Infineon/voltage-regulator-learning-platform/Version1.0/RedesignV1.0.xlsx

Redesign Vreg V1.0
Fault description | Date | Priority | Correction on the current board | Correction V1.1 | Corrected in V1.1 | Comment
Drain and Source of Q201 are reversed | 2021-06-03 | High | Cut some traces and rewire correctly. See "RetrofitsV1.0" | Flip Q201 in Schematic and correct it in the layout | 2021-06-08
Switch1-3 don't turn Q740, Q742, Q744 completely off. This is because R740 and R750 (and the others respectively) form an undesired voltage divider | 2021-06-03 | Nice to have | Reduce R750-R752 to 4k7 | Same | 2021-06-19 | Uth,min=0.3V -> Rmax=10k -> 4k7 leaves enough margin
Reverse leakage current through D506 has significant influence on In_Curr_Filtr and Out_curr_Filtr | 2021-06-06 | High | Change R506 and R507 to 100k and C506 and C507 to 2.2uF | Same | 2021-06-19 | Board2: Used 1uF 200k because I didn't have 2.2uF
If only the Arduino is powered, it still outputs 5V at its Vin Pin which in turn causes the logic supply of the board to turn on | 2021-06-06 | High | Insert diode in the supply line of the Arduino. See "RetrofitsV1.0" | Same | 2021-06-19
If JP124 is open, boost_cntrl is floating | 2021-06-06 | Nice to have | Move R123 from Boost_Cntrl_indep to Boost_Cntrl. See "RetrofitsV1.0" | Same | 2021-06-08
If only the Arduino is powered and Buck_Cntrl or Boost_Cntrl are switched to 1, the freewheeling diode at the gate drivers IN will conduct and supply 5V to the 12V rail (applies only after diode has been inserted into Arduino supply line). | 2021-06-06 | High | Insert 4k7 resistor directly at the respective IN Pins of the Gate drivers. Also add external clamping diodes to IN Pins (GND and 12V). See "RetrofitsV1.0" | Same | 2021-07-05 | Board 2: MBR120ESFT1G I used for clamping has high leakage current, thus waveforms look ugly.
If Boost_Cntrl is permanently 1, the Boost Stage goes into shutdown due to undervoltage at VB. This is because if Vout is not very high, the Charge pump does not have a sufficient supply voltage to charge C432 | 2021-06-06 | High | Supply Chargepump with VS_Boost or 12V, whichever is higher (2 Diodes). Clamp voltage across C432 with 15 Zener. See "RetrofitsV1.0" | Same | 2021-06-08 | See LTSpice Simulation. I was a bit concerned about the power dissipation in the zener diode at high Vout, but it seems to be fine.
If Buck_Cntrl or Boost_Cntrl are 1 during startup, the respective gate driver is disabled until the line is pulled low once. | 2021-06-08 | High | Add a Diode connected to a 2.2uF cap that is slowly charged through a 4k7 resistor connected to 3V3. For the boost use 2k2 (such that boost gets high before buck). See "RetrofitsV1.0" | Same | 2021-07-05 | Board 2: Had to change to 1uF because the inline resistor was changed to 4k7 Consider changing the resistor on the boost stage to 1.3k, so 5V at the buck and 3.3V at the boost is no problem
Old Inductor Values in the schematic | 2021-06-01 | High | Change L420 to 27uH (7447709270) and L421 to 15uH (SRP6060FA-150M) | Same | 2021-06-08
U500 is delivering wrong output values because the input goes higher than 1.3V (p.11 of the Datasheet: "When choosing the input voltage range, the input common-mode voltage range (VICR) must be taken in to account. VICR can range from 0 V to VCC– 2 V. This limits the input voltage range to as high as VCC– 2 V and as low as 0 V. Operation outside of this range can yield incorrect comparisons.") | 2021-06-08 | High | Change supply voltage of U500 to 12V. See "RetrofitsV1.0" | Change supply voltage of U500 AND U520 to 12V | 2021-06-19
If an over-voltage event occurs without output load, the output and VS only discharge down to 5V. This causes the Buck Gate Driver to be unable to turn on (UVLO). This is caused by the new chargepump circuit on the boost stage. Is has an input voltage of 12V, thus it could boost up to 24V. However, the 15 Zener limits that. The current through the zener causes Vs_Boost to rise until an equilibrium is found at approx. 5V. Use resistor at the output to bring the voltage down: 1k 0.7V; 3k3 1.6V; 4k7 2V | 2021-06-08 | High | Connect a 3k3 resistor between VS_Buck and GND | Connect two 2k2 resistors in series (->4k4) between VS_Buck and GND | 2021-06-19 | Probably a bit more than 3k3 would be fine too
Just an information: Disconnected external NTC does NOT cause an over temperature event. A grounded ext. NTC however would cause one | 2021-06-08 | Optional | None | Correct note in the schematic | 2021-06-09
At the Control Header there should be Vout instead of Vout_M. Vin_M does not need to be there | 2021-06-09 | High | Cut trace of Vout_M, rewire | Use Vout instead of Vout_M and correct silkscreen. Remove Vin_M | 2021-07-05 | Somehow I didn't sent the latest version of the schematic to the manufacturer
Vin and Vout are too strongly filtered | 2021-06-09 | High | Reduce C211 and C722 to 1nF | Reduce C211 and C722 to 1nF | 2021-06-19 | The filter frequency is 1/(2pi(R1||R2)C)
D506 is not needed (The upper end of the commonmode voltage range is VCC+ – 1.5 V; however, one input can exceed VCC, and the comparator will provide a proper output state as long as the other input remains in the common-mode range. Either or both inputs can go to 30 V without damage.) | 2021-06-20 | Nice to have | - | Remove D506 | 2021-07-05
On the XMC Boards, Aref is an output, not an input (AHHHHH). Therefore, the 3.3 V sensors on the board will be damaged if an 5 V XMC Board is connected and the Aref jumper is closed | 2021-07-05 | High | None. Just pay attention, that the AREF jumper is pulled! | Build an ideal diode at the AREF input | 2021-07-05 | The original Arduino has a 32k resistor between AREF and ground.
The XMC4700 Board does not have a Vin Pin. Therefore, it is not powered in the current configuration | 2021-07-05 | Nice to have | None | None | - | If you want to use this board, power it via USB or connect 12V to its 5V Pin.
Add a User-Potentiometer | 2021-07-05 | Nice to have | - |  | 2021-07-05
