Infineon/voltage-regulator-learning-platform/Version1.1/RedesignV1.1.xlsx

Redesign Vreg V1.1
Fault description | Date | Priority | Correction on the current board | Correction V1.2 | Corrected in V1.2 | Comment
X723 should be named JP723 | 2021-07-30 | Optional | None | Change Designator | 2021-08-04
Add a Testpoint for the Output Voltage | 2021-07-30 | Nice to have | None | Add Testpoint | 2021-08-04
Charge pump makes an awful high-frequency noise | 2021-07-30 | Nice to have | None | None | No | What you are hearing is a beat (Schwebung) of the two individual switching frequencies. Even increasing the switching frequency cannot eliminate this problem.
Ideal Diode not working | 2021-07-30 | High | None | Remove it, as all parts can tolerate 5V anyways | 2021-08-04
Add Testpoints for Buck_Cntrl and Boost_Cntrl | 2021-08-02 | Nice to have | None |  | 2021-08-04
