Infineon/voltage-regulator-learning-platform/Version1.2/RedesignV1.2.xlsx

Redesign Vreg V1.2
Fault description | Date | Priority | Correction on the current board | Correction V1.3 | Corrected in V1.3 | Comment
Silkscreen on the back side with pin descriptions is not readable when the Arduino is pluggend in | 2021-10-10 | Nice to have | None | Move Silkscreen
Add testpoints for UserLEDs (or at least UserLED4) | 2021-10-10 | Nice to have | None
On Board 3 the buck test fails because boost stage goes into shutdown. However, this is pretty much no problem in real-world applications. Apparently this only happens on boards where the ICM555 is from Renesas. The ones with a Maxim ICM555 don't show this behaviour. | 2021-10-10
Change R723 to 10nF for better filtering | 2021-10-13 | Nice to have | Change the capacitor value | Change the capacitor value | 2021-10-13
5 V output is unprotected | 2021-10-15 | Optional | None
