Infineon/voltage-regulator-learning-platform/PCBV3/PCBV3.png

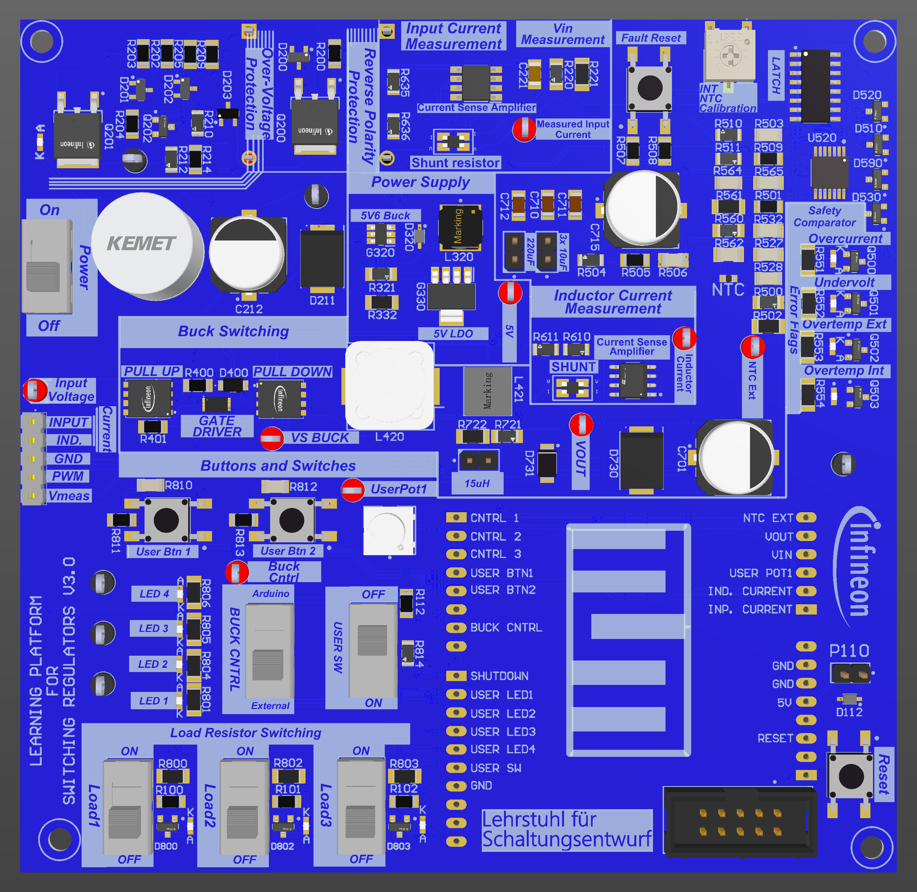
PCBV3/PCBV3.png
