Infineon/voltage-regulator-learning-platform/Resources/LearningPlatforPeripherals.png

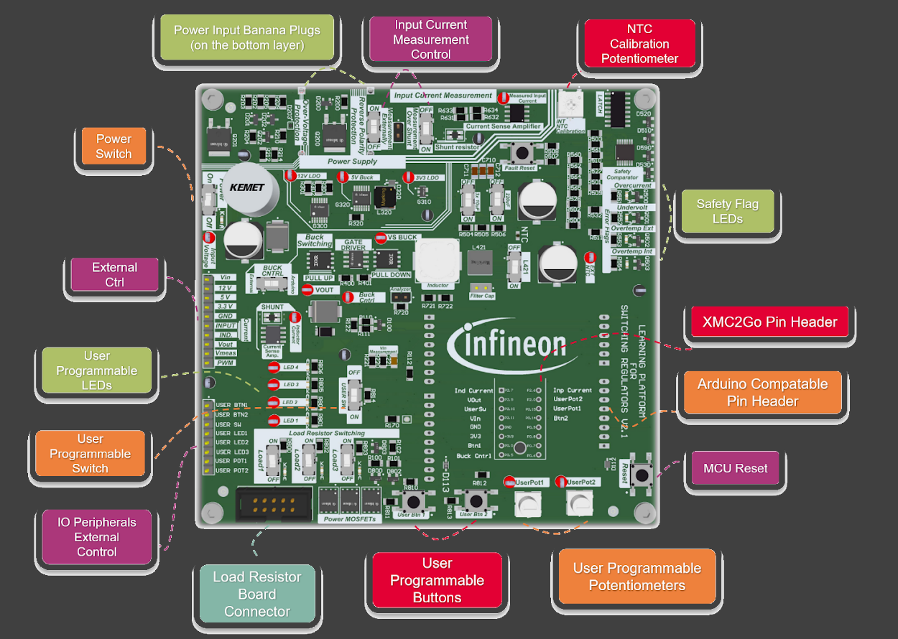
Resources/LearningPlatforPeripherals.png
