Infineon/voltage-regulator-learning-platform/Resources/TLI4970-Current-Sense-Shield2Go_Top_plain_neu.jpg_2104777148.png

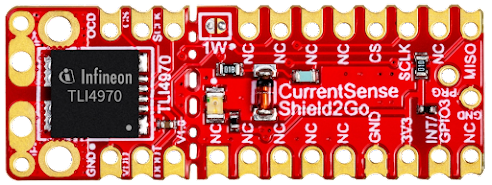
Resources/TLI4970-Current-Sense-Shield2Go_Top_plain_neu.jpg_2104777148.png
