Infineon/voltage-regulator-learning-platform/Version2.2/Project Outputs for Learning Platform/PDF/5V.jpg

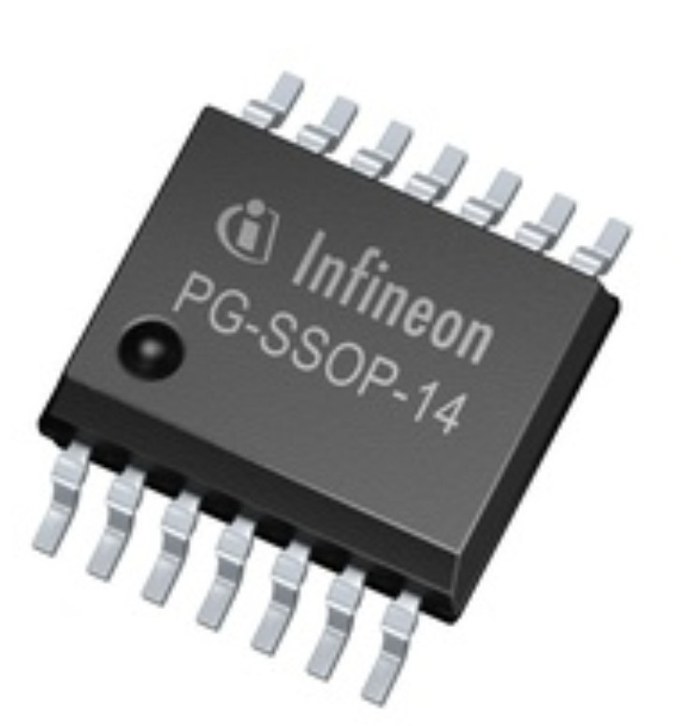
Version2.2/Project Outputs for Learning Platform/PDF/5V.jpg
