Infineon/voltage-regulator-learning-platform/Version1.0/Project Outputs/PDF/Schematic Prints.PDF

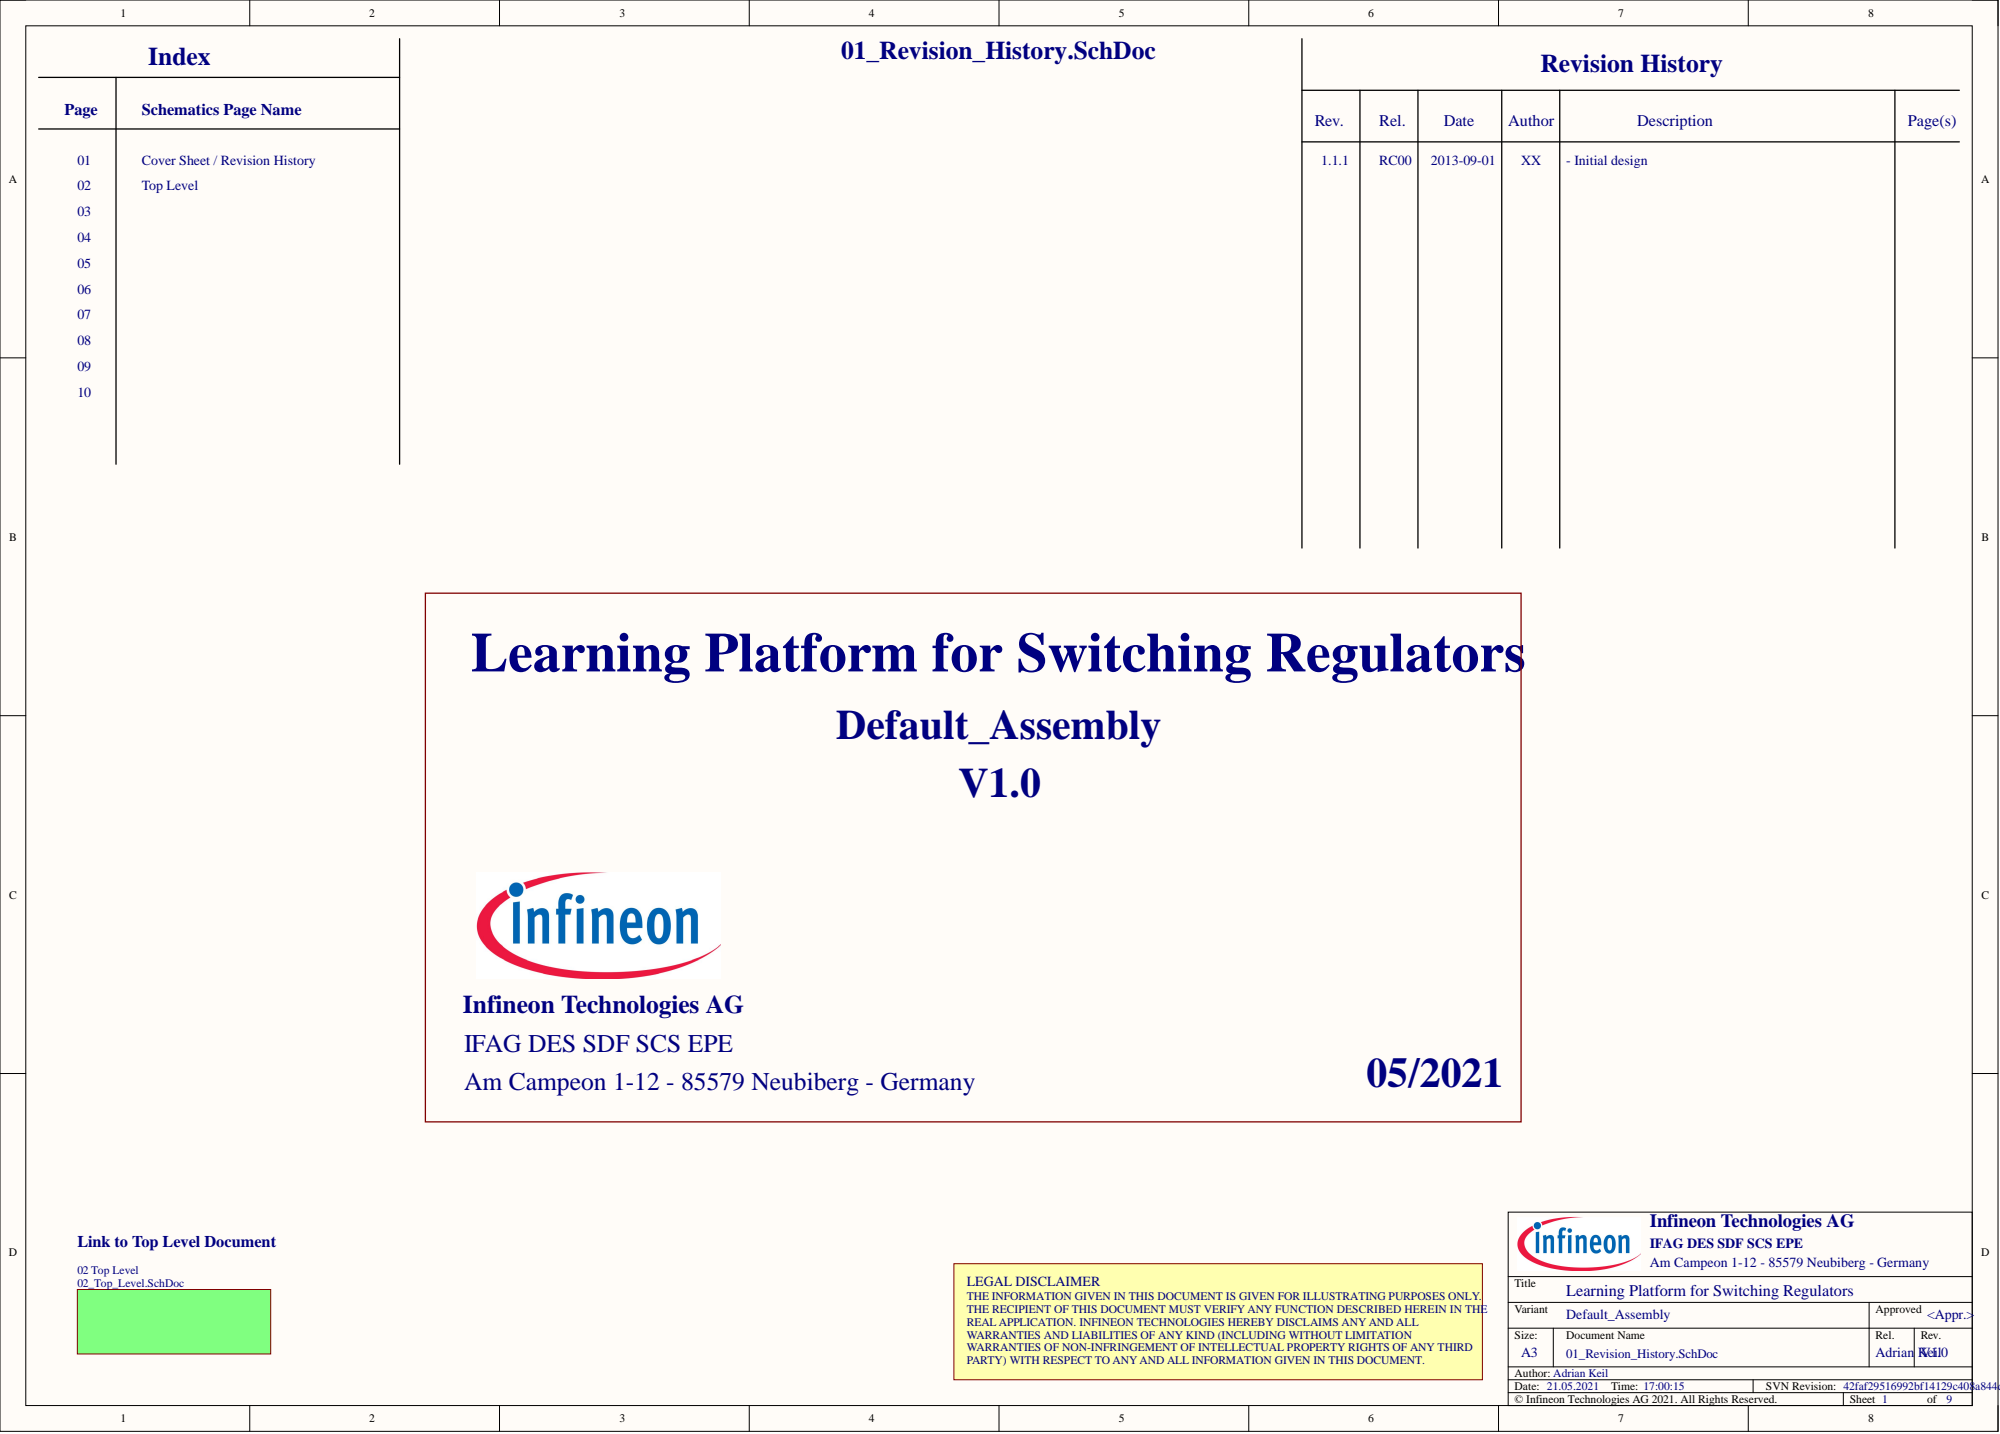
[picture p42: page 1]

Cover Sheet / Revision History

Learning Platform for Switching Regulators

Infineon Technologies AG
IFAG DES SDF SCS EPE
Am Campeon 1-12 - 85579 Neubiberg - Germany

Link to Top Level Document

LEGAL DISCLAIMER
THE INFORMATION GIVEN IN THIS DOCUMENT IS GIVEN FOR ILLUSTRATING PURPOSES ONLY.
THE RECIPIENT OF THIS DOCUMENT MUST VERIFY ANY FUNCTION DESCRIBED HEREIN IN THE
REAL APPLICATION. INFINEON TECHNOLOGIES HEREBY DISCLAIMS ANY AND ALL
WARRANTIES AND LIABILITIES OF ANY KIND (INCLUDING WITHOUT LIMITATION
WARRANTIES OF NON-INFRINGEMENT OF INTELLECTUAL PROPERTY RIGHTS OF ANY THIRD
PARTY) WITH RESPECT TO ANY AND ALL INFORMATION GIVEN IN THIS DOCUMENT.

Variant Default_Assembly | Approved <Appr.>

Size: A3 | Document Name 01_Revision_History.SchDoc | Rel. Adrian Keil | Rev. V1.0

Date: 21.05.2021 Time: 17:00:15
© Infineon Technologies AG 2021. All Rights Reserved. | Sheet of

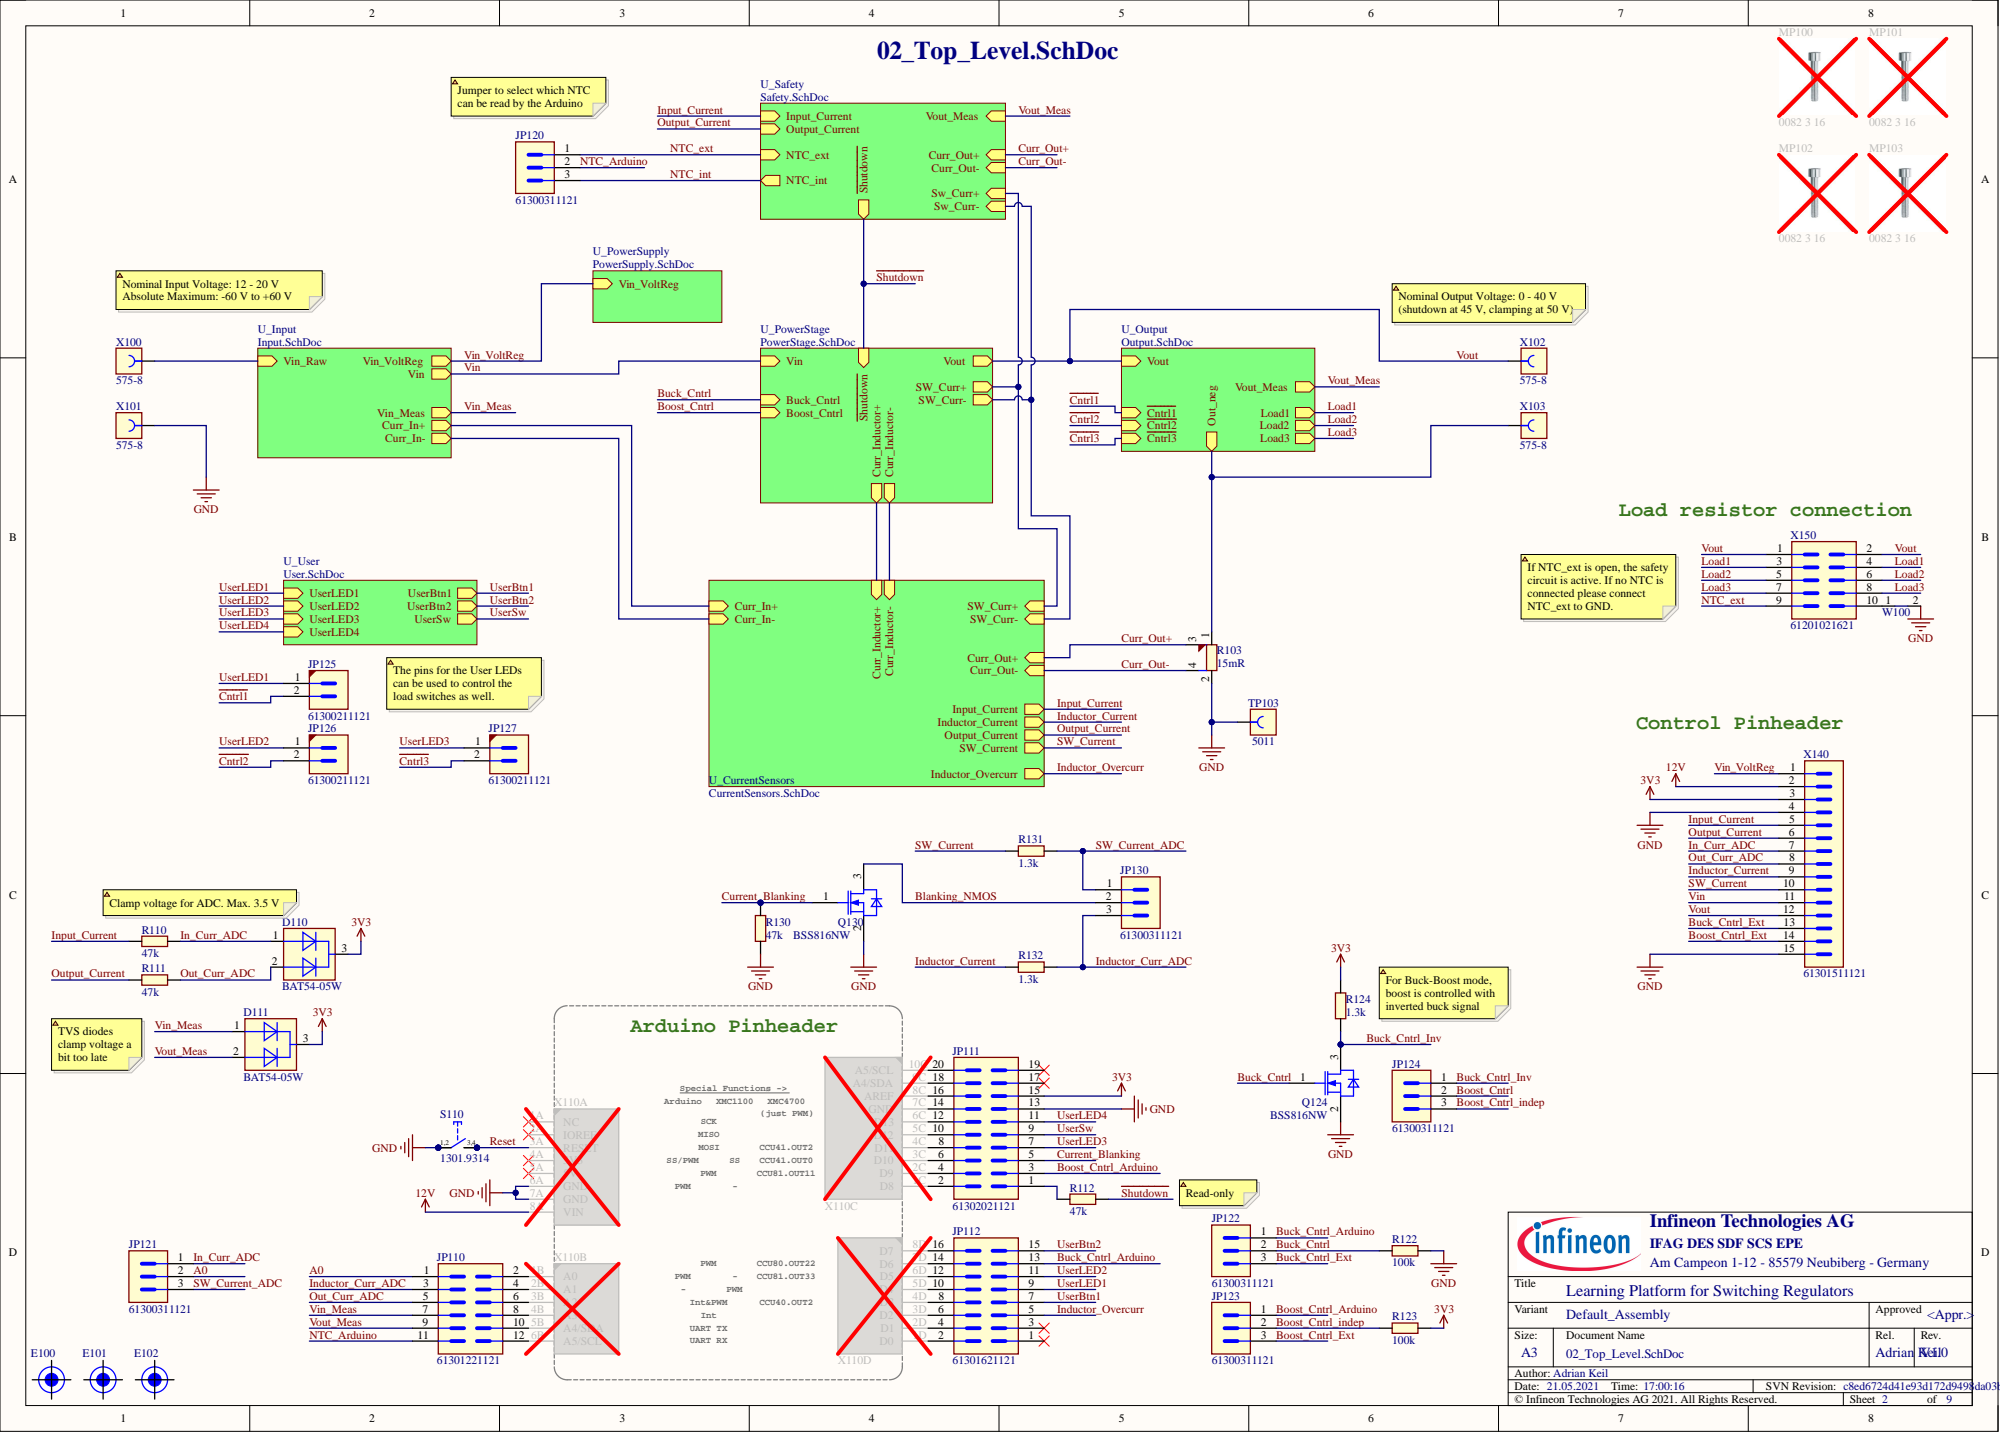
[picture p43: page 2]

Jumper to select which NTC
can be read by the Arduino

(shutdown at 45 V, clamping at 50 V)

If NTC_ext is open, the safety
circuit is active. If no NTC is
connected please connect
NTC_ext to GND.

The pins for the User LEDs
can be used to control the
load switches as well.

Clamp voltage for ADC. Max. 3.5 V

For Buck-Boost mode,
boost is controlled with
inverted buck signal

Infineon Technologies AG
IFAG DES SDF SCS EPE
Am Campeon 1-12 - 85579 Neubiberg - Germany

Learning Platform for Switching Regulators

SVN Revision: c8ed6724d41e93d172d9498da03b9148988799ea [Locally Modified]

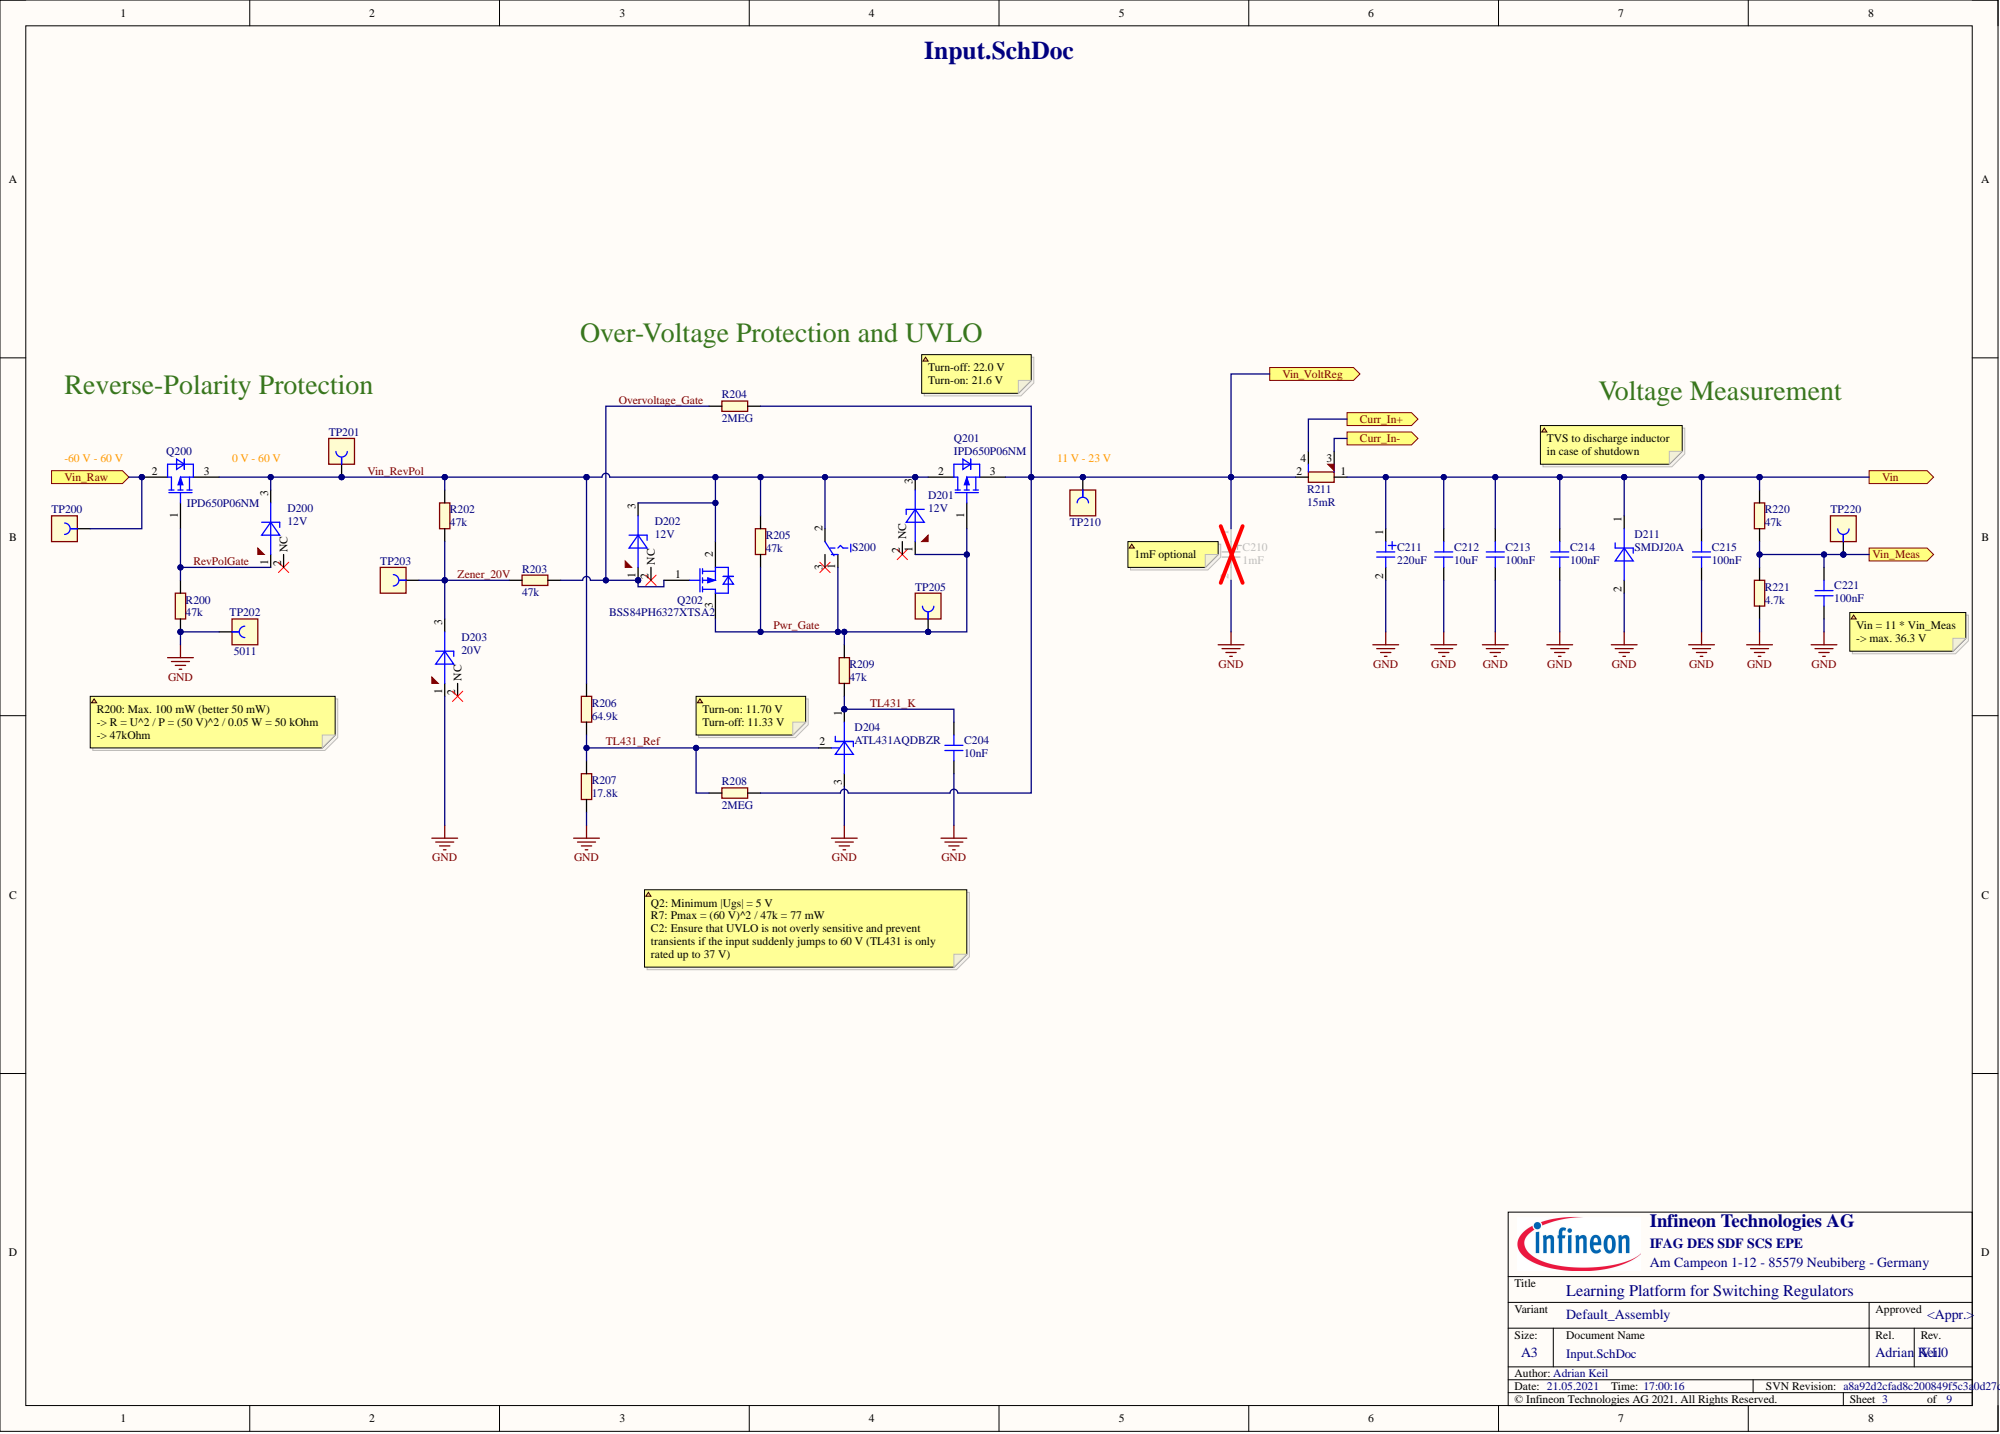
[picture p44: page 3]

Over-Voltage Protection and UVLO

Turn-off: 22.0 V Turn-on: 21.6 V
D204 ATL431AQDBZR2

TVS to discharge inductor
in case of shutdown

Turn-on: 11.70 V Turn-off: 11.33 V

Q2: Minimum |Ugs| = 5 V
R7: Pmax = (60 V)^2 / 47k = 77 mW
C2: Ensure that UVLO is not overly sensitive and prevent
transients if the input suddenly jumps to 60 V (TL431 is only
rated up to 37 V)

Infineon
IFAG DES SDF SCS EPE
Am Campeon 1-12 - 85579 Neubiberg -

Learning Platform for Switching Regulators

Variant y Default_Assembl | Approved <Appr . >

Size: A | Input.Sch D o c | Rev . V1.

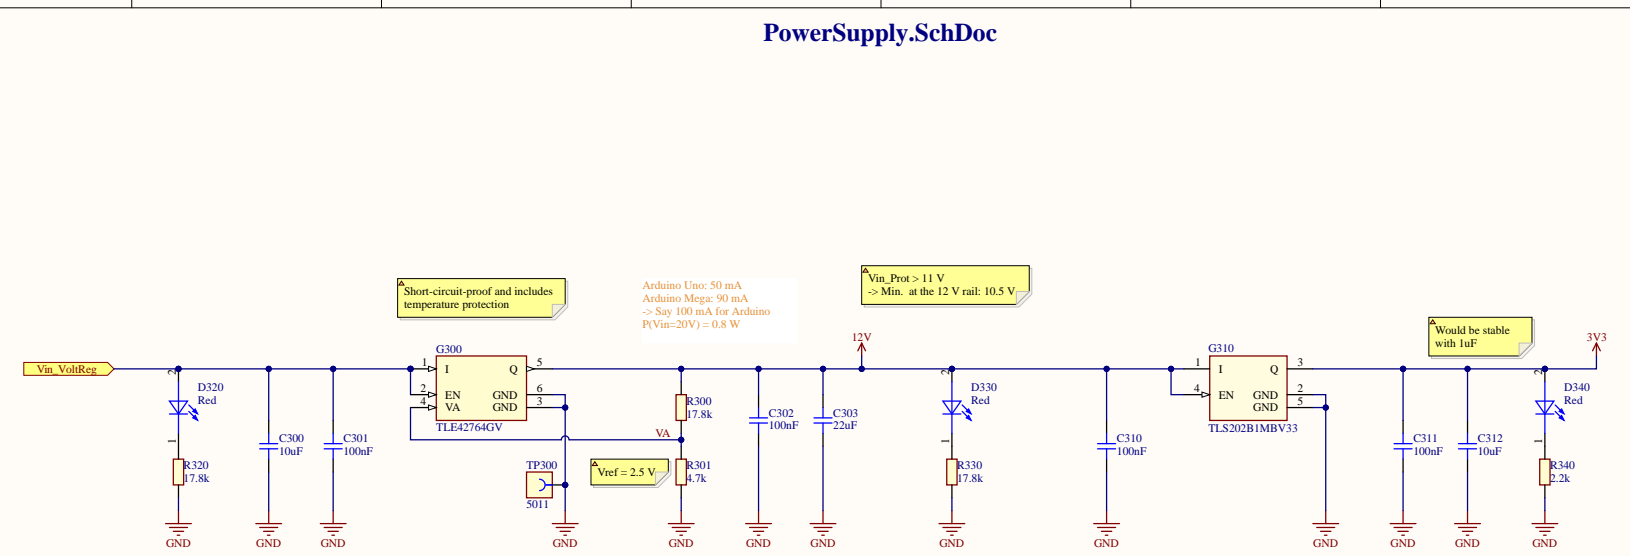
[picture p45: page 4]

Vin_Prot > 11 V
-> Min. at the 12 V rail: 10.5 V

Short-circuit-proof and includes
temperature protection

Arduino Uno: 50 mA
Arduino Mega: 90 mA
-> Say 100 mA for Arduino
P(Vin=20V) = 0.8 W

Infineon
IFAG DES SDF SCS EPE
Am Campeon 1-12 - 85579 Neubiberg -

Learning Platform for Switching Regulators

Variant y Default_Assembl | Approved <Appr . >

Size: A | PowerSupply.Sch D o c | Rev . V1.

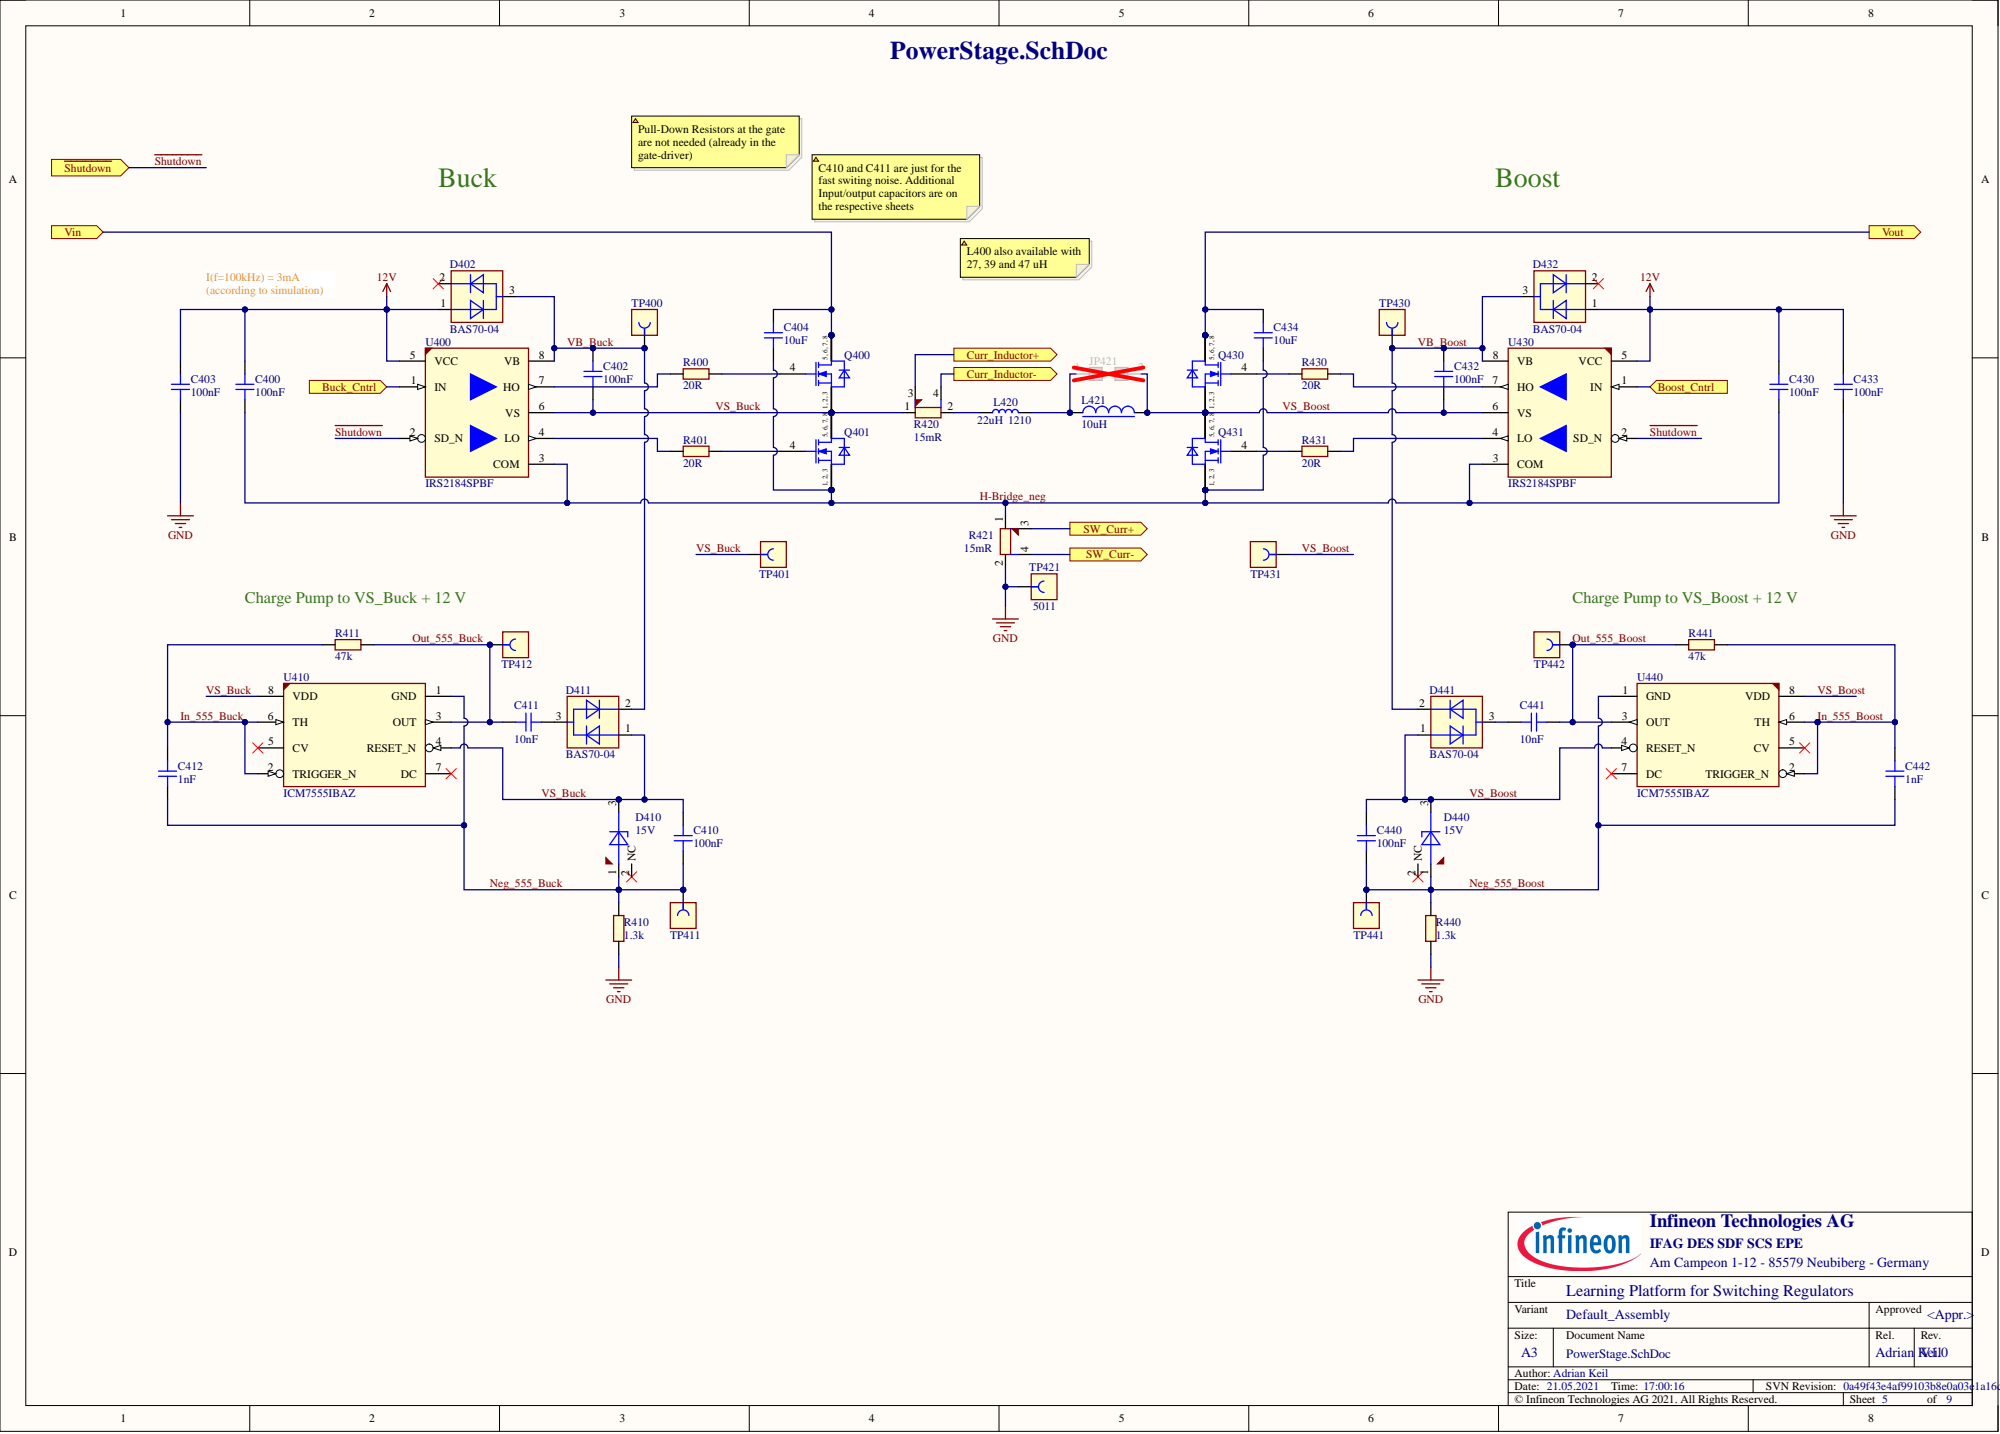
[picture p46: page 5]

Pull-Down Resistors at the gate
are not needed (already in the
gate-driver)

C410 and C411 are just for the
fast switing noise. Additional
Input/output capacitors are on
the respective sheets

10uF R430 | VB_Boost | U430

COM 3

Infineon Technologies AG
IFAG DES SDF SCS EPE
Am Campeon 1-12 - 85579 Neubiberg - Germany

Learning Platform for Switching Regulators

Variant Default_Assembly | Approved <Appr.>

PowerStage.SchDoc

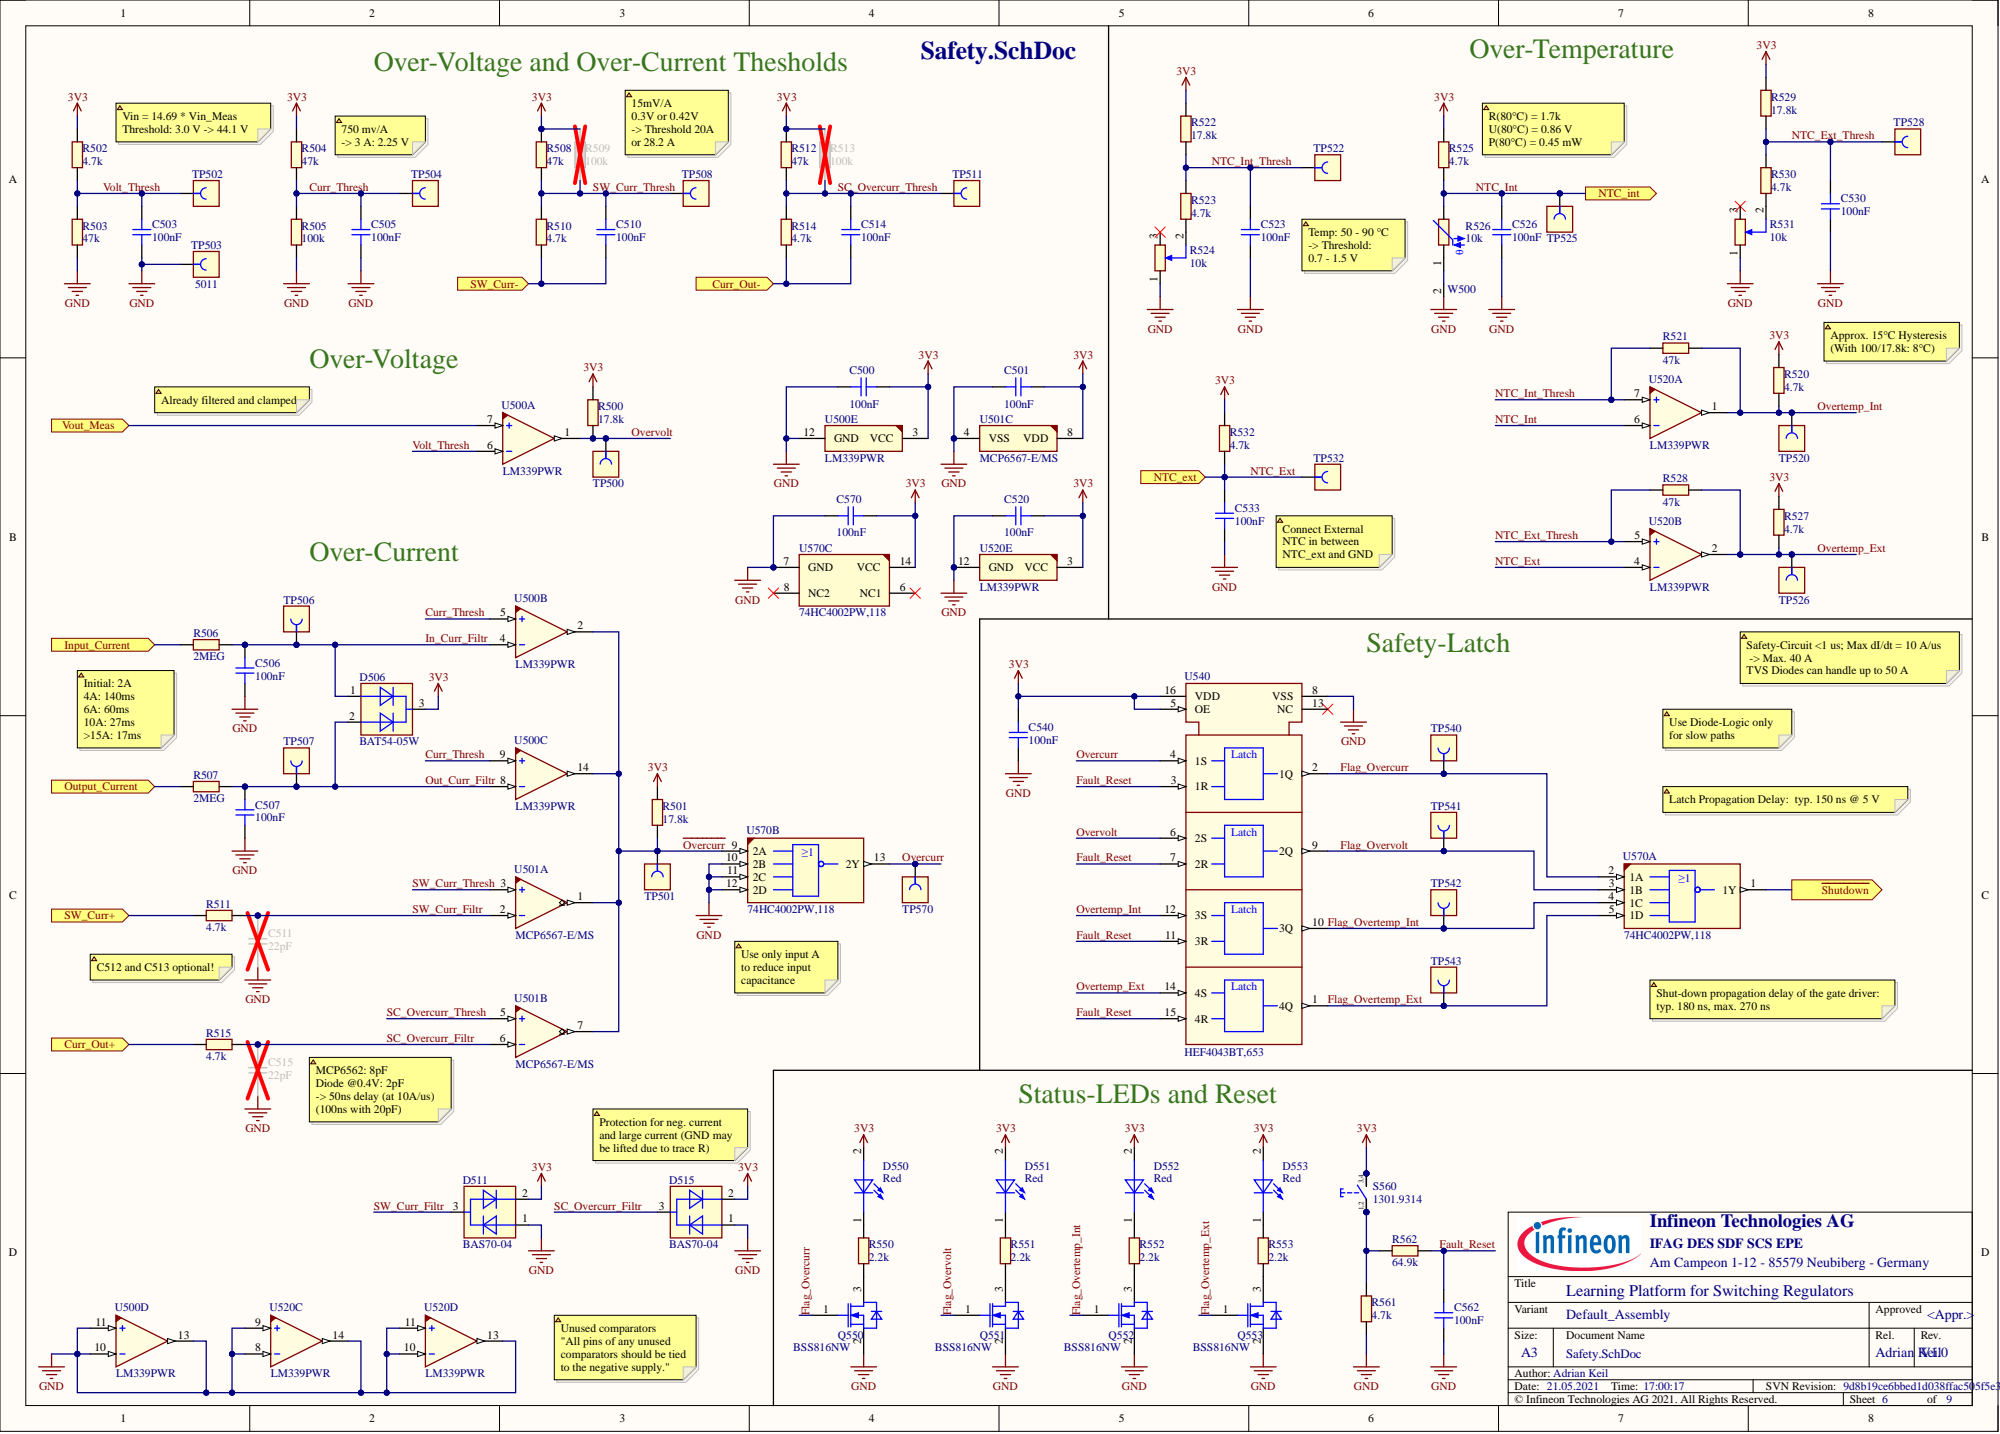
[picture p47: page 6]

Over-Voltage and Over-Current Thesholds

Already filtered and clamped

Safety-Circuit <1 us; Max dI/dt = 10 A/us
-> Max. 40 A
TVS Diodes can handle up to 50 A

Use Diode-Logic only
for slow paths

Latch Propagation Delay: typ. 150 ns @ 5 V

2B 10
2C 11

Flag_Overtemp_Int

Shut-down propagation delay of the gate driver:
typ. 180 ns, max. 270 ns

Status-LEDs and Reset

Protection for neg. current
and large current (GND may
be lifted due to trace R)

Infineon Technologies AG
IFAG DES SDF SCS EPE
Am Campeon 1-12 - 85579 Neubiberg - Germany

Learning Platform for Switching Regulators

Unused comparators
"All pins of any unused
comparators should be tied
to the negative supply."

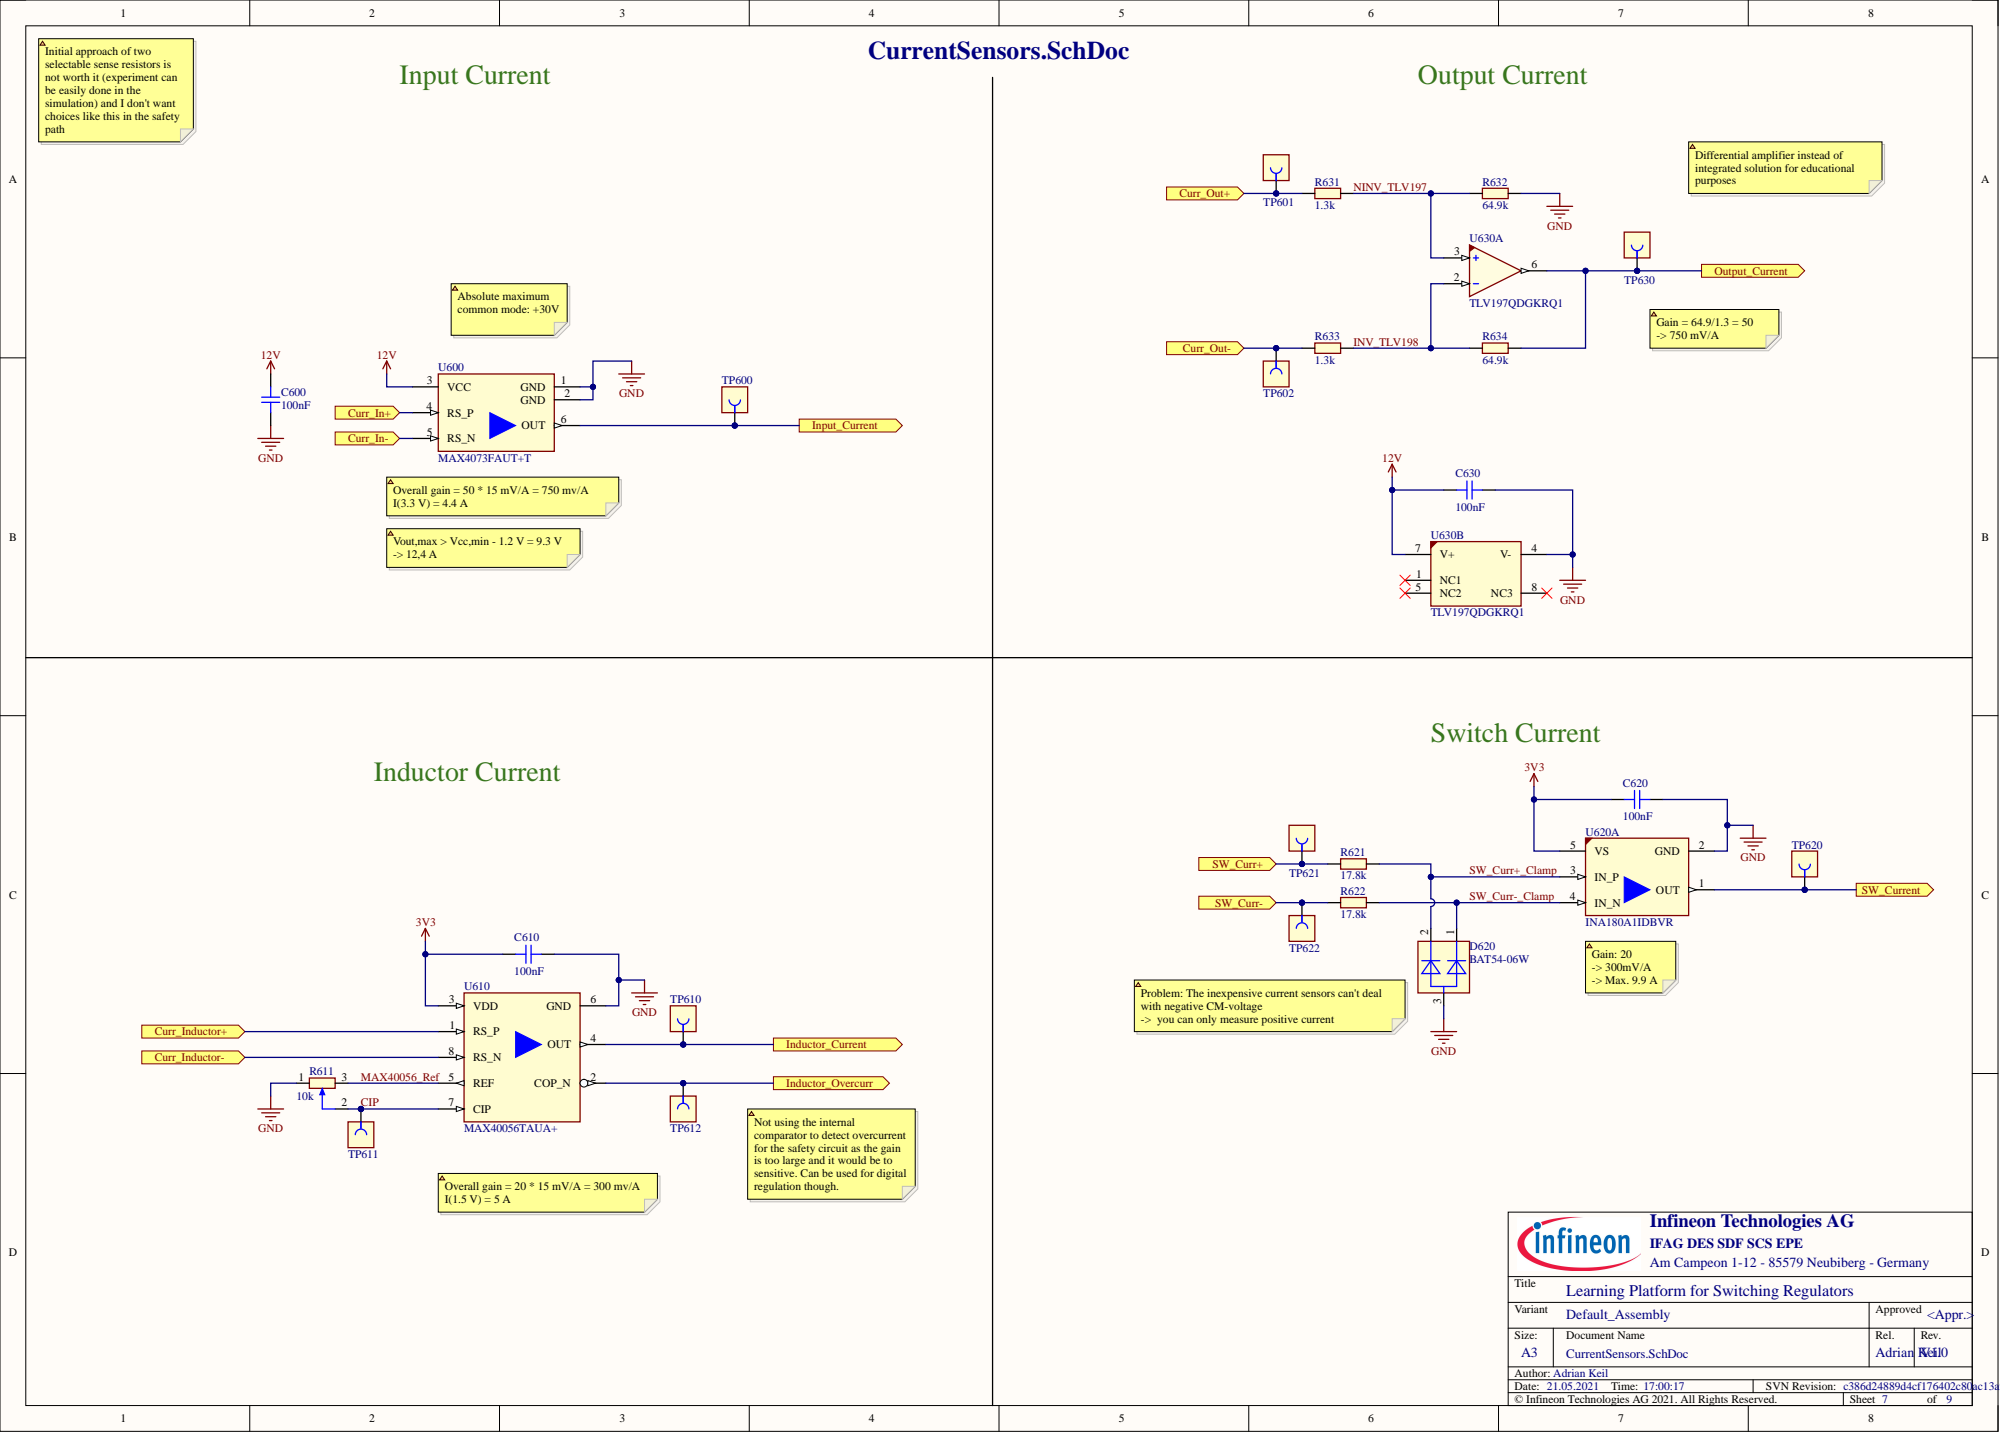
[picture p48: page 7]

Initial approach of two
selectable sense resistors is
not worth it (experiment can
be easily done in the
simulation) and I don't want
choices like this in the safety
path

Differential amplifier instead of
integrated solution for educational
purposes

Overall gain = 50 * 15 mV/A = 750 mv/A

Vout,max > Vcc,min - 1.2 V = 9.3 V

Problem: The inexpensive current sensors can't deal
with negative CM-voltage
-> you can only measure positive current

Not using the internal
comparator to detect overcurrent
for the safety circuit as the gain
is too large and it would be to
sensitive. Can be used for digital
regulation though.

Overall gain = 20 * 15 mV/A = 300 mv/A

Infineon Technologies AG
IFAG DES SDF SCS EPE
Am Campeon 1-12 - 85579 Neubiberg - Germany

Learning Platform for Switching Regulators

Variant Default_Assembly | Approved <Appr.>

CurrentSensors.SchDoc

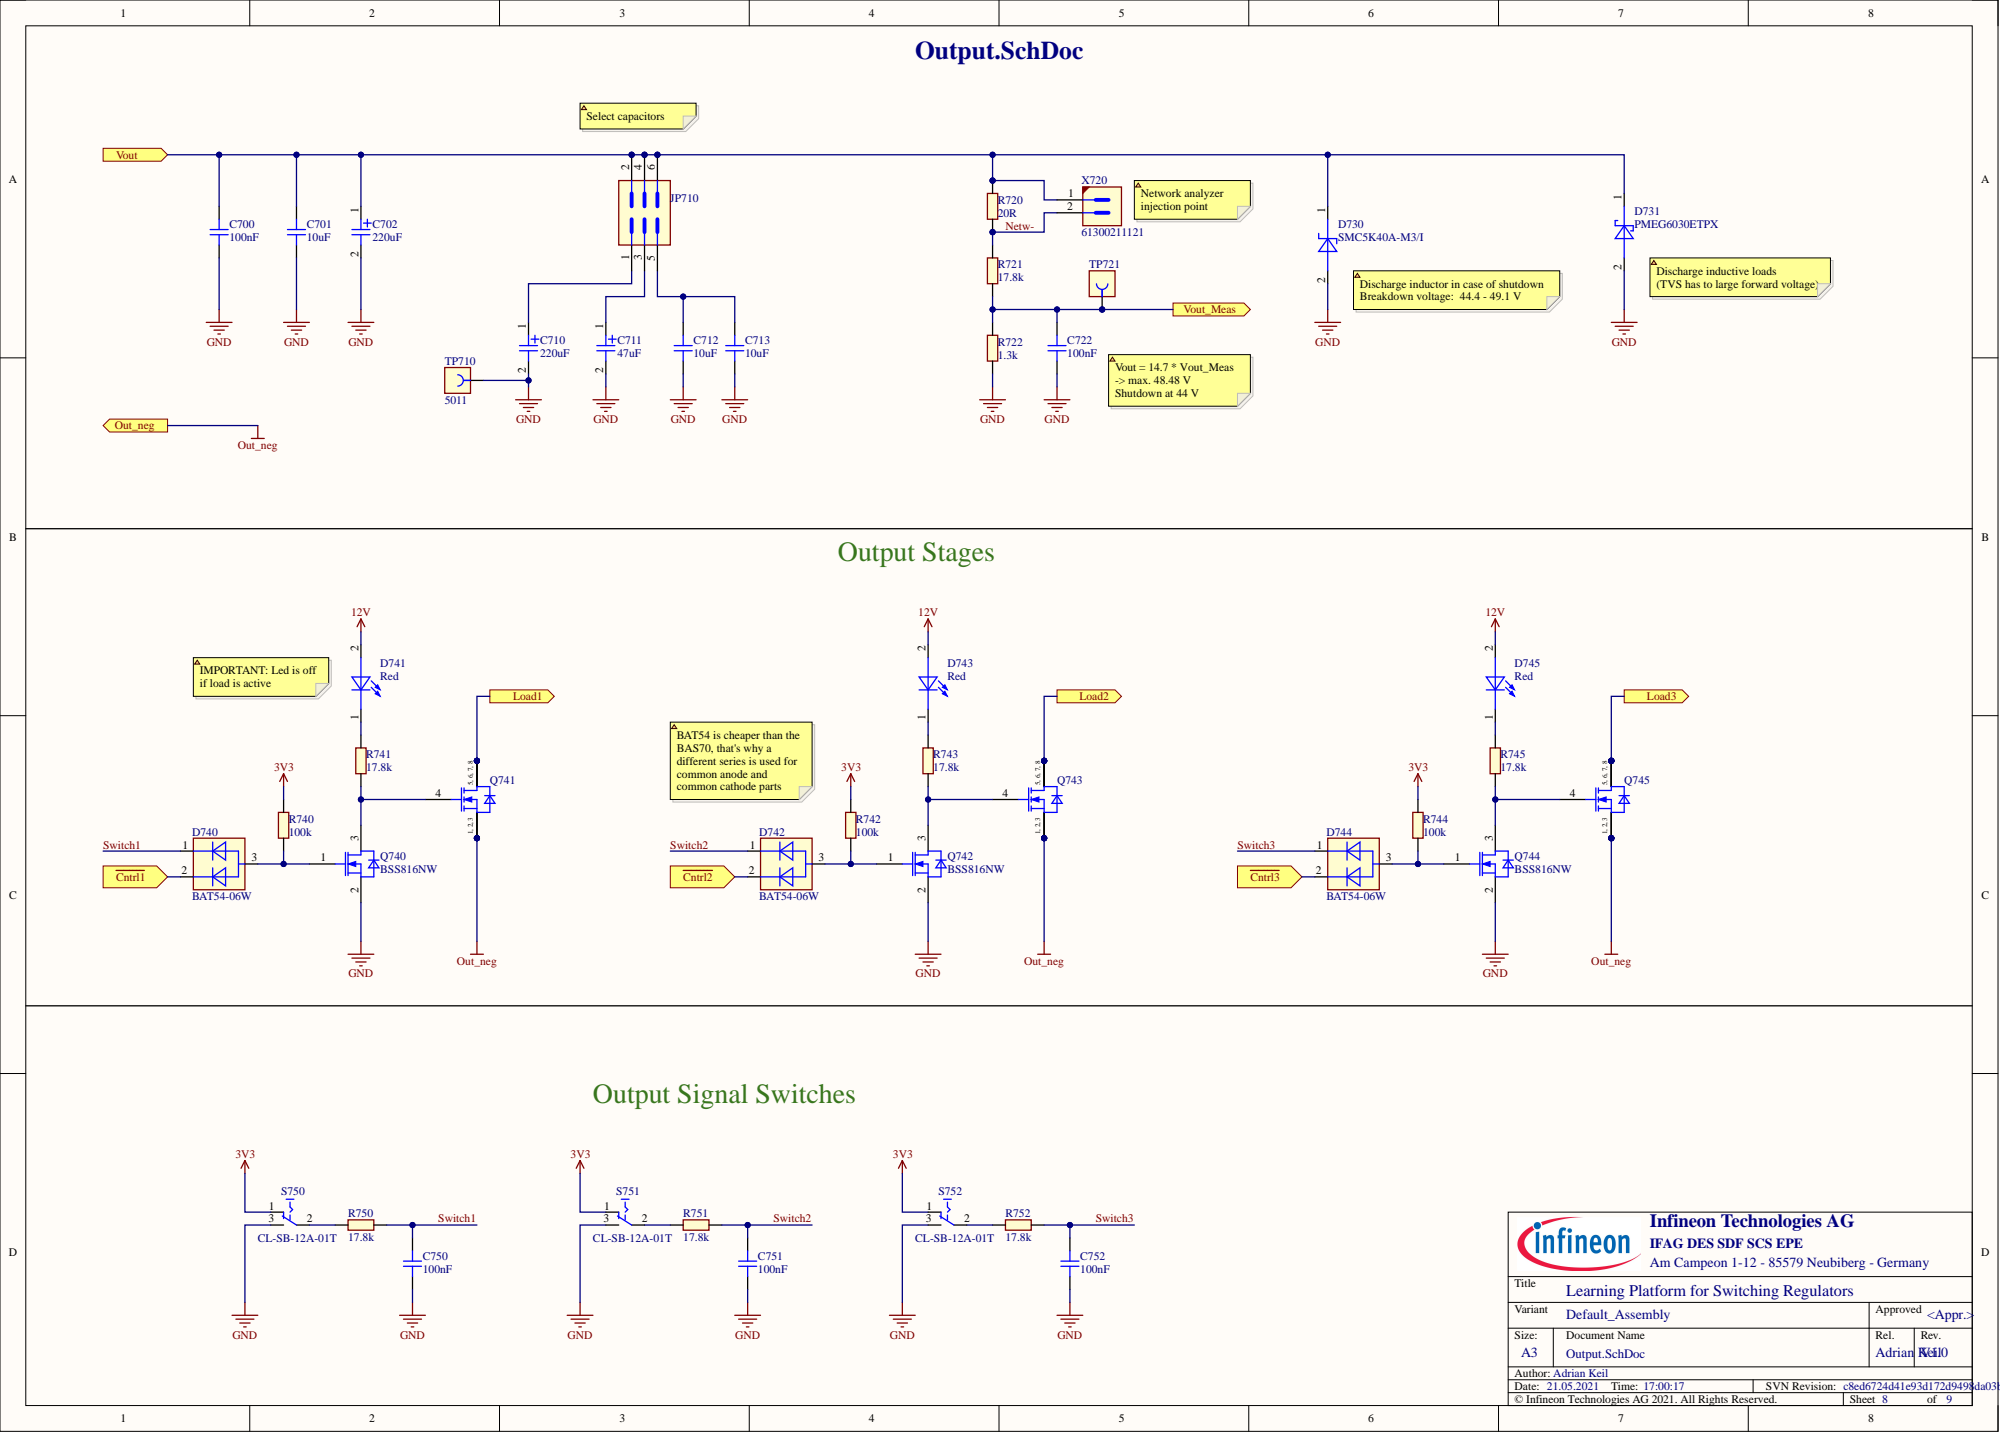
[picture p49: page 8]

IMPORTANT: Led is off
if load is active

BAT54 is cheaper than the
BAS70, that's why a
different series is used for
common anode and
common cathode parts

Infineon Technologies AG
IFAG DES SDF SCS EPE
Am Campeon 1-12 - 85579 Neubiberg - Germany

Learning Platform for Switching Regulators

Variant Default_Assembly | Approved <Appr.>

Output.SchDoc

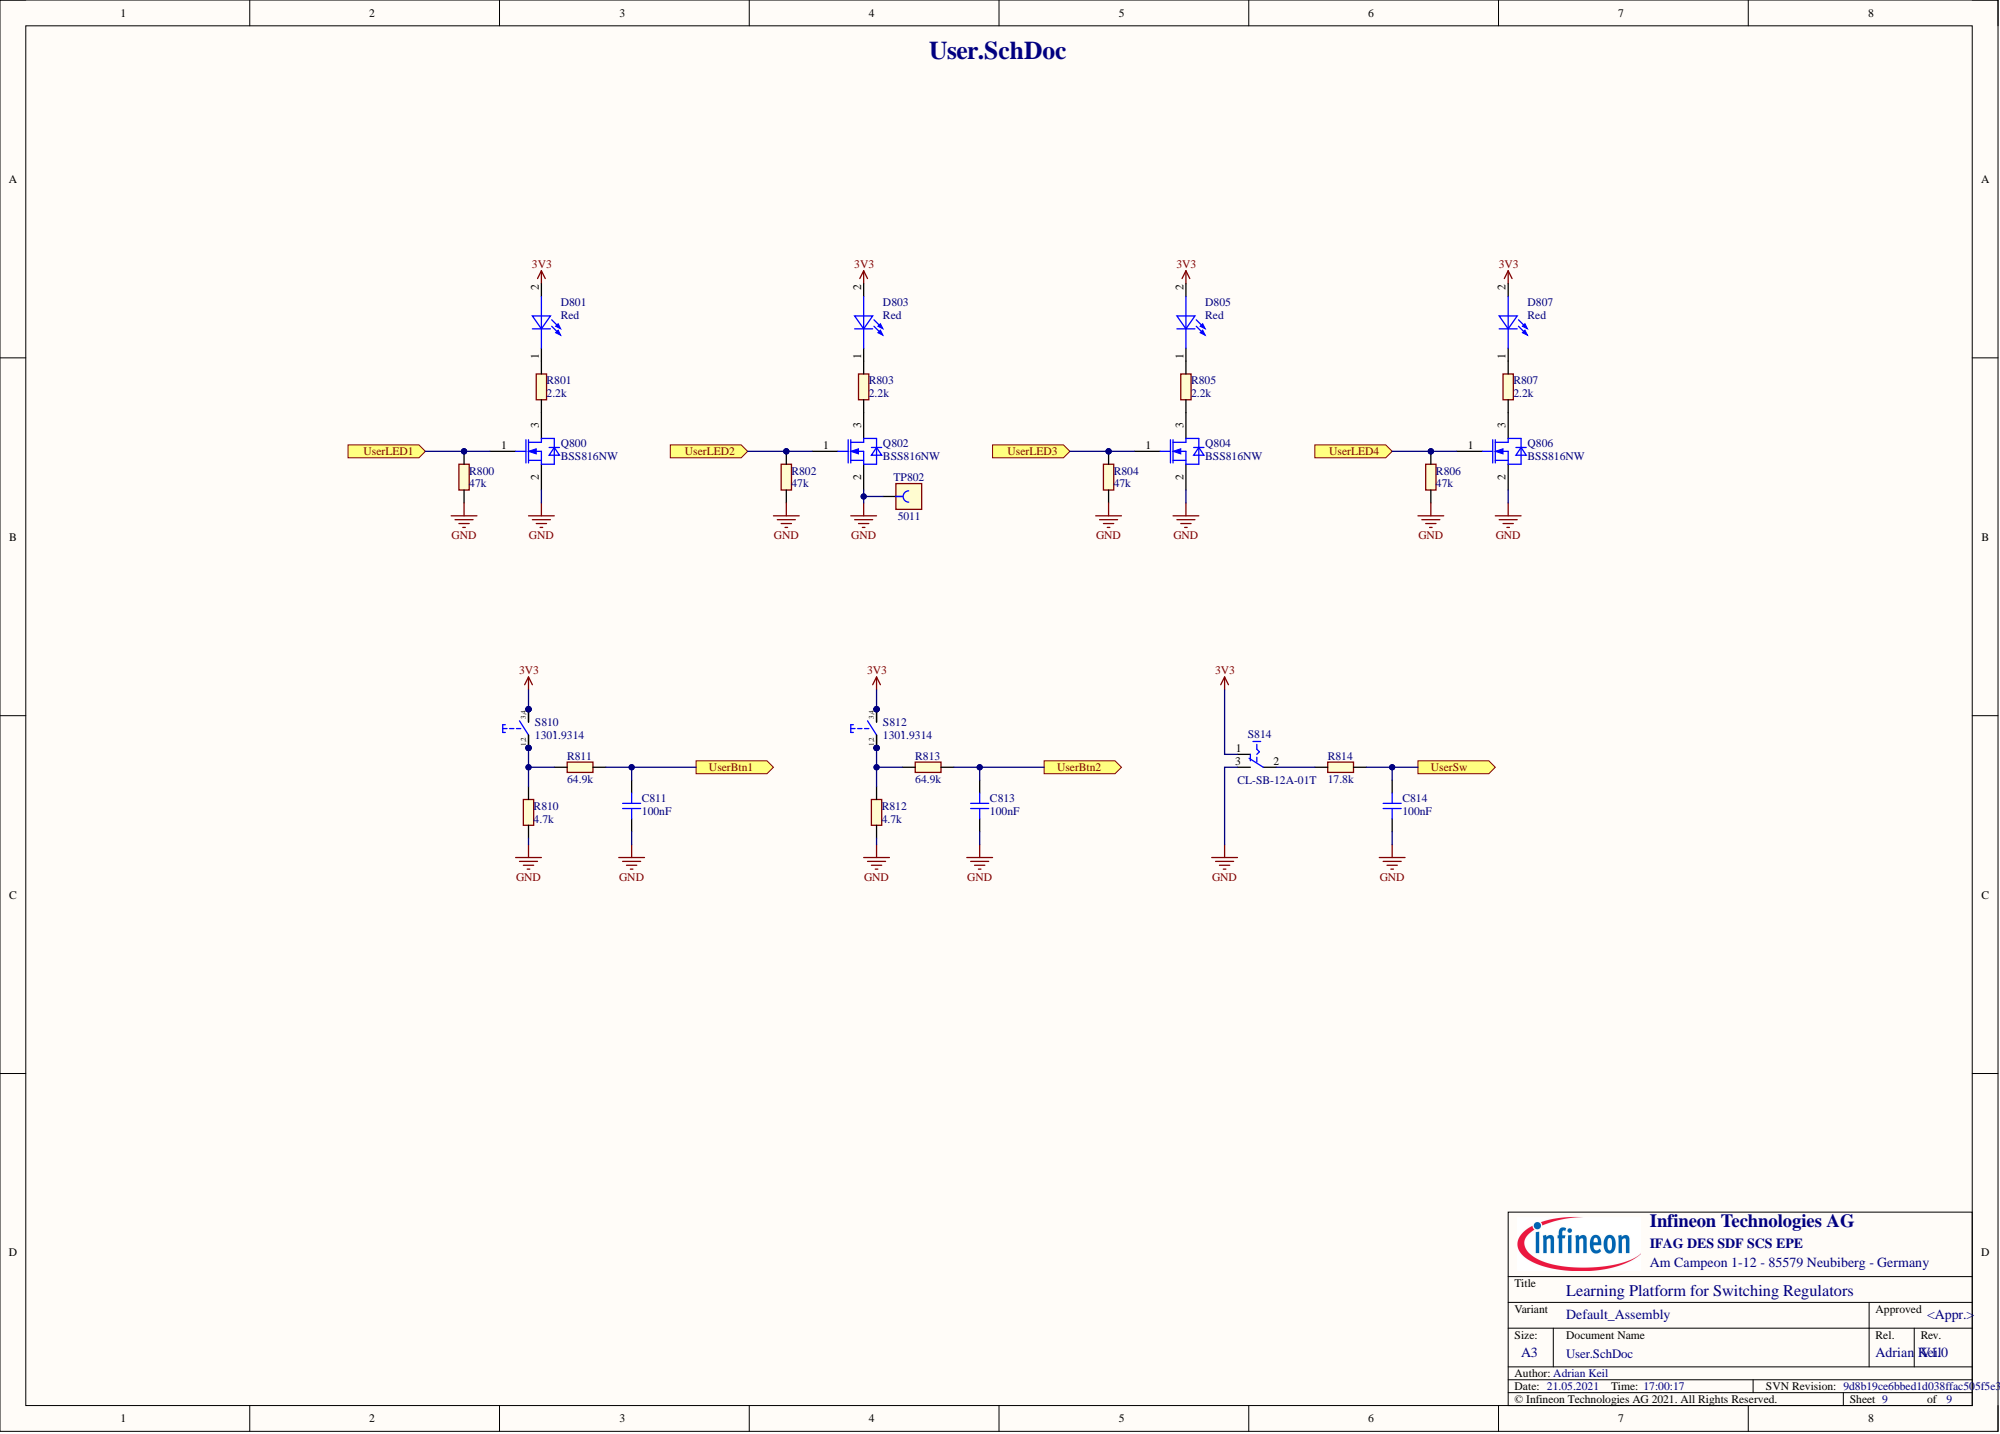
[picture p50: page 9]

Infineon Technologies AG
IFAG DES SDF SCS EPE
Am Campeon 1-12 - 85579 Neubiberg - Germany

Learning Platform for Switching Regulators

Variant Default_Assembly | Approved <Appr.>

User.SchDoc
