Infineon/voltage-regulator-learning-platform/Version1.2/Project Outputs/PDF/Schematic Prints.PDF

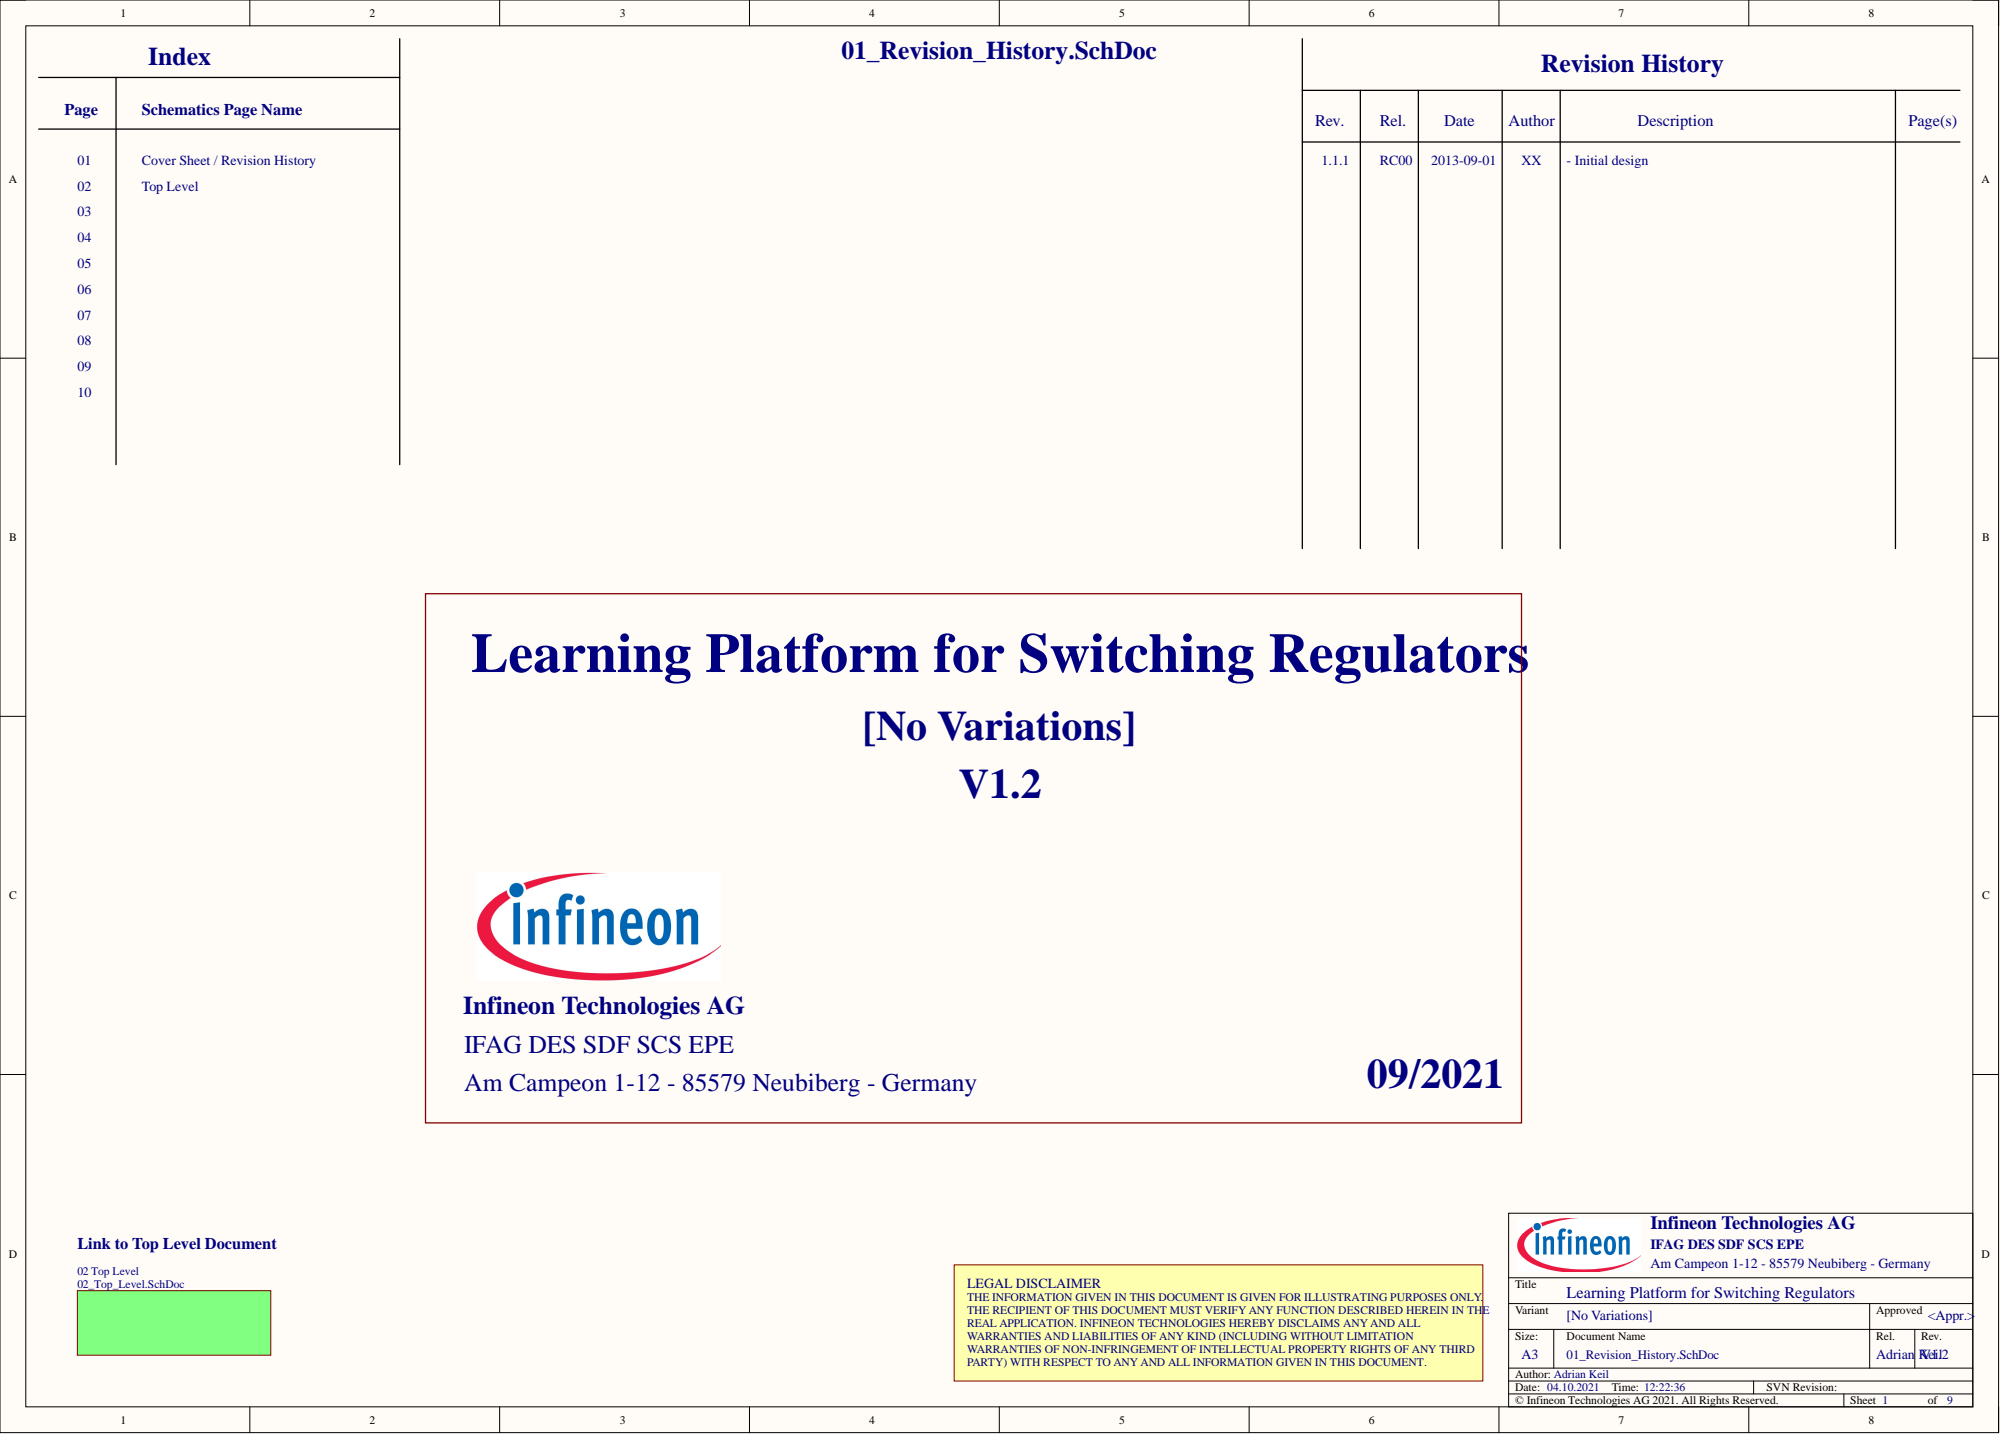
[picture p60: page 1]

Cover Sheet / Revision History

Learning Platform for Switching Regulators

Infineon Technologies AG
IFAG DES SDF SCS EPE
Am Campeon 1-12 - 85579 Neubiberg - Germany

Link to Top Level Document

LEGAL DISCLAIMER
THE INFORMATION GIVEN IN THIS DOCUMENT IS GIVEN FOR ILLUSTRATING PURPOSES ONLY.
THE RECIPIENT OF THIS DOCUMENT MUST VERIFY ANY FUNCTION DESCRIBED HEREIN IN THE
REAL APPLICATION. INFINEON TECHNOLOGIES HEREBY DISCLAIMS ANY AND ALL
WARRANTIES AND LIABILITIES OF ANY KIND (INCLUDING WITHOUT LIMITATION
WARRANTIES OF NON-INFRINGEMENT OF INTELLECTUAL PROPERTY RIGHTS OF ANY THIRD
PARTY) WITH RESPECT TO ANY AND ALL INFORMATION GIVEN IN THIS DOCUMENT.

Variant [No Variations] | Approved <Appr.>

Size: A3 | Document Name 01_Revision_History.SchDoc | Rel. Adrian Keil | Rev. V1.2

Date: 04.10.2021 Time: 12:22:36 | SVN Revision:
© Infineon Technologies AG 2021. All Rights Reserved. | Sheet of

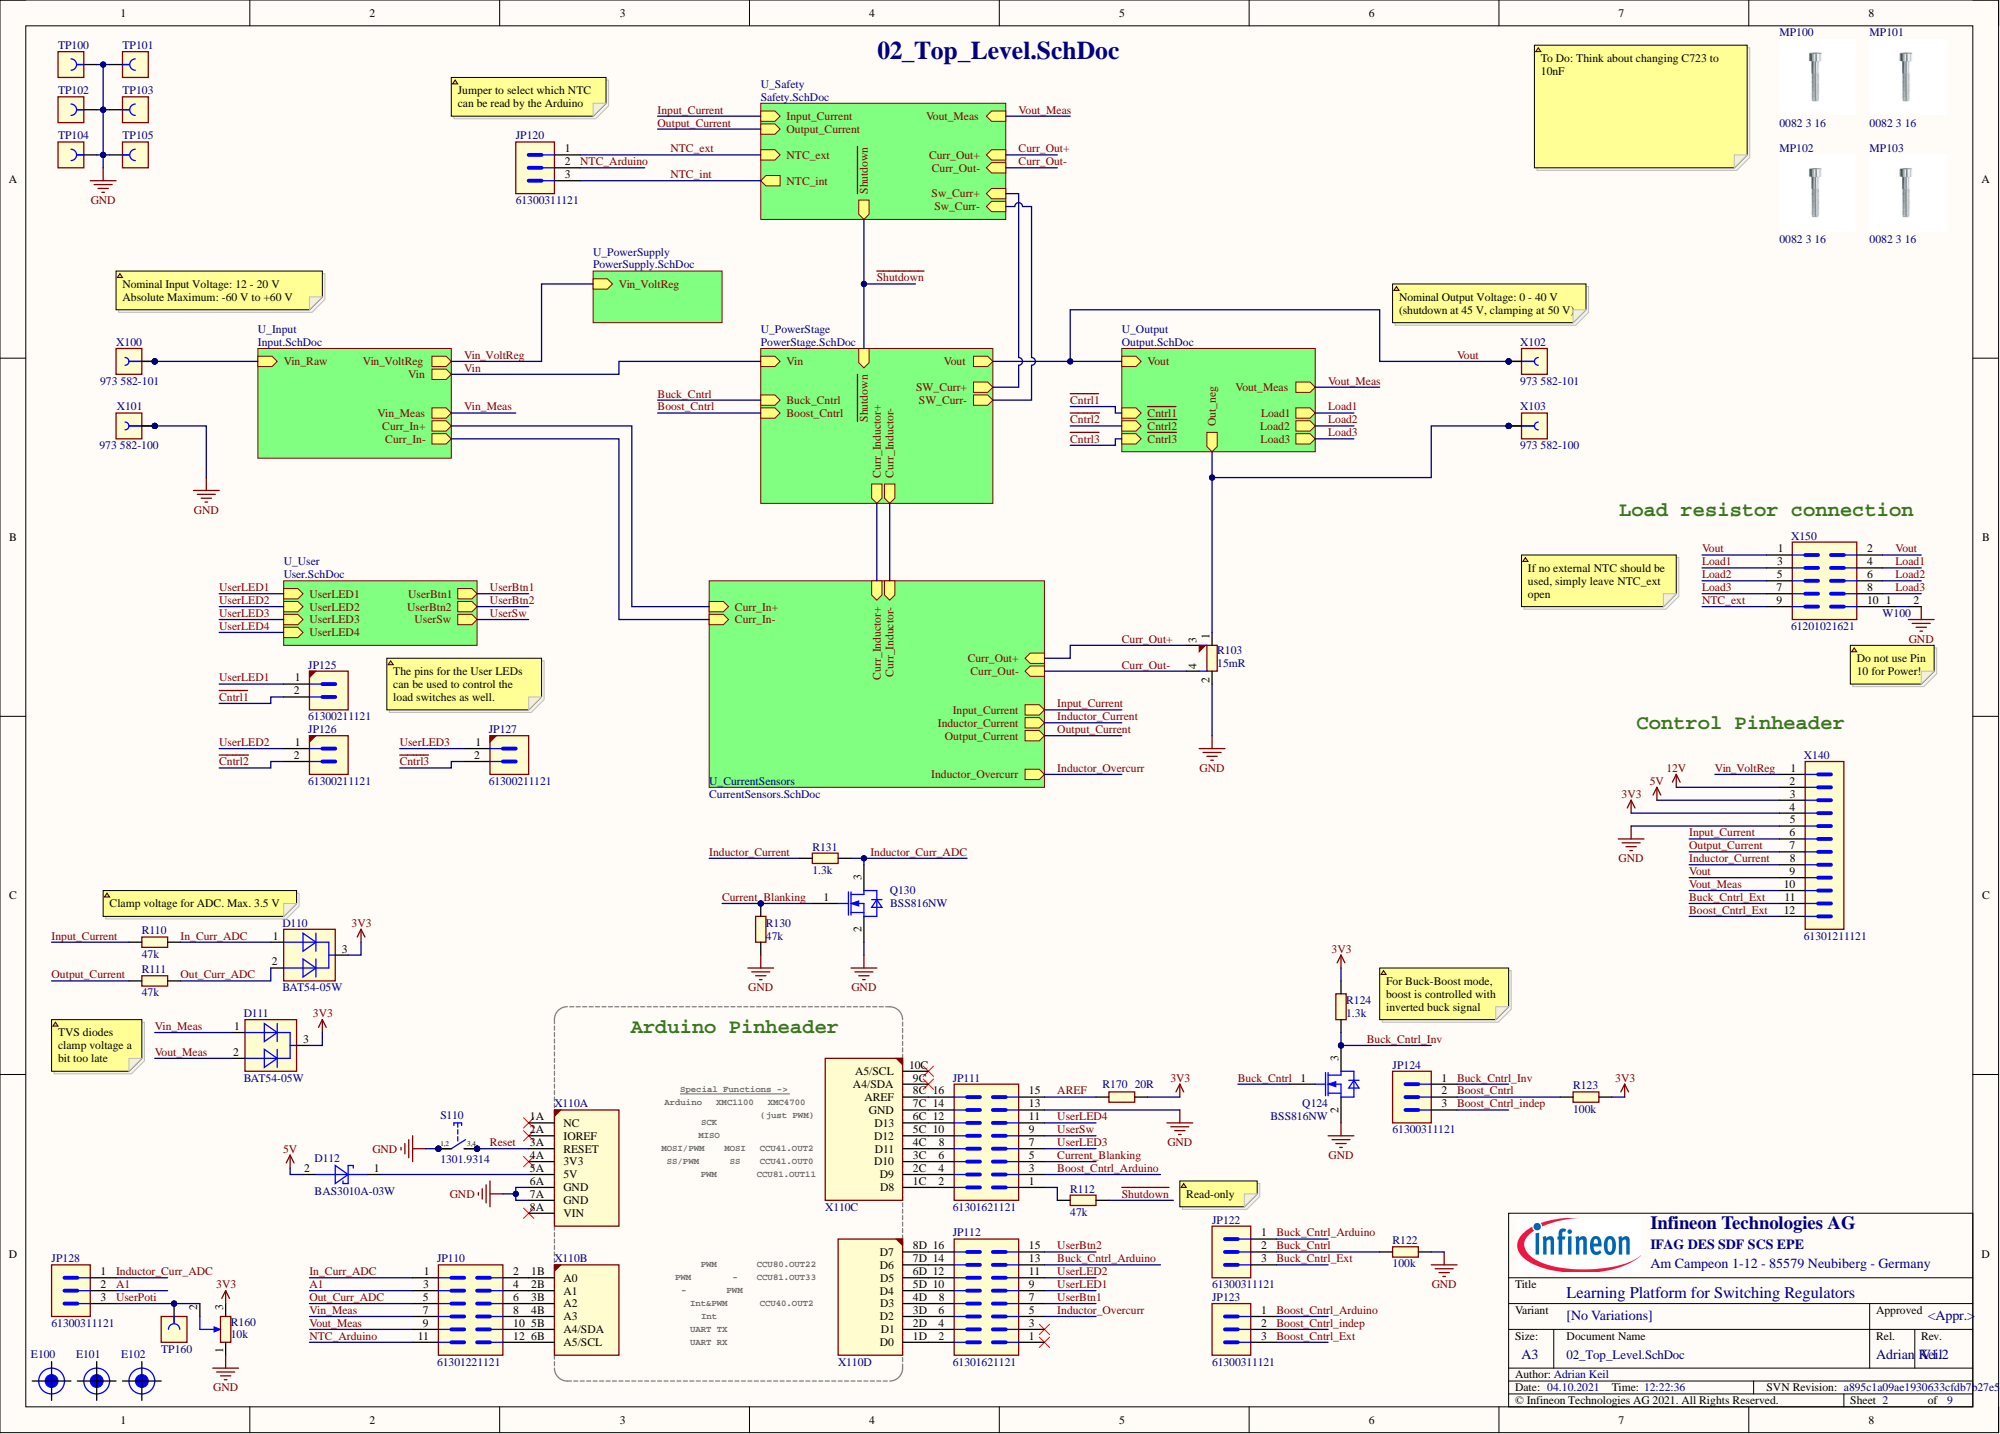
[picture p61: page 2]

To Do: Think about changing C723 to

Jumper to select which NTC
can be read by the Arduino

(shutdown at 45 V, clamping at 50 V)

If no external NTC should be
used, simply leave NTC_ext
open

The pins for the User LEDs
can be used to control the
load switches as well.

Do not use Pin
10 for Power!

Clamp voltage for ADC. Max. 3.5 V

For Buck-Boost mode,
boost is controlled with
inverted buck signal

Infineon Technologies AG
IFAG DES SDF SCS EPE
Am Campeon 1-12 - 85579 Neubiberg - Germany

Learning Platform for Switching Regulators

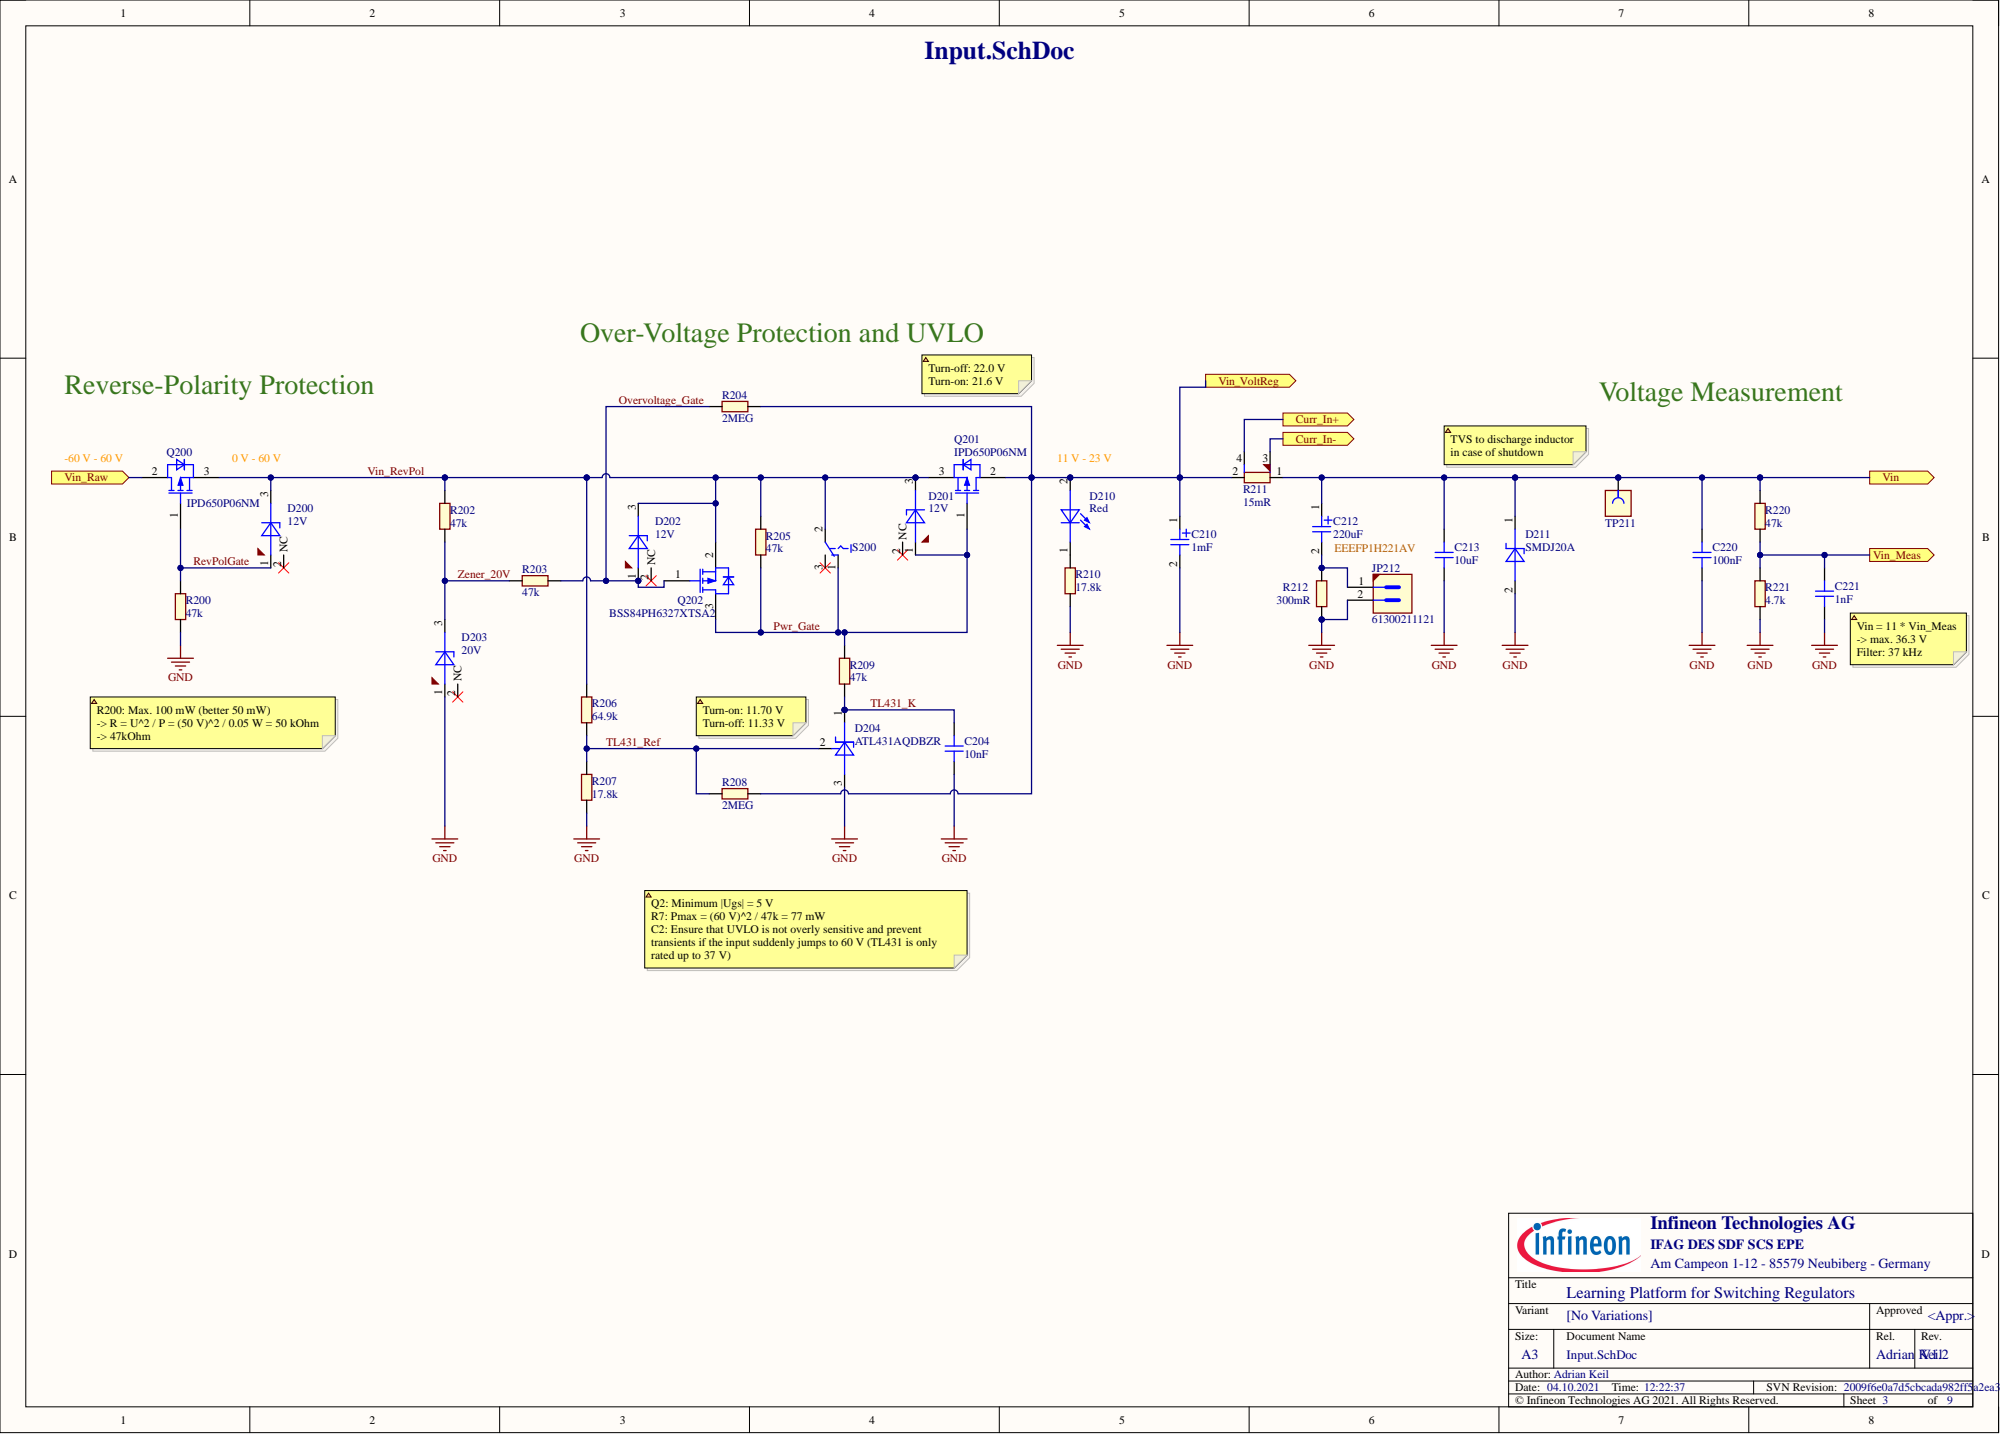
[picture p62: page 3]

Over-Voltage Protection and UVLO

Turn-off: 22.0 V Turn-on: 21.6 V
D204 ATL431AQDBZR3

TVS to discharge inductor
in case of shutdown

Turn-on: 11.70 V Turn-off: 11.33 V

Q2: Minimum |Ugs| = 5 V
R7: Pmax = (60 V)^2 / 47k = 77 mW
C2: Ensure that UVLO is not overly sensitive and prevent
transients if the input suddenly jumps to 60 V (TL431 is only
rated up to 37 V)

Infineon
IFAG DES SDF SCS EPE
Am Campeon 1-12 - 85579 Neubiberg -

Learning Platform for Switching Regulators

[No Variations] | Approved <Appr . >

Size: A | Input.Sch D o c | Rev . V1.

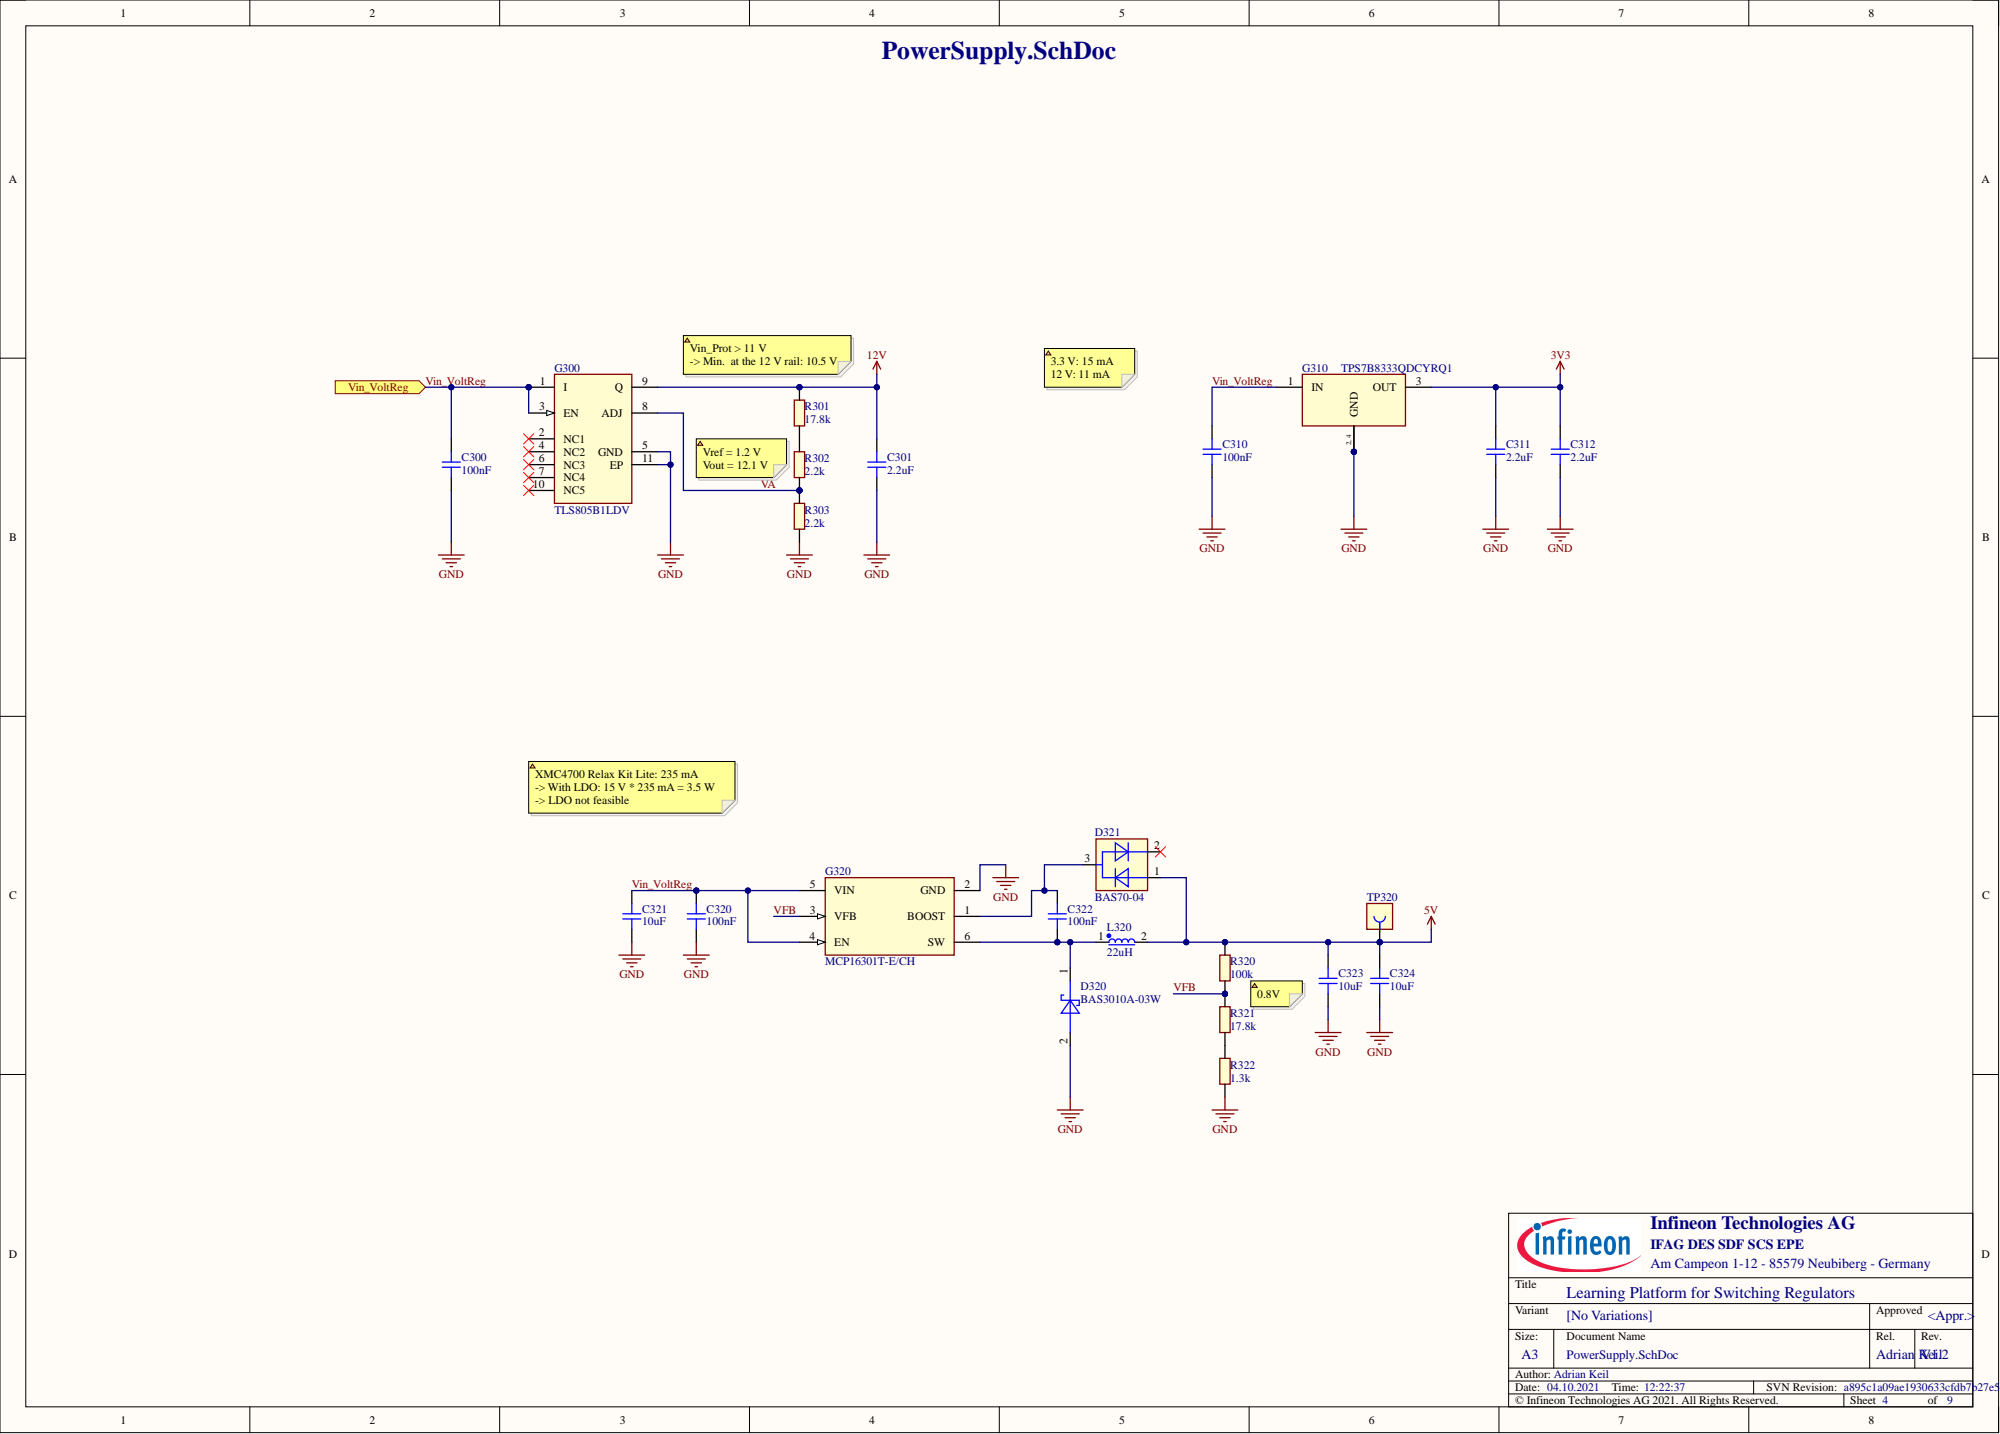
[picture p63: page 4]

Vin_Prot > 11 V
-> Min. at the 12 V rail: 10.5 V

XMC4700 Relax Kit Lite: 235 mA
-> With LDO: 15 V * 235 mA = 3.5 W
-> LDO not feasible

Infineon Technologies AG
IFAG DES SDF SCS EPE
Am Campeon 1-12 - 85579 Neubiberg - Germany

Learning Platform for Switching Regulators

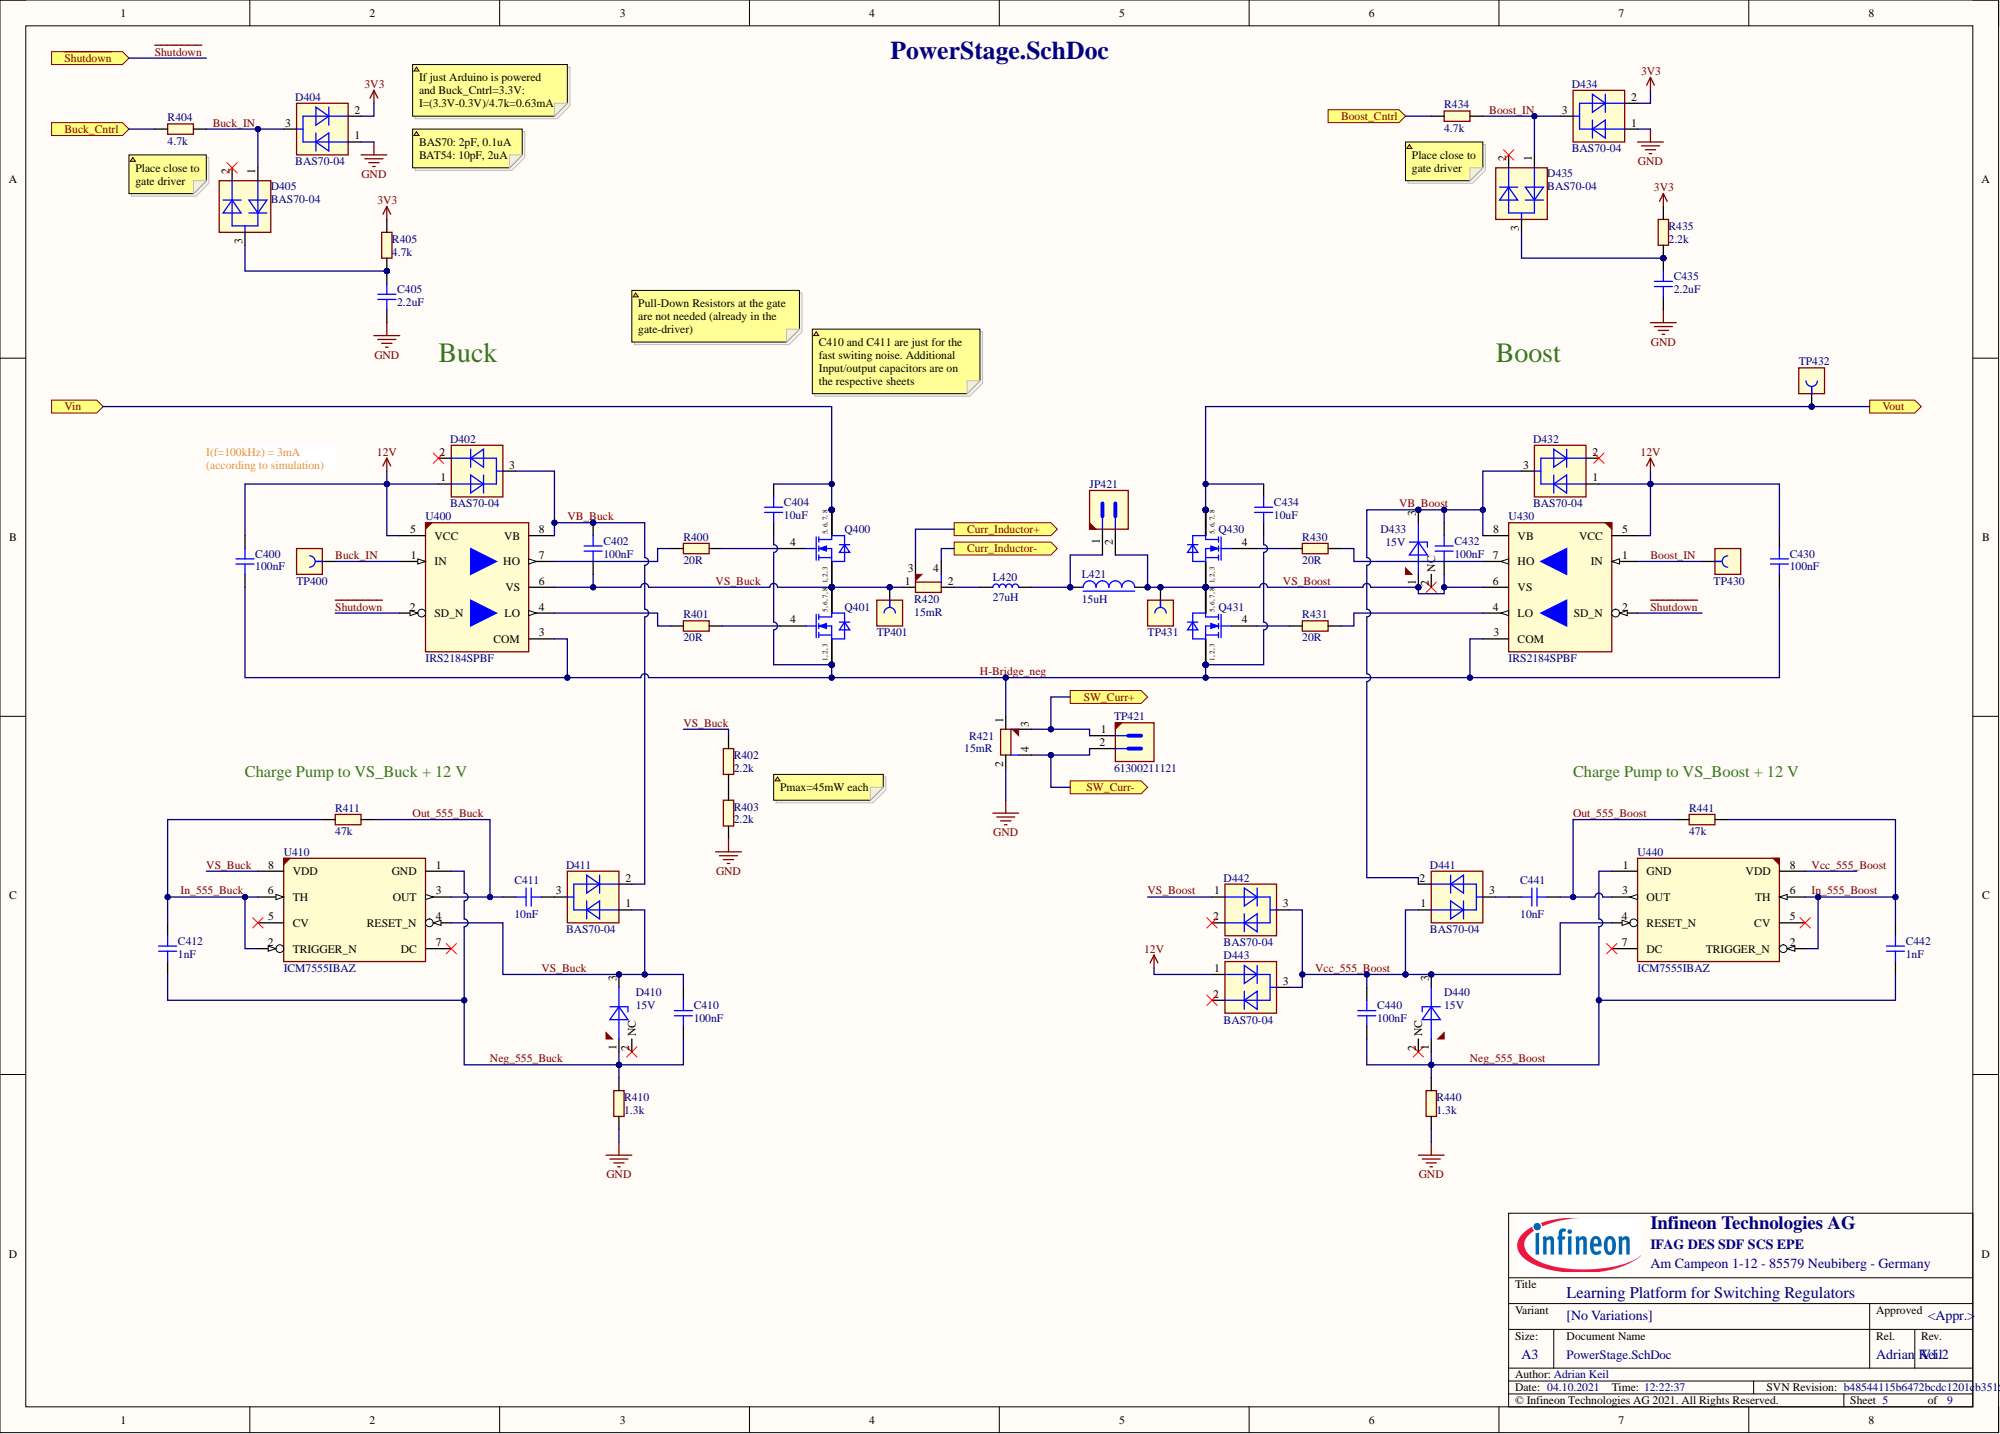
[picture p64: page 5]

If just Arduino is powered
and Buck_Cntrl=3.3V:

Pull-Down Resistors at the gate
are not needed (already in the
gate-driver)

C410 and C411 are just for the
fast switing noise. Additional
Input/output capacitors are on
the respective sheets

U400 | VB_Buck | C404

COM 3

Infineon Technologies AG
IFAG DES SDF SCS EPE
Am Campeon 1-12 - 85579 Neubiberg - Germany

Learning Platform for Switching Regulators

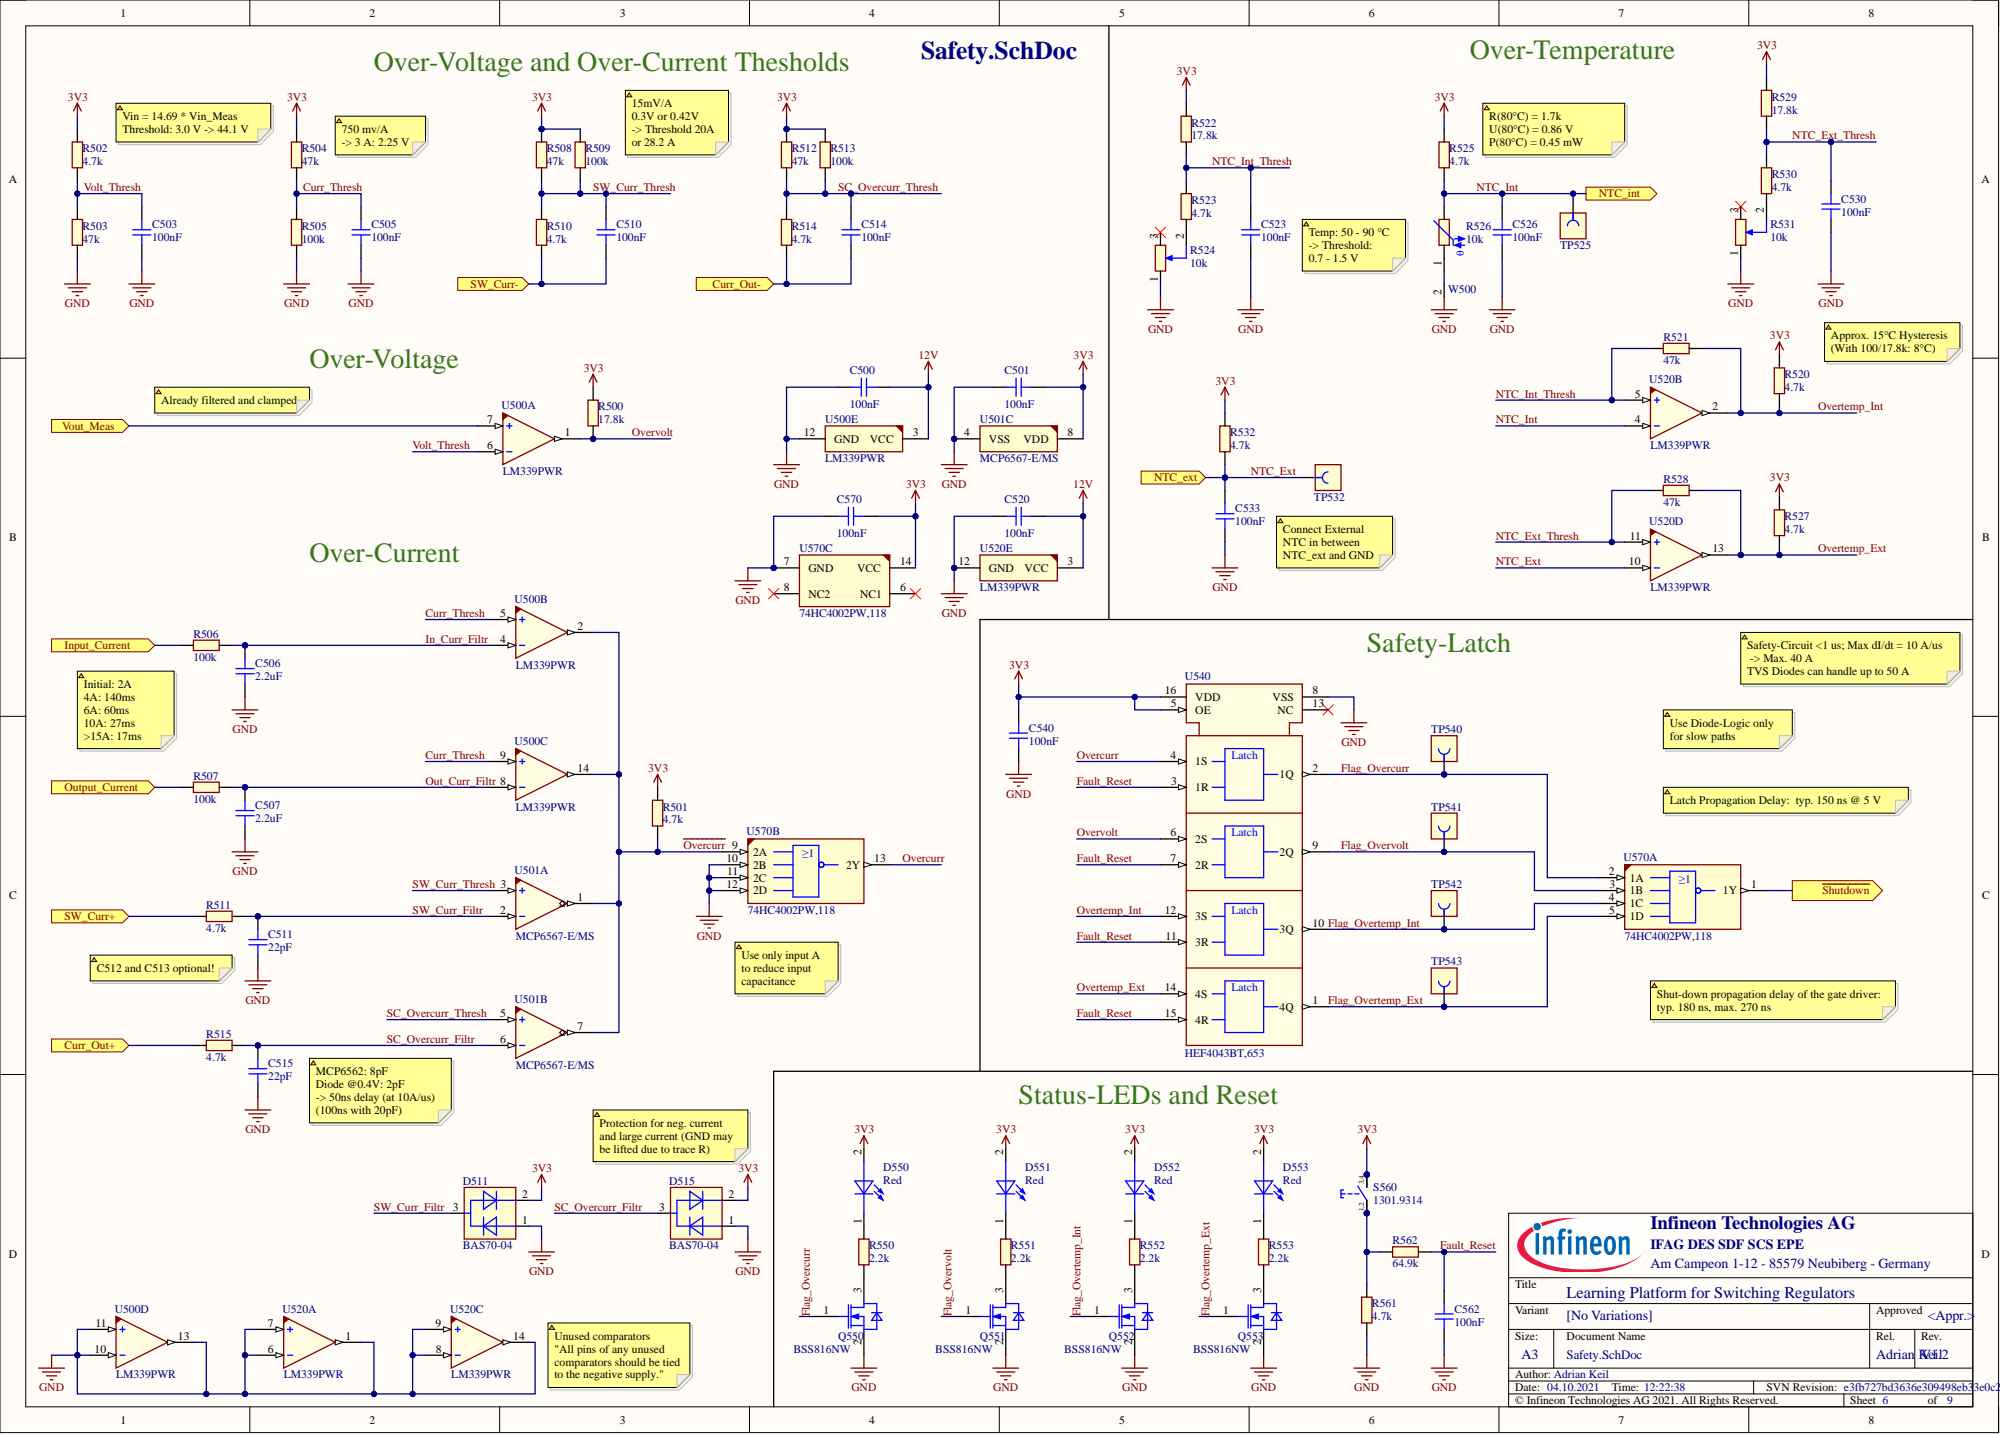
[picture p65: page 6]

Over-Voltage and Over-Current Thesholds

Already filtered and clamped

Safety-Circuit <1 us; Max dI/dt = 10 A/us
-> Max. 40 A
TVS Diodes can handle up to 50 A

Use Diode-Logic only
for slow paths

Latch Propagation Delay: typ. 150 ns @ 5 V

2B 10
2C 11

Flag_Overtemp_Int

Shut-down propagation delay of the gate driver:
typ. 180 ns, max. 270 ns

Status-LEDs and Reset

Protection for neg. current
and large current (GND may
be lifted due to trace R)

Infineon Technologies AG
IFAG DES SDF SCS EPE
Am Campeon 1-12 - 85579 Neubiberg - Germany

Learning Platform for Switching Regulators

Unused comparators
"All pins of any unused
comparators should be tied
to the negative supply."

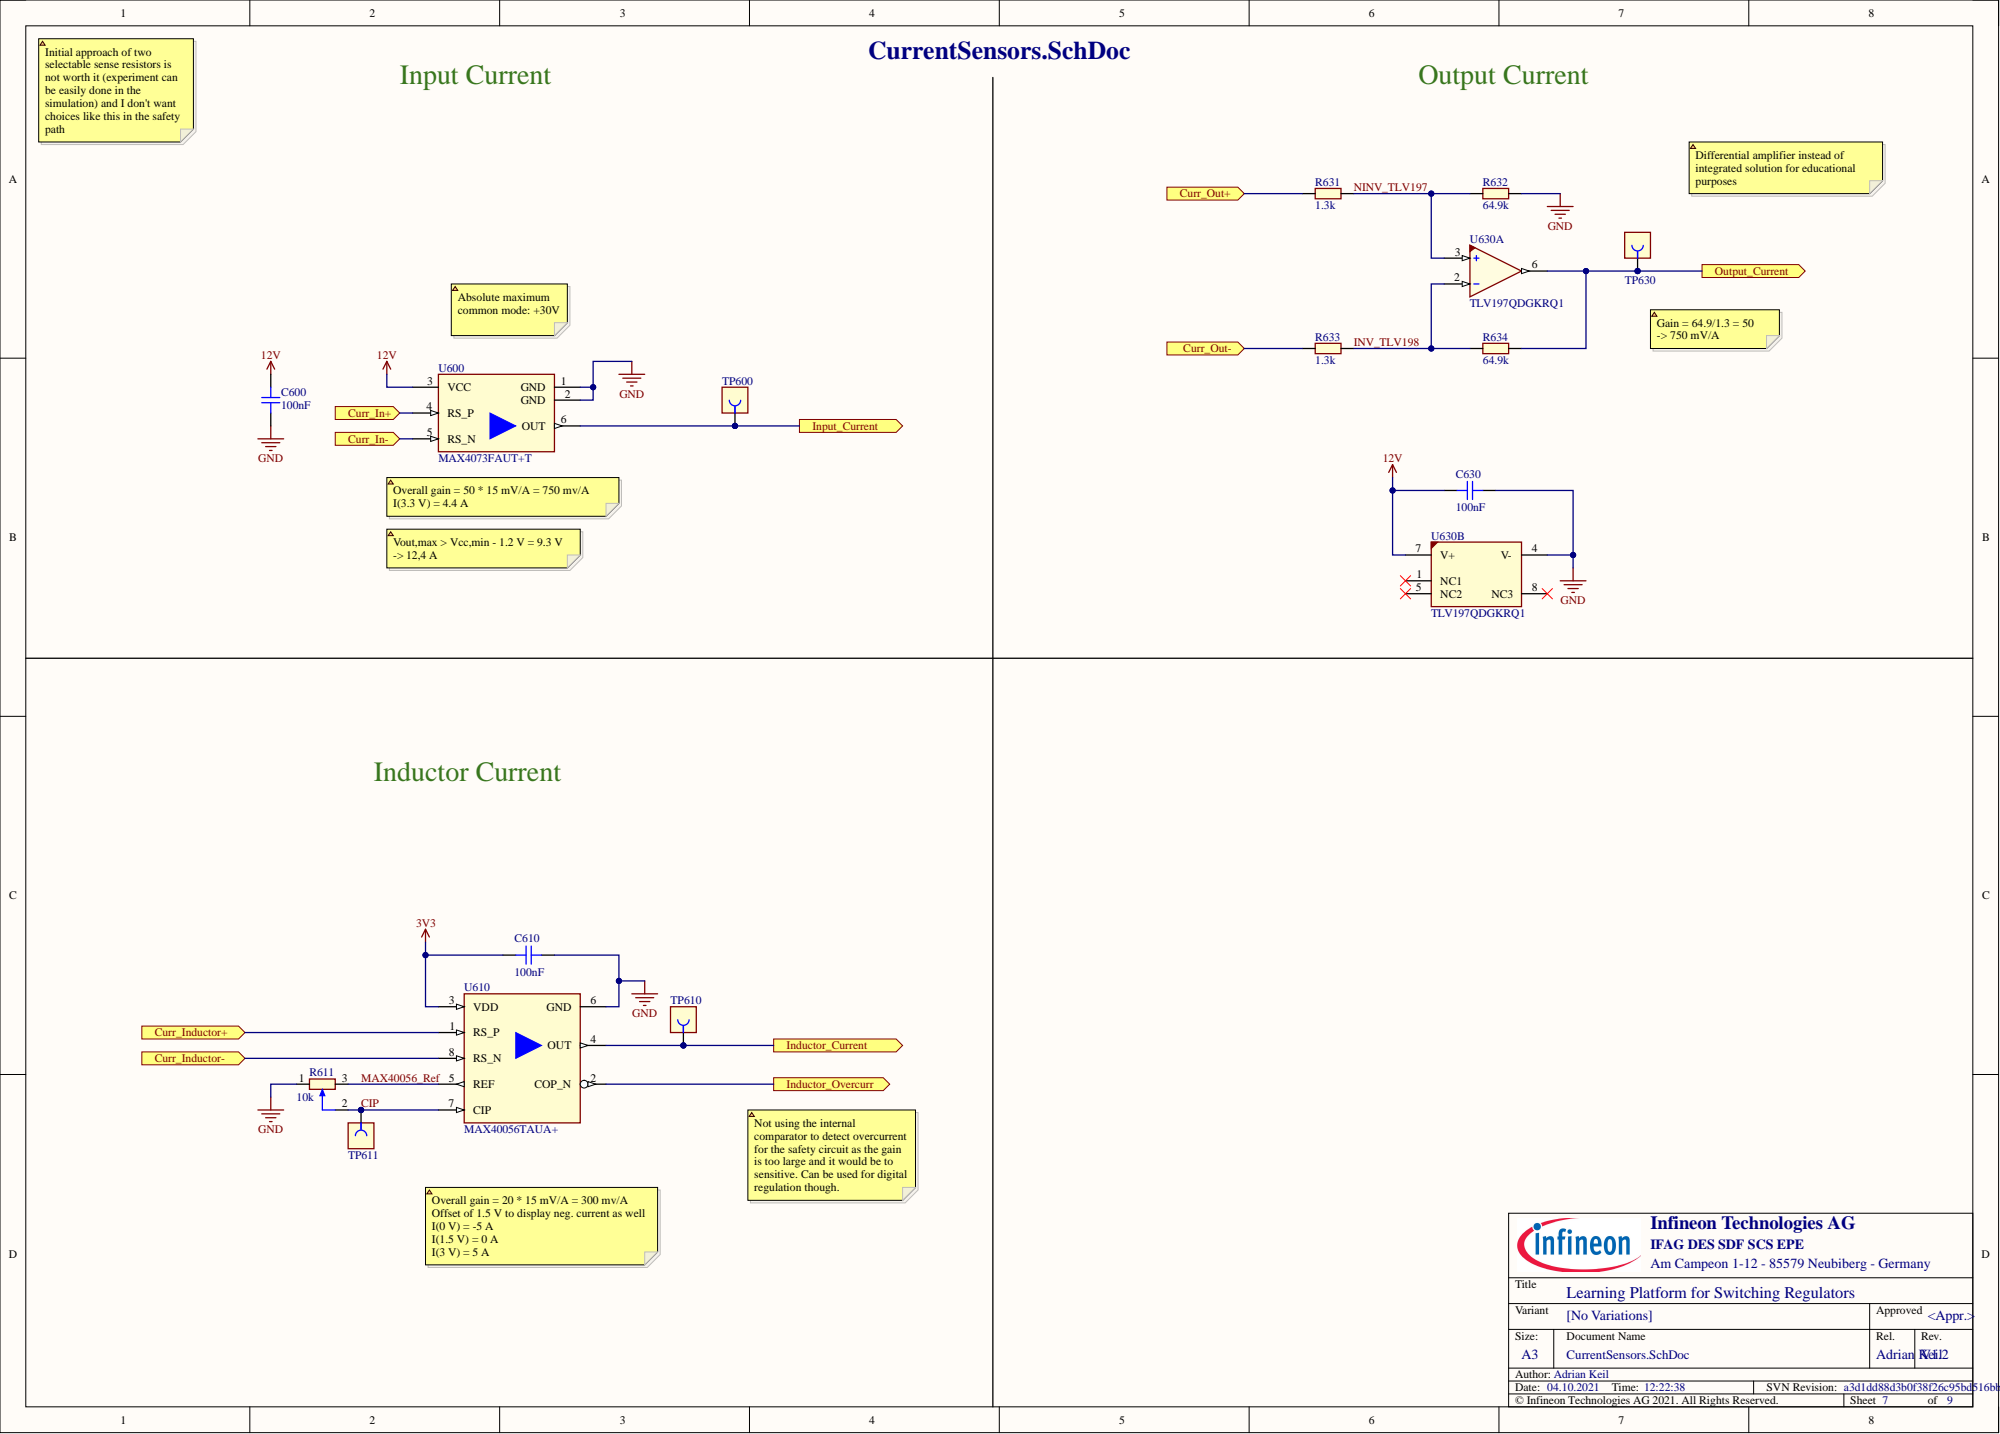
[picture p66: page 7]

Initial approach of two
selectable sense resistors is
not worth it (experiment can
be easily done in the
simulation) and I don't want
choices like this in the safety
path

Differential amplifier instead of
integrated solution for educational
purposes

Overall gain = 50 * 15 mV/A = 750 mv/A

Vout,max > Vcc,min - 1.2 V = 9.3 V

Not using the internal
comparator to detect overcurrent
for the safety circuit as the gain
is too large and it would be to
sensitive. Can be used for digital
regulation though.

Overall gain = 20 * 15 mV/A = 300 mv/A
Offset of 1.5 V to display neg. current as well

Infineon Technologies AG
IFAG DES SDF SCS EPE
Am Campeon 1-12 - 85579 Neubiberg - Germany

Learning Platform for Switching Regulators

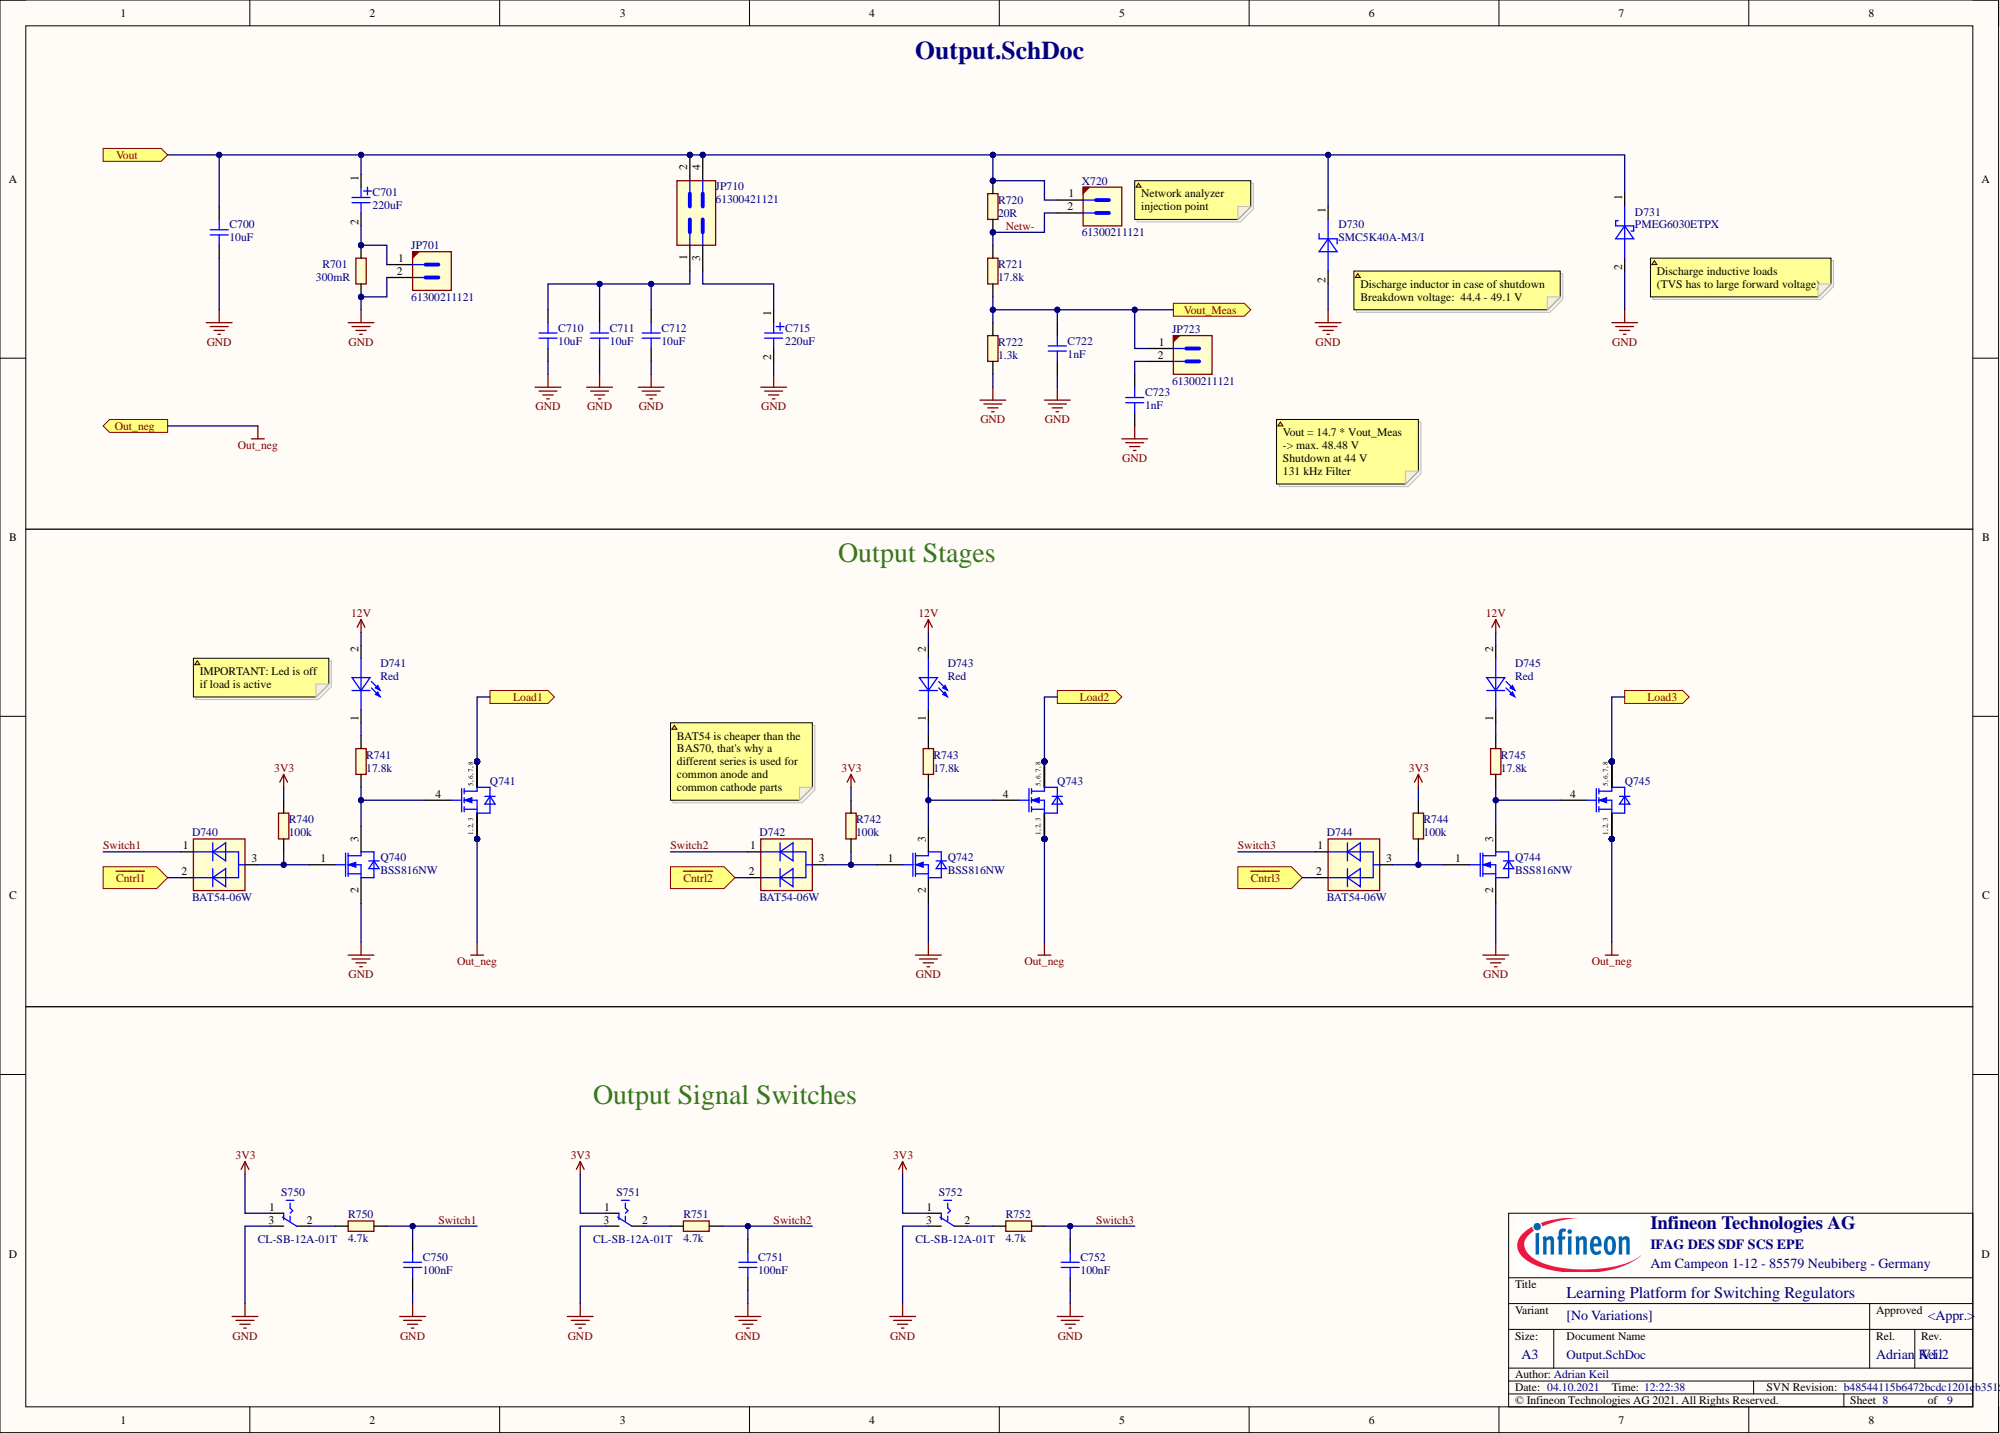
[picture p67: page 8]

IMPORTANT: Led is off
if load is active

BAT54 is cheaper than the
BAS70, that's why a
different series is used for
common anode and
common cathode parts

Infineon Technologies AG
IFAG DES SDF SCS EPE
Am Campeon 1-12 - 85579 Neubiberg - Germany

Learning Platform for Switching Regulators

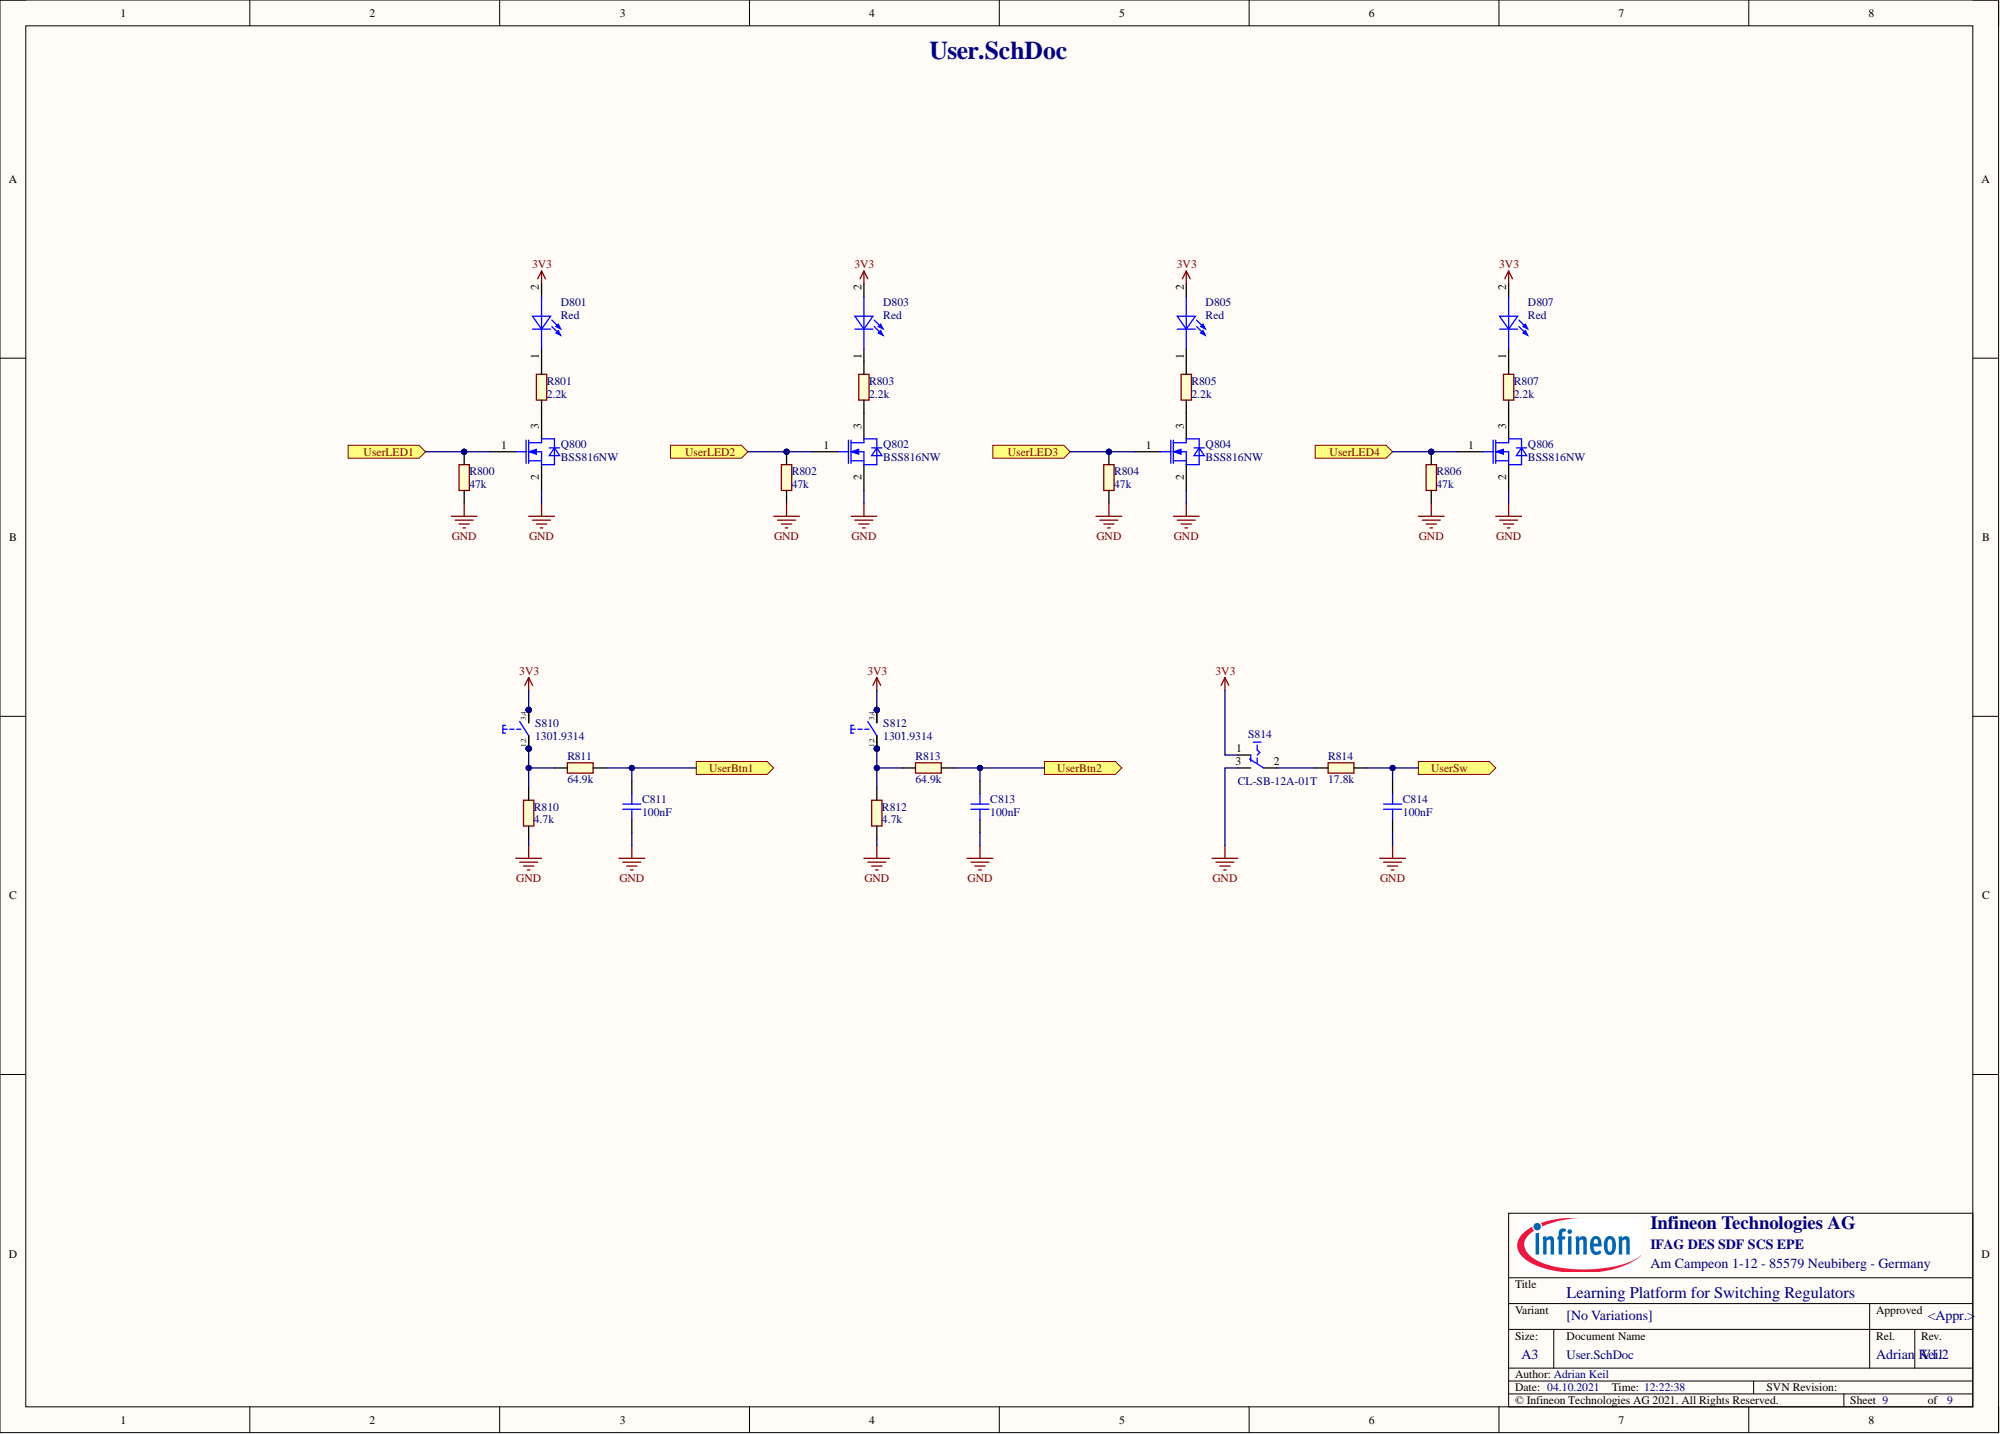
[picture p68: page 9]

Infineon Technologies AG
IFAG DES SDF SCS EPE
Am Campeon 1-12 - 85579 Neubiberg - Germany

Learning Platform for Switching Regulators
