Infineon/voltage-regulator-learning-platform/Version1.1/Project Outputs/PDF/PCB Prints.PDF

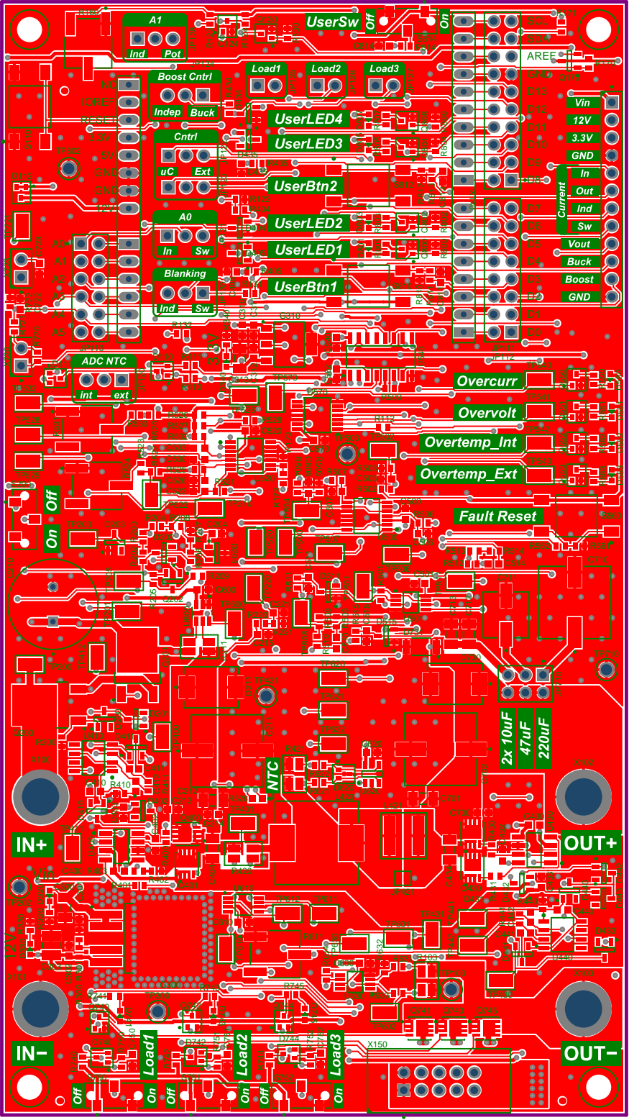
[picture p86: page 1]

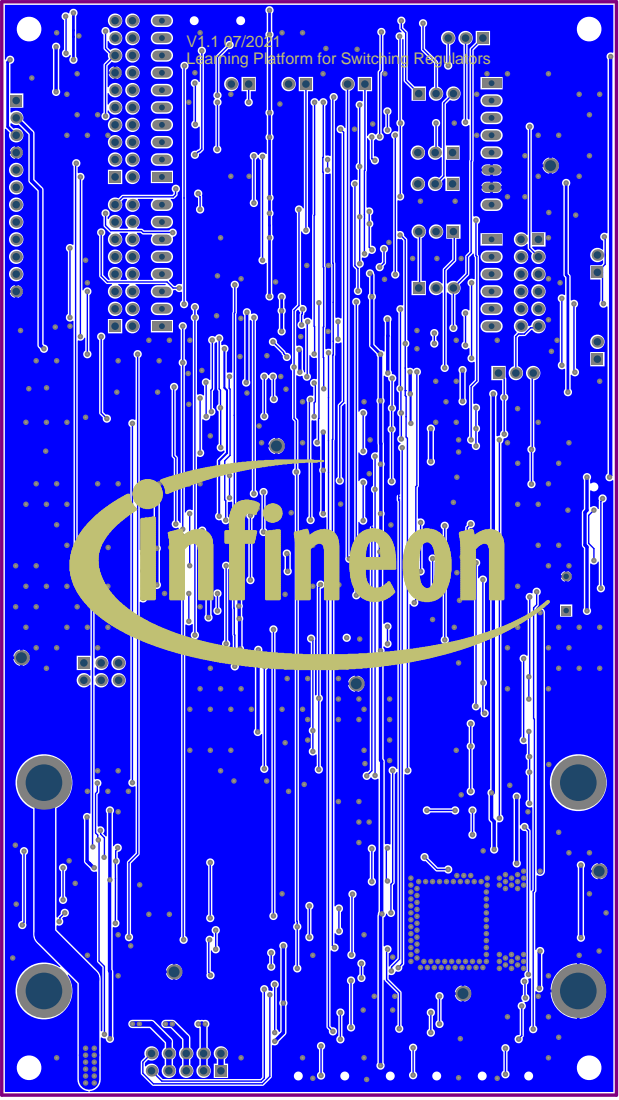
[picture p87: page 2]

Learning Platform for Switching Regulators
