Infineon/voltage-regulator-learning-platform/Version1.2/Project Outputs/PDF/PCB Prints.PDF

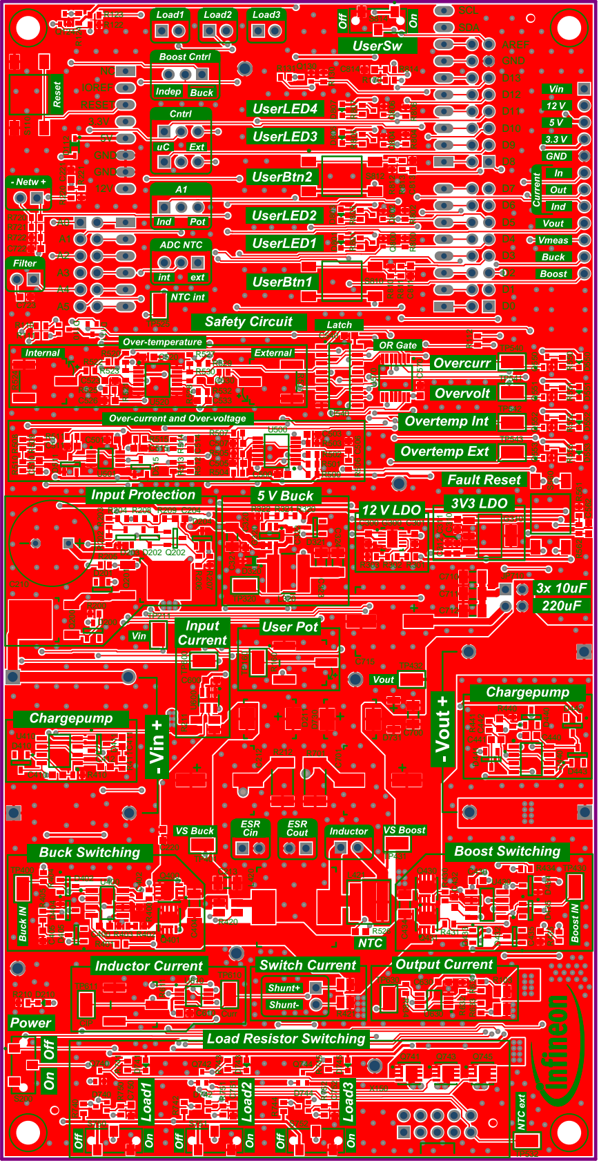
[picture p88: page 1]

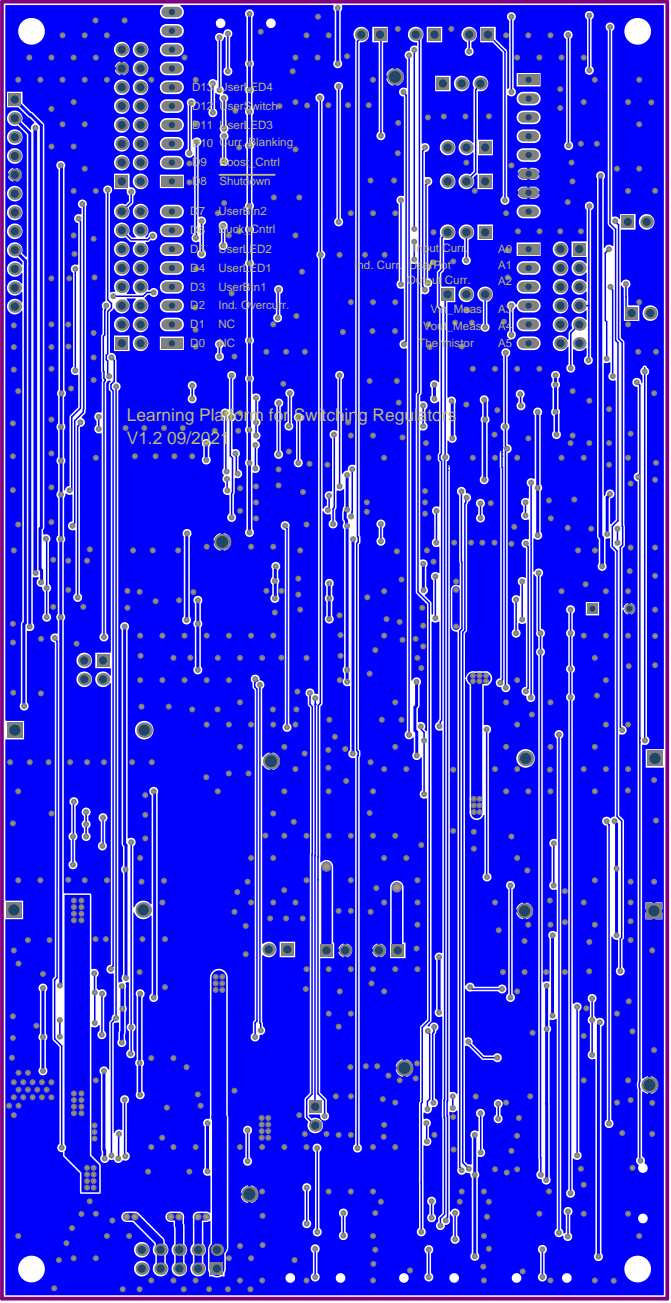
[picture p89: page 2]

Learning Platform for Switching Regulators
