Infineon/voltage-regulator-learning-platform/Version2.0/Vreg_Learning_Platform.pdf

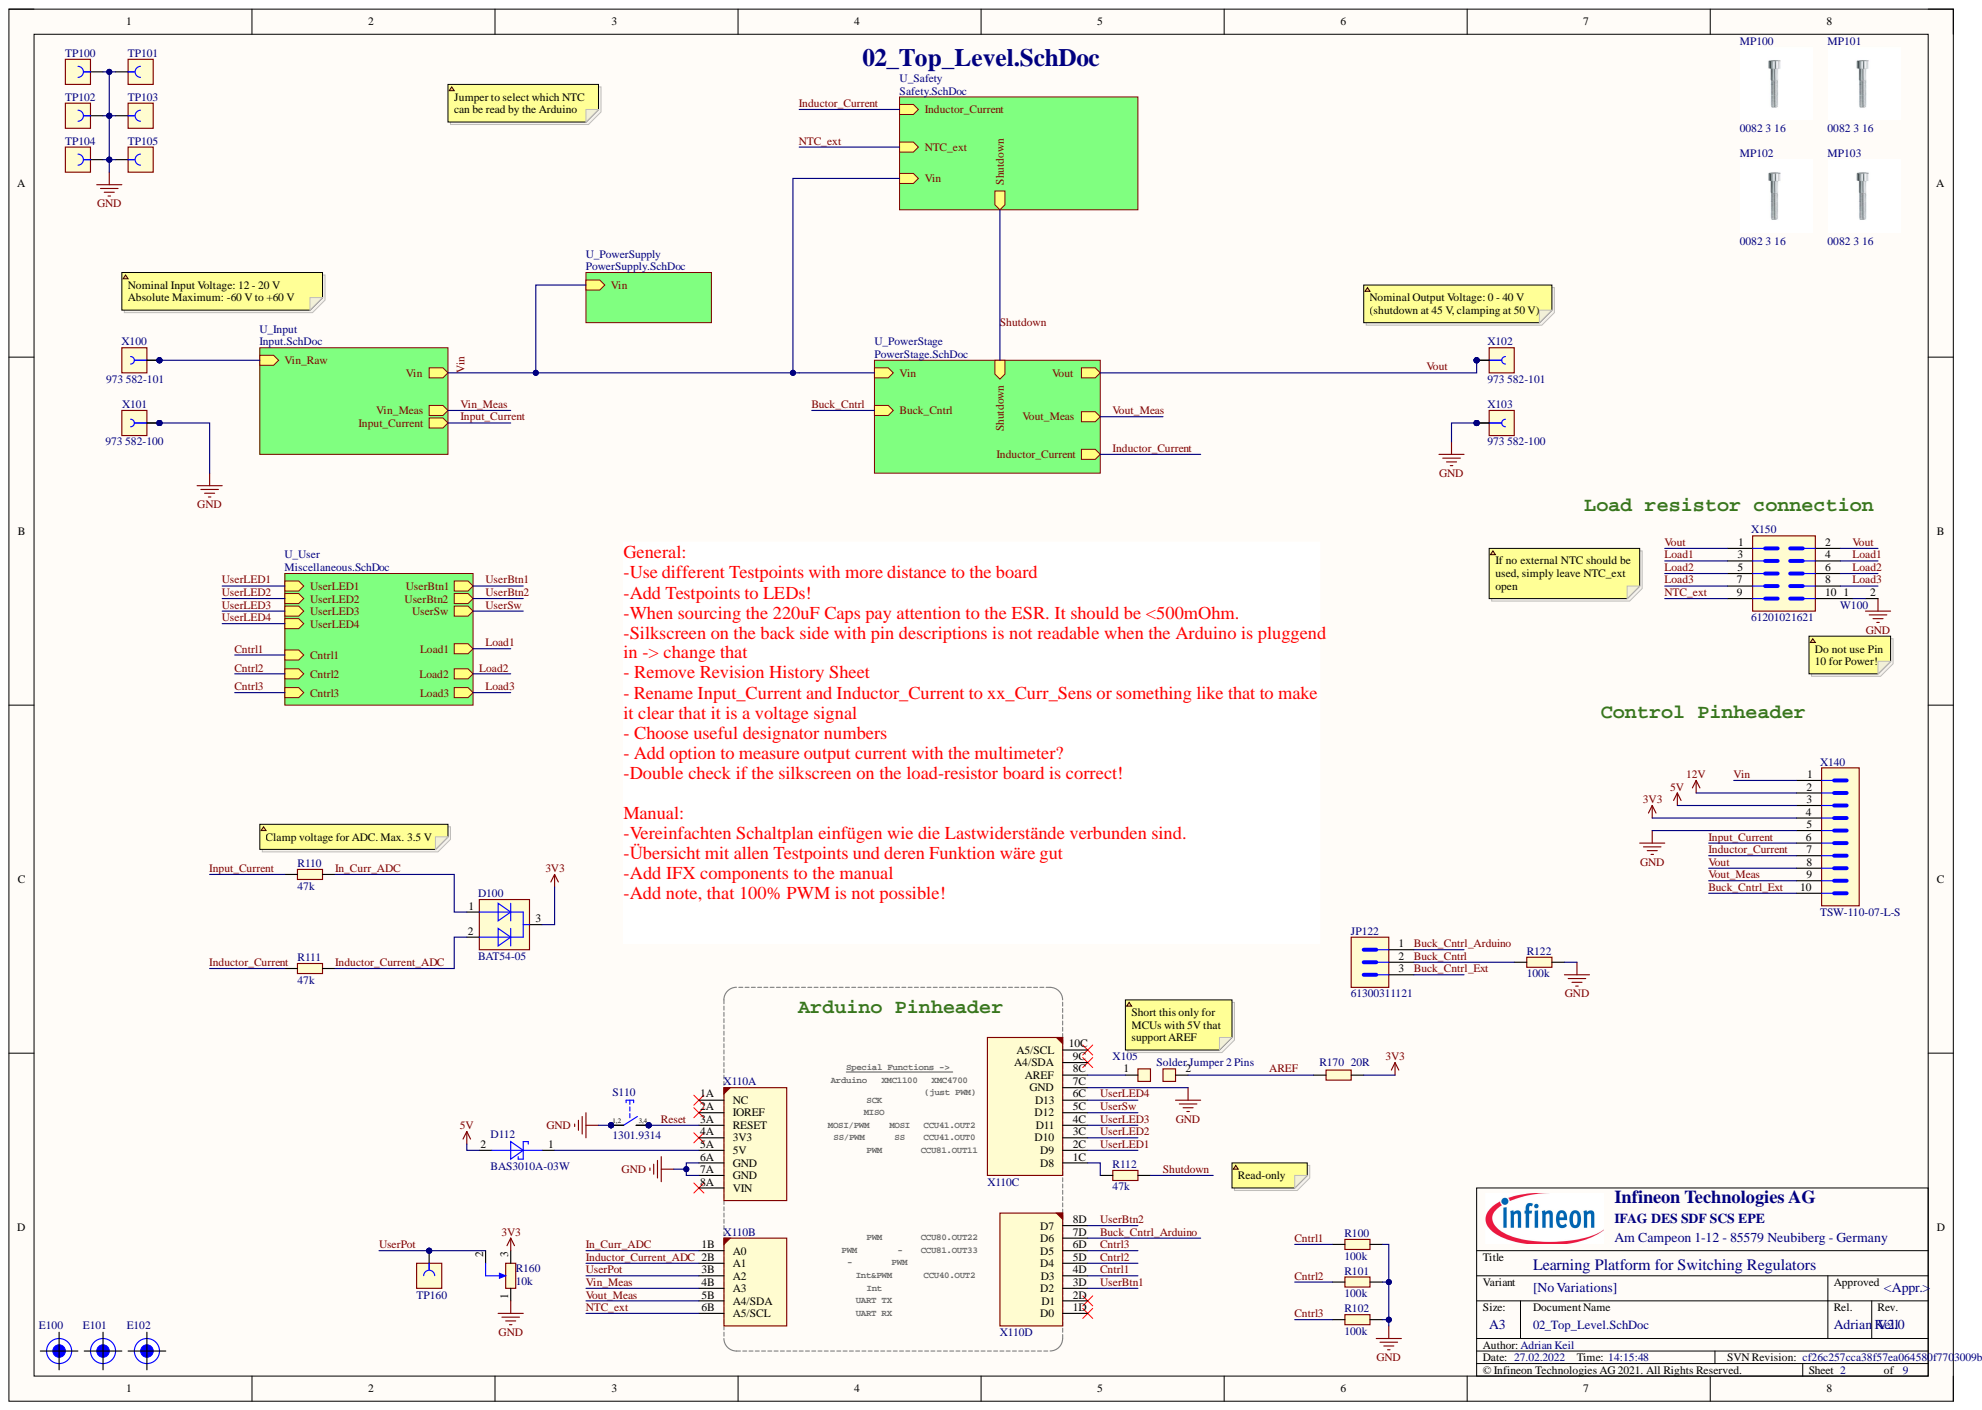
[picture p90: page 1]

Vin Jumper to select which NTC
can be read by the Arduino

(shutdown at 45 V, clamping at 50 V)

General:
-Use different Testpoints with more distance to the board
-Add Testpoints to LEDs!
-When sourcing the 220uF Caps pay attention to the ESR. It should be <500mOhm.
-Silkscreen on the back side with pin descriptions is not readable when the Arduino is pluggend
in -> change that
- Remove Revision History Sheet
- Rename Input_Current and Inductor_Current to xx_Curr_Sens or something like that to make
it clear that it is a voltage signal
- Choose useful designator numbers
- Add option to measure output current with the multimeter?
-Double check if the silkscreen on the load-resistor board is correct!

If no external NTC should be
used, simply leave NTC_ext
open

Do not use Pin
10 for Power!

Manual:
-Vereinfachten Schaltplan einfügen wie die Lastwiderstände verbunden sind.
-Übersicht mit allen Testpoints und deren Funktion wäre gut
-Add IFX components to the manual
-Add note, that 100% PWM is not possible!

Clamp voltage for ADC. Max. 3.5 V

Short this only for
MCUs with 5V that
support AREF

IFAG DES SDF SCS EPE
Am Campeon 1-12 - 85579 Neubiberg - Germany

Learning Platform for Switching Regulators

Date: 27.02.2022 Time: 14:15:48
© Infineon Technologies AG 2021. All Rights Reserved. | Sheet of

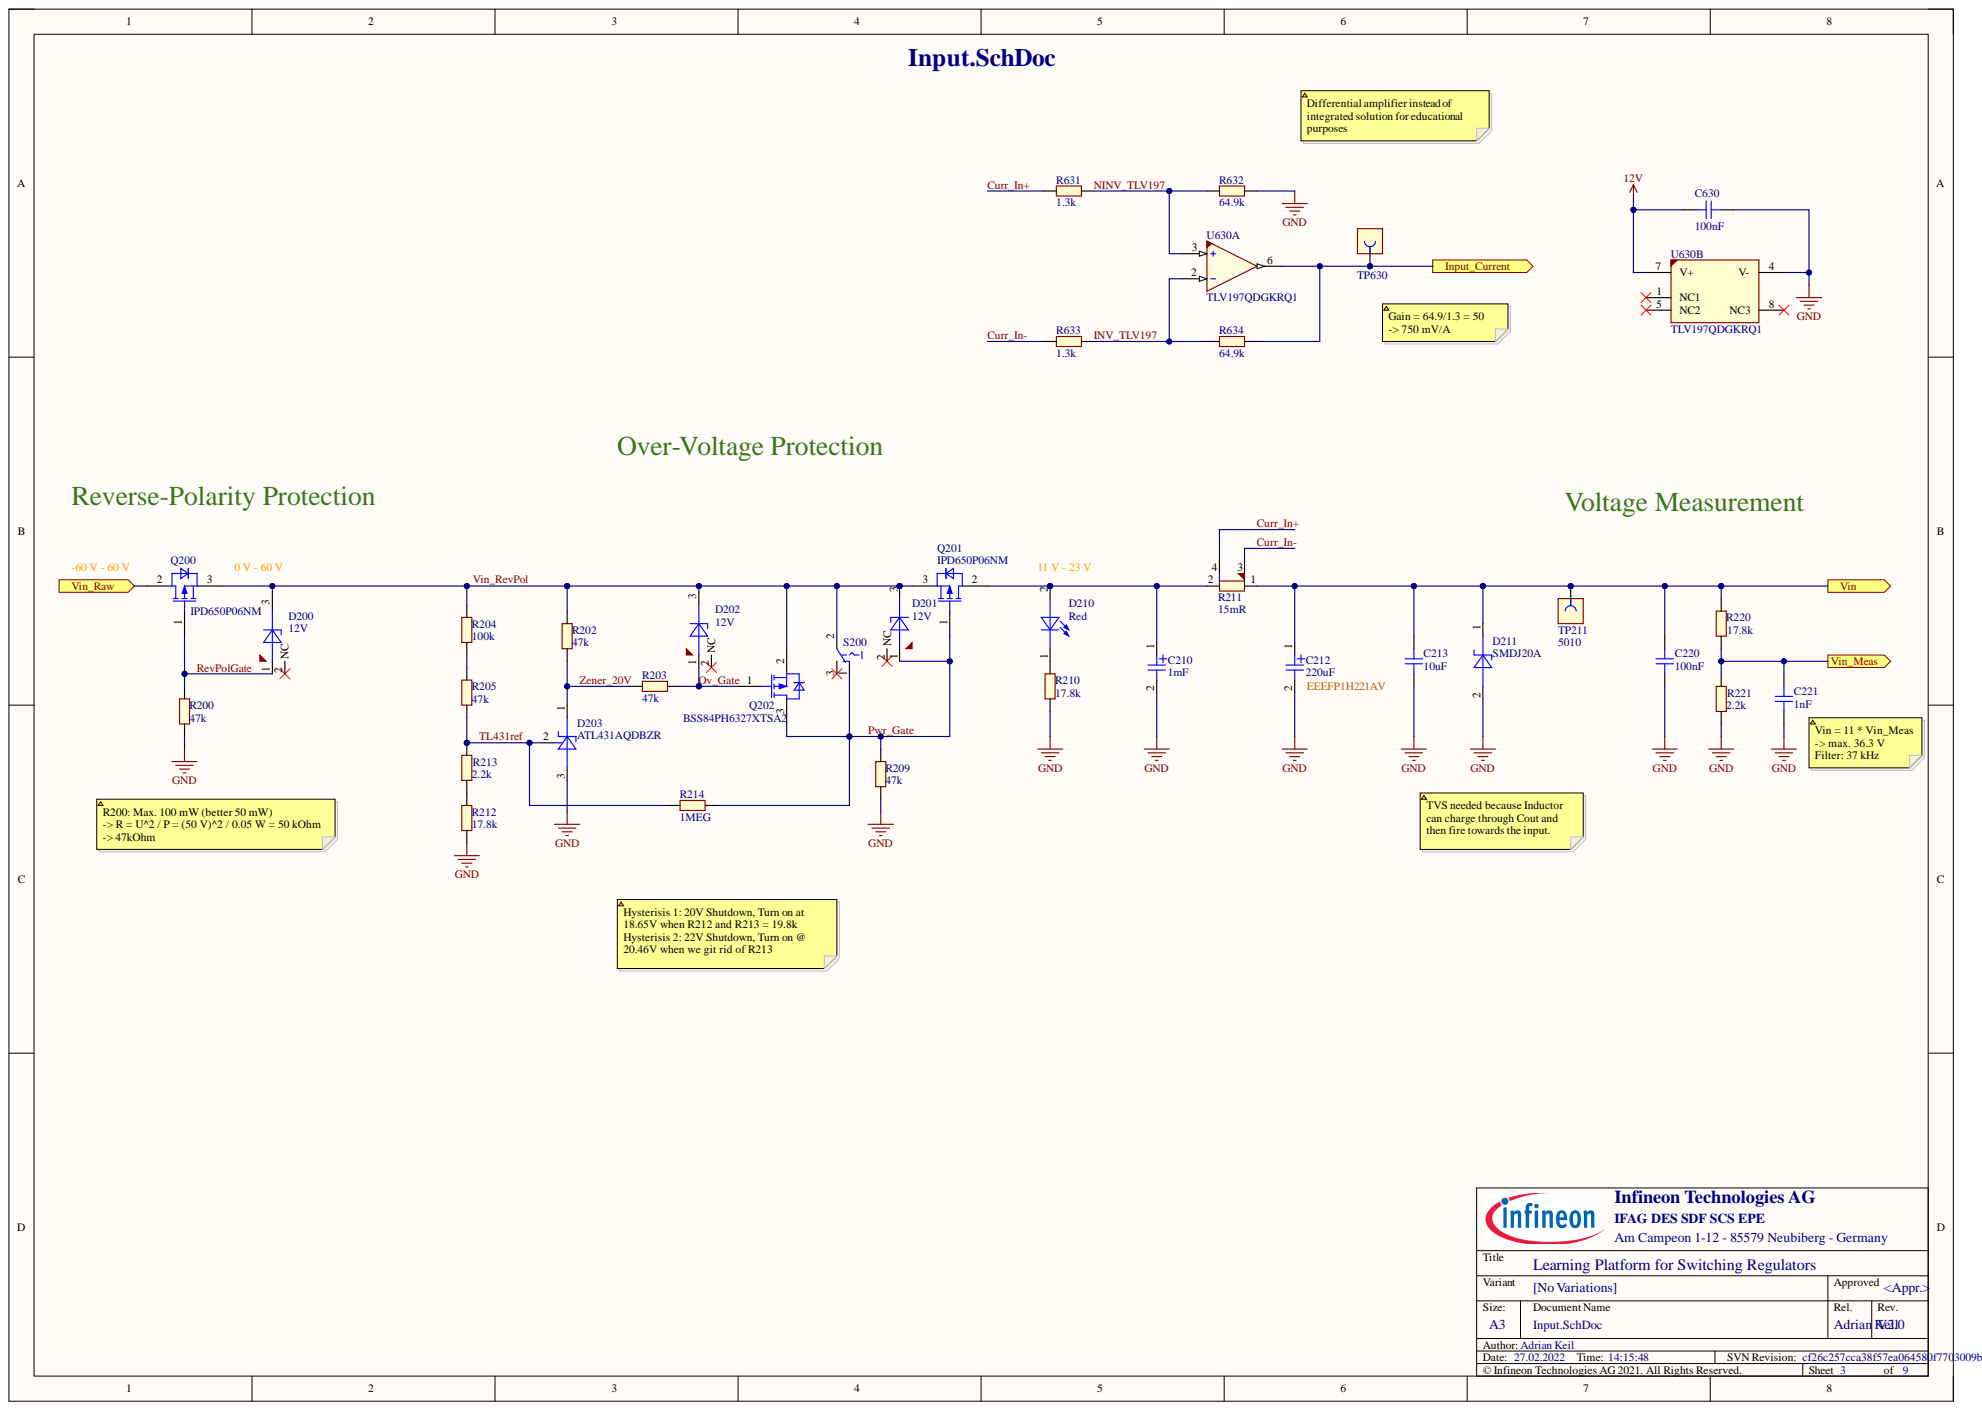
[picture p91: page 2]

Differential amplifierinstead of
integrated solution for educational
purposes

TVS needed because Inductor
can charge through Cout and
then fire towards the input.

Hysterisis 1: 20V Shutdown, Turn on at
18.65V when R212 and R213 = 19.8k
Hysterisis 2: 22V Shutdown, Turn on @
20.46V when we git rid of R213

IFAG DES SDF SCS EPE
Am Campeon 1-12 - 85579 Neubiberg - Germany

Learning Platform for Switching Regulators

Variant [No Variations] | Approved <Appr.>

Input.SchDoc

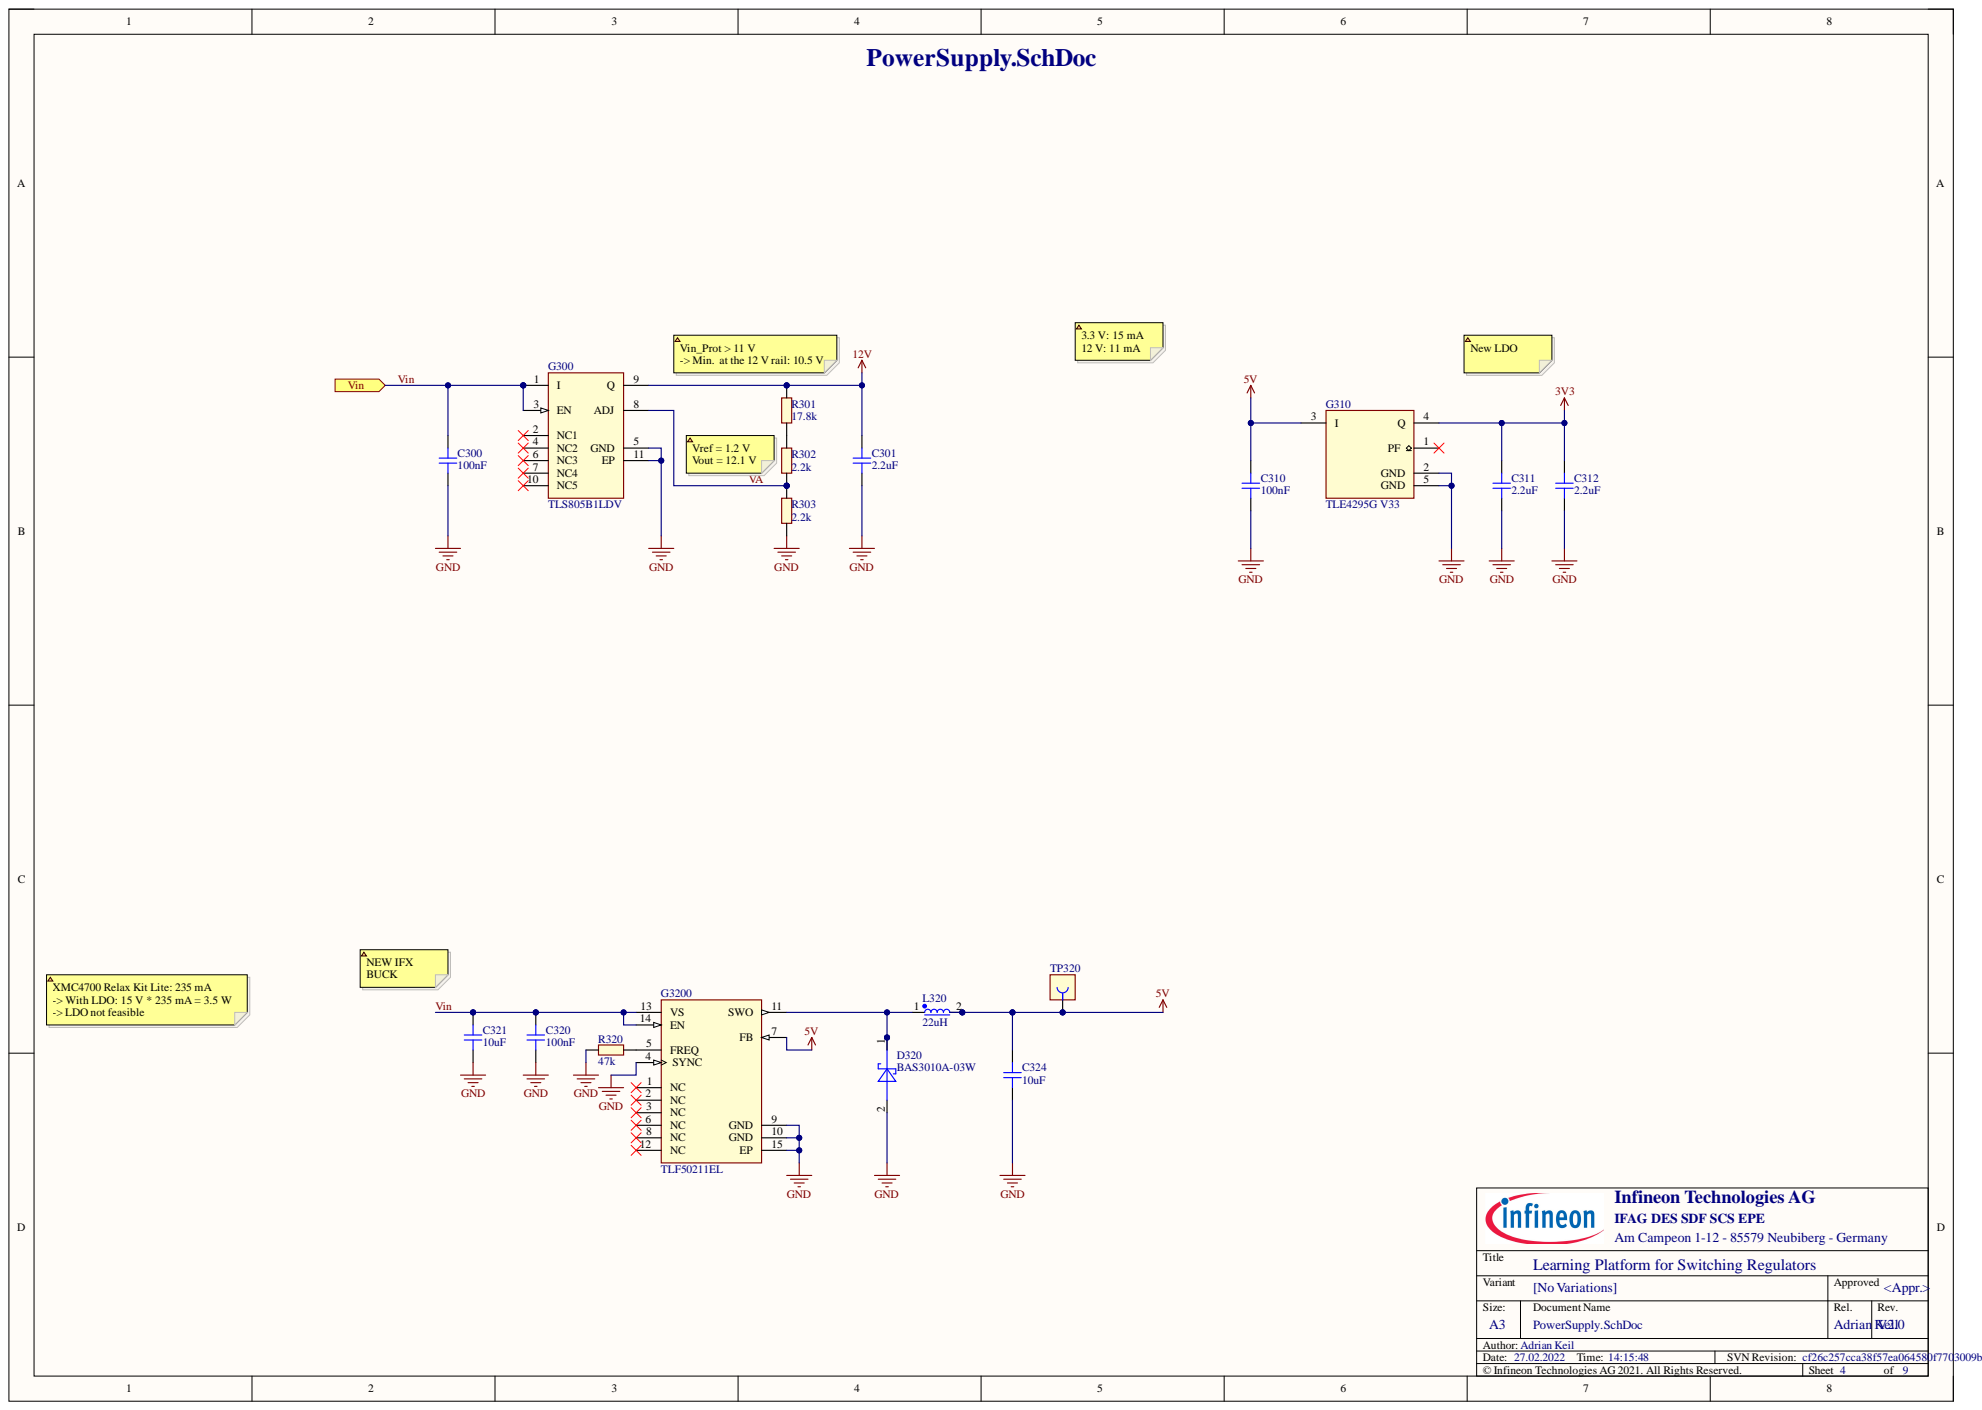
[picture p92: page 3]

-> Min. at the 12 V rail: 10.5 V

XMC4700 Relax Kit Lite: 235 mA
-> With LDO: 15 V * 235 mA = 3.5 W
-> LDO not feasible

IFAG DES SDF SCS EPE
Am Campeon 1-12 - 85579 Neubiberg - Germany

Learning Platform for Switching Regulators

Variant [No Variations] | Approved <Appr.>

PowerSupply.SchDoc

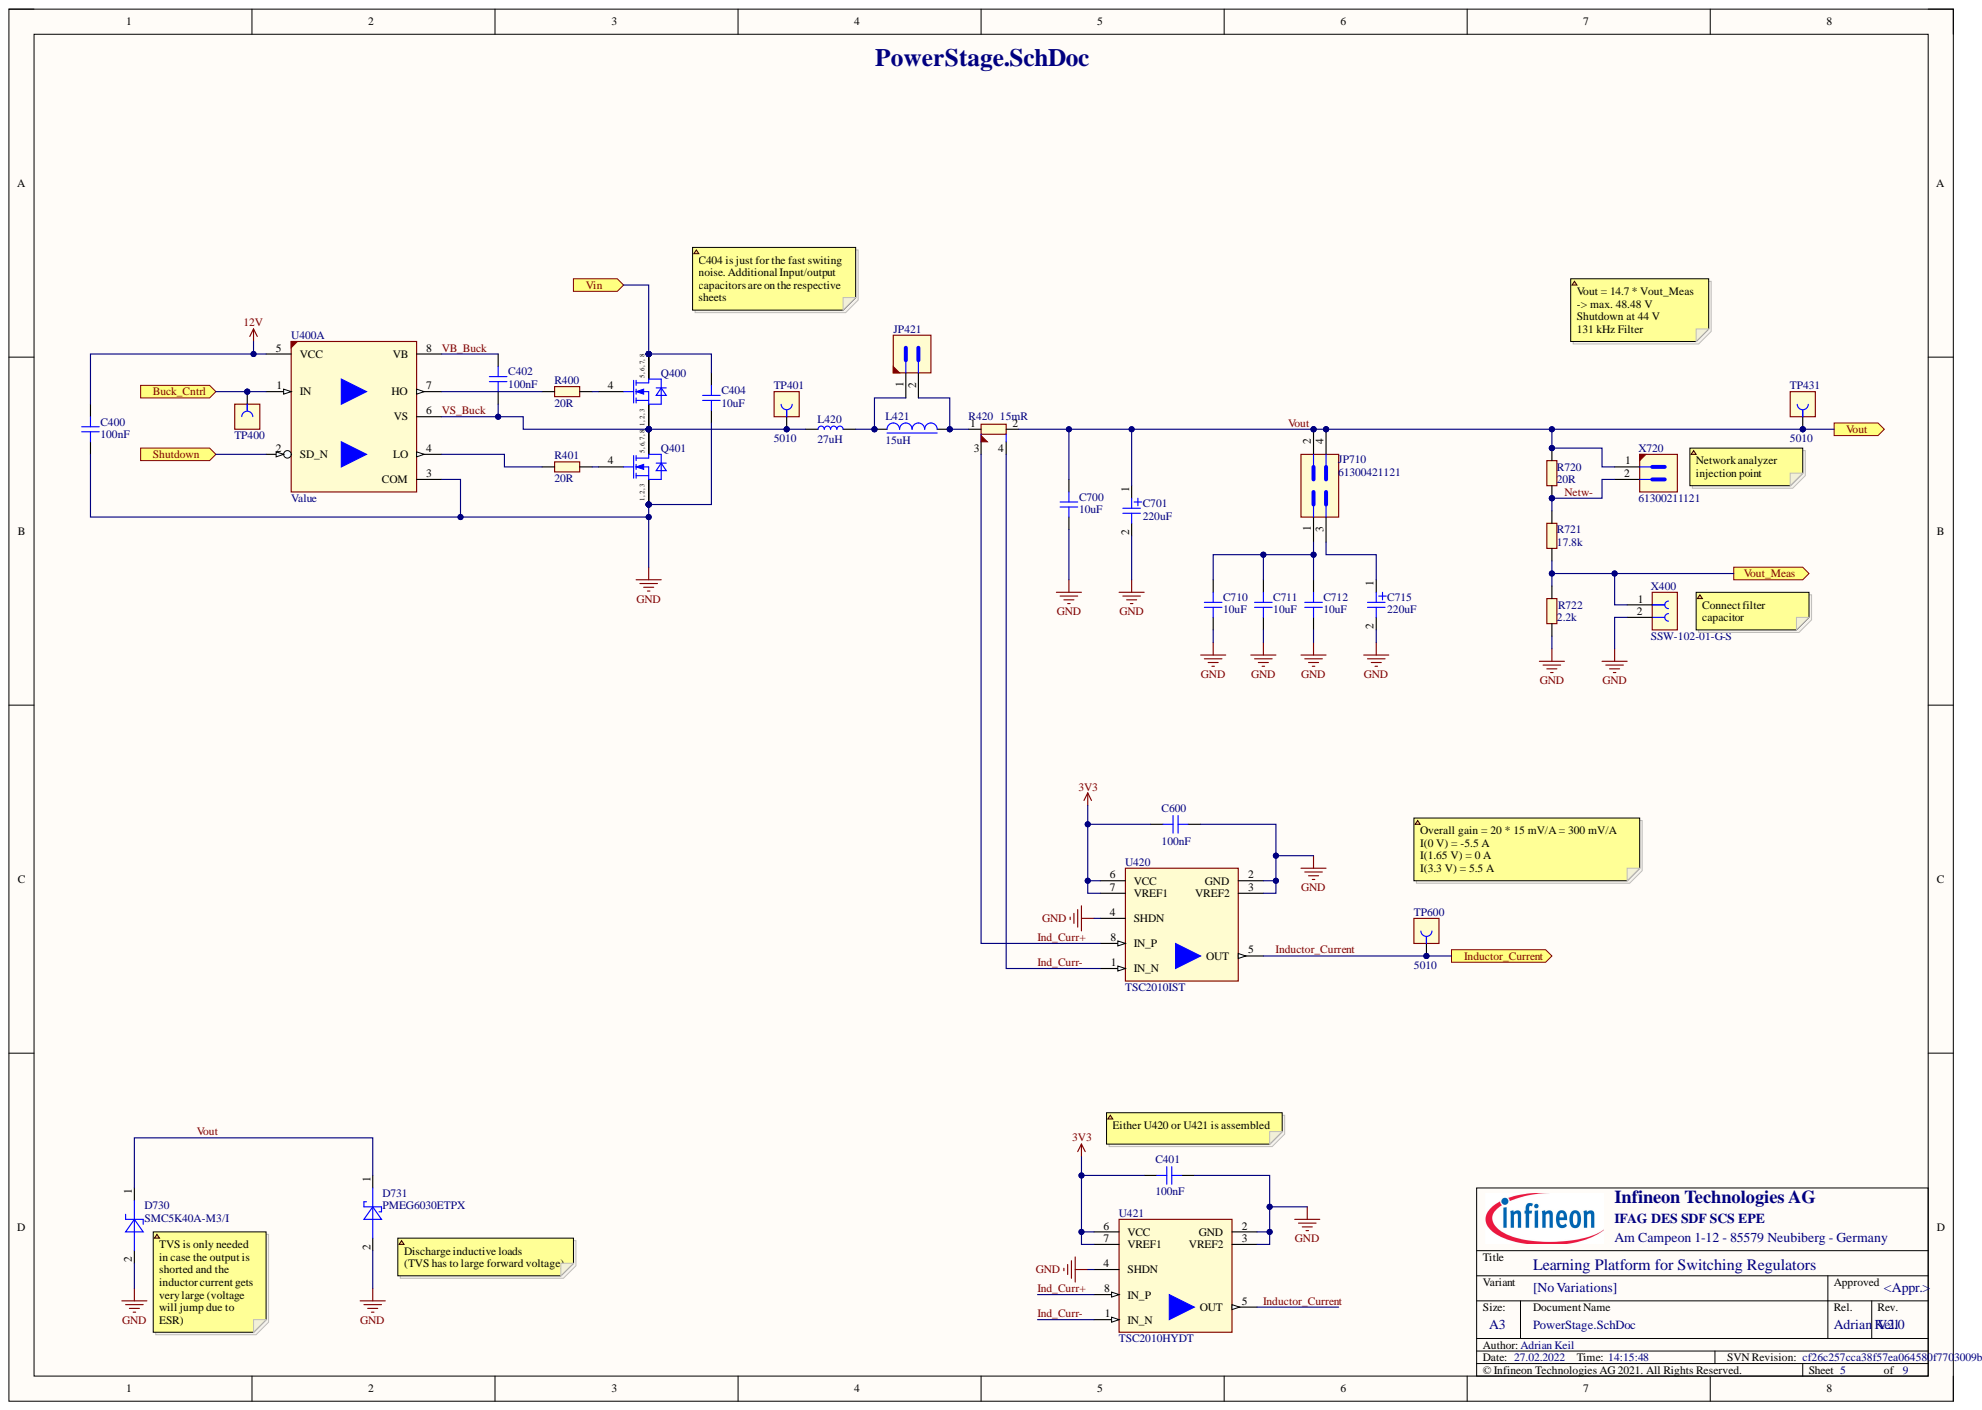
[picture p93: page 4]

C404 is just for the fast switing
noise. AdditionalInput/output
capacitors are on the respective
sheets

SHDN 4

Ind_Curr- | IN_N 1

Either U420 or U421 is assembled

IFAG DES SDF SCS EPE
Am Campeon 1-12 - 85579 Neubiberg - Germany

TVS is only needed
in case the output is
shorted and the
inductor current gets
very large (voltage
will jump due to
ESR)

Discharge inductive loads
(TVS has to large forward voltage)

Learning Platform for Switching Regulators

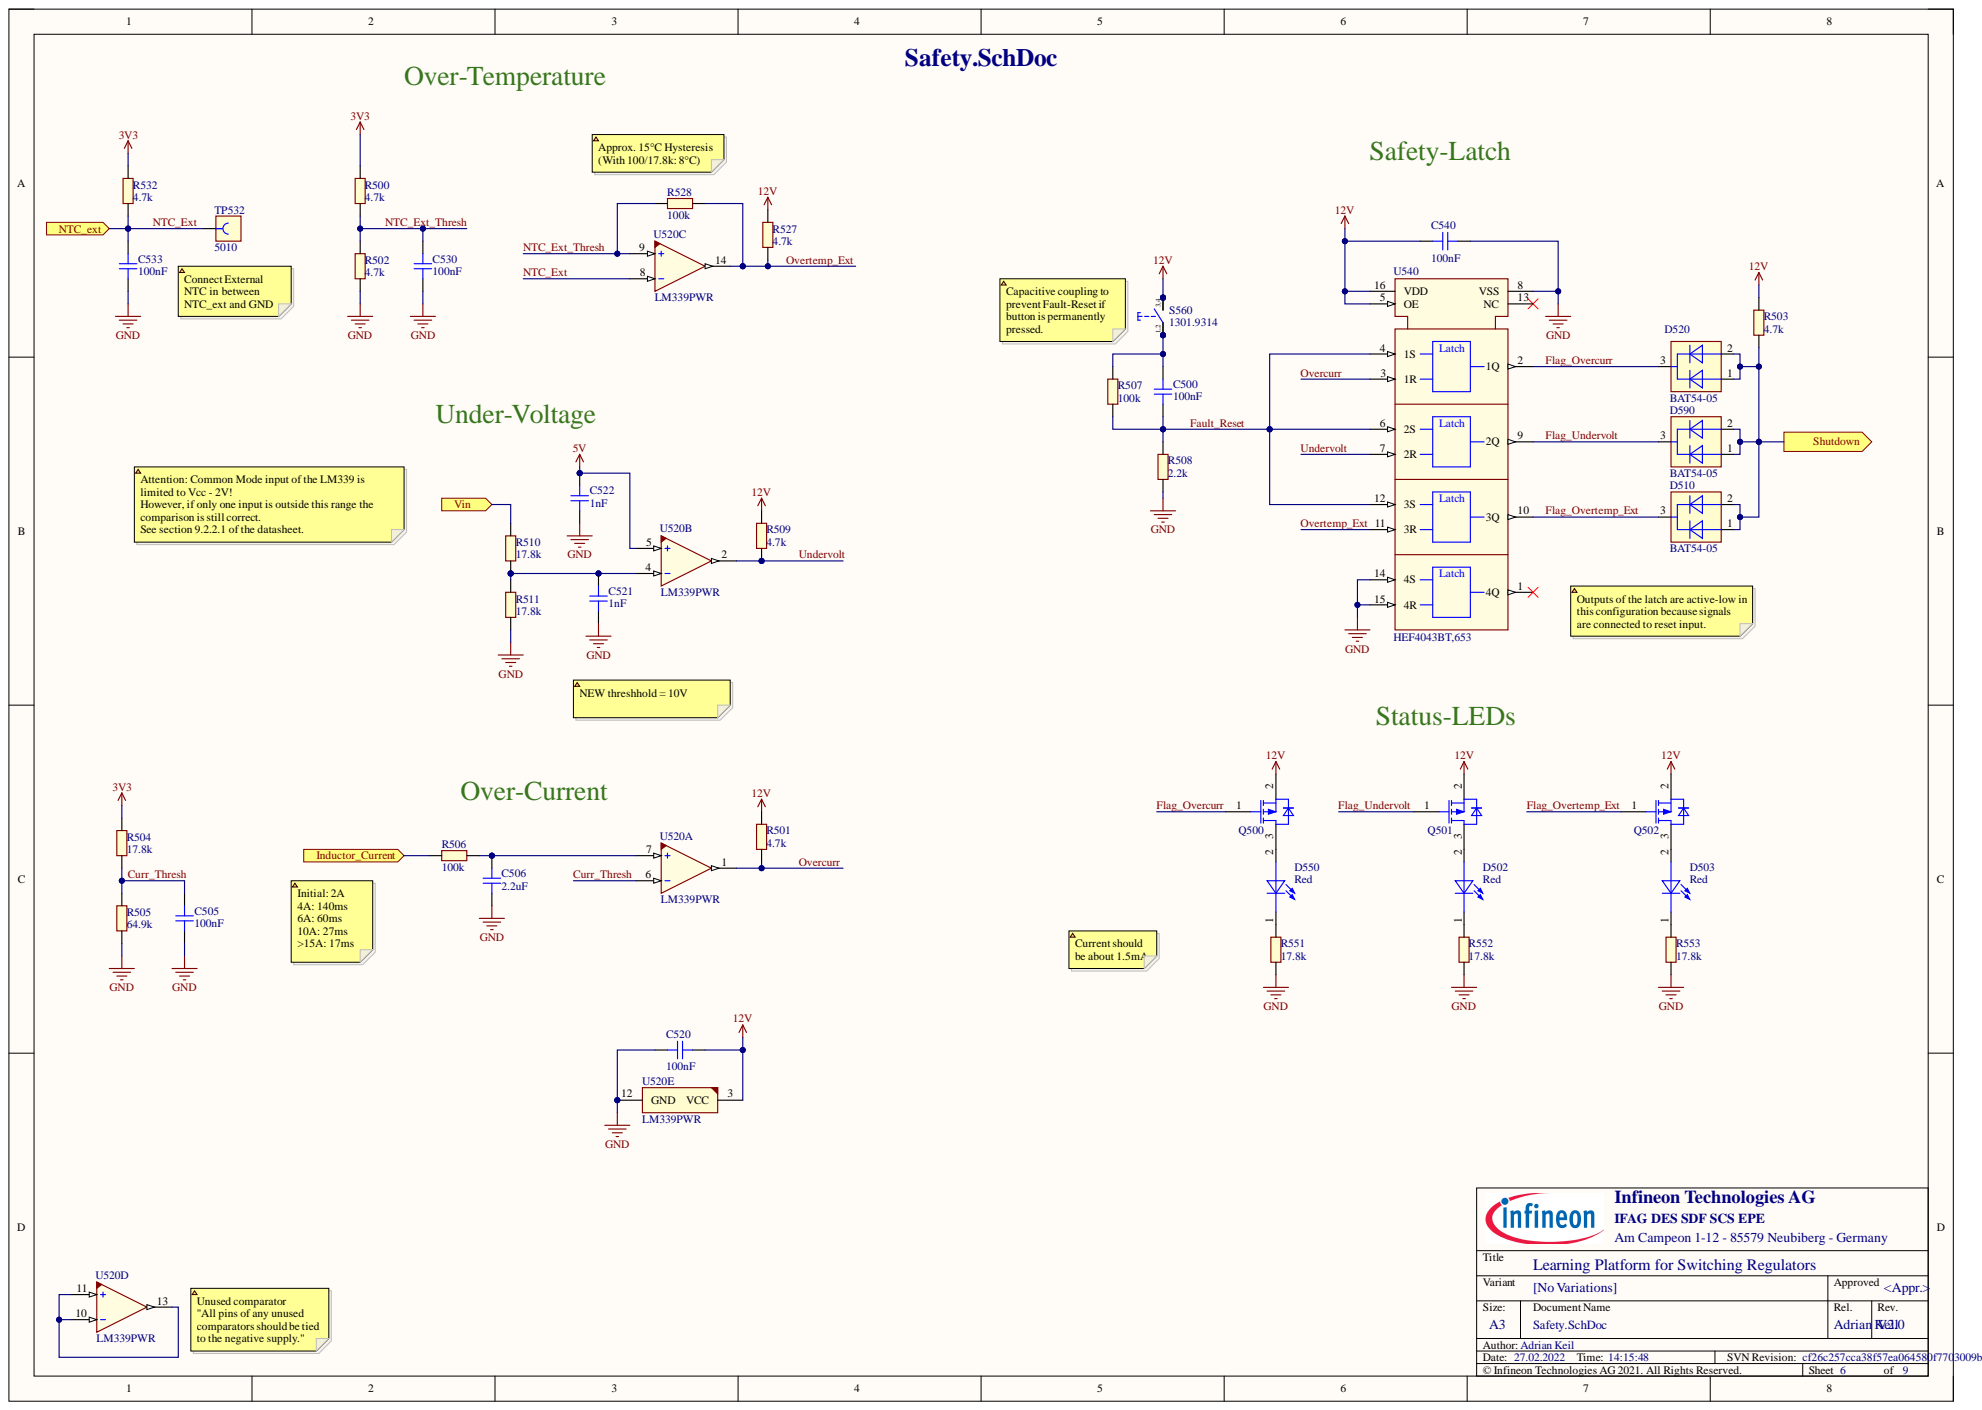
[picture p94: page 5]

Capacitive coupling to
prevent Fault-Reset if
button is permanently
pressed.

Attention: Common Mode input of the LM339 is
limited to Vcc - 2V!
However, if only one input is outside this range the
comparison isstill correct.
See section 9.2.2.1 of the datasheet.

Outputs of the latch are active-low in
this configuration because signals
are connected to reset input.

VCC | 3 GND 12

IFAG DES SDF SCS EPE
Am Campeon 1-12 - 85579 Neubiberg - Germany

Learning Platform for Switching Regulators

Variant [No Variations] | Approved <Appr.>

Unused comparator
"All pins of any unused
comparatorsshould be tied
to the negative supply."

Safety.SchDoc

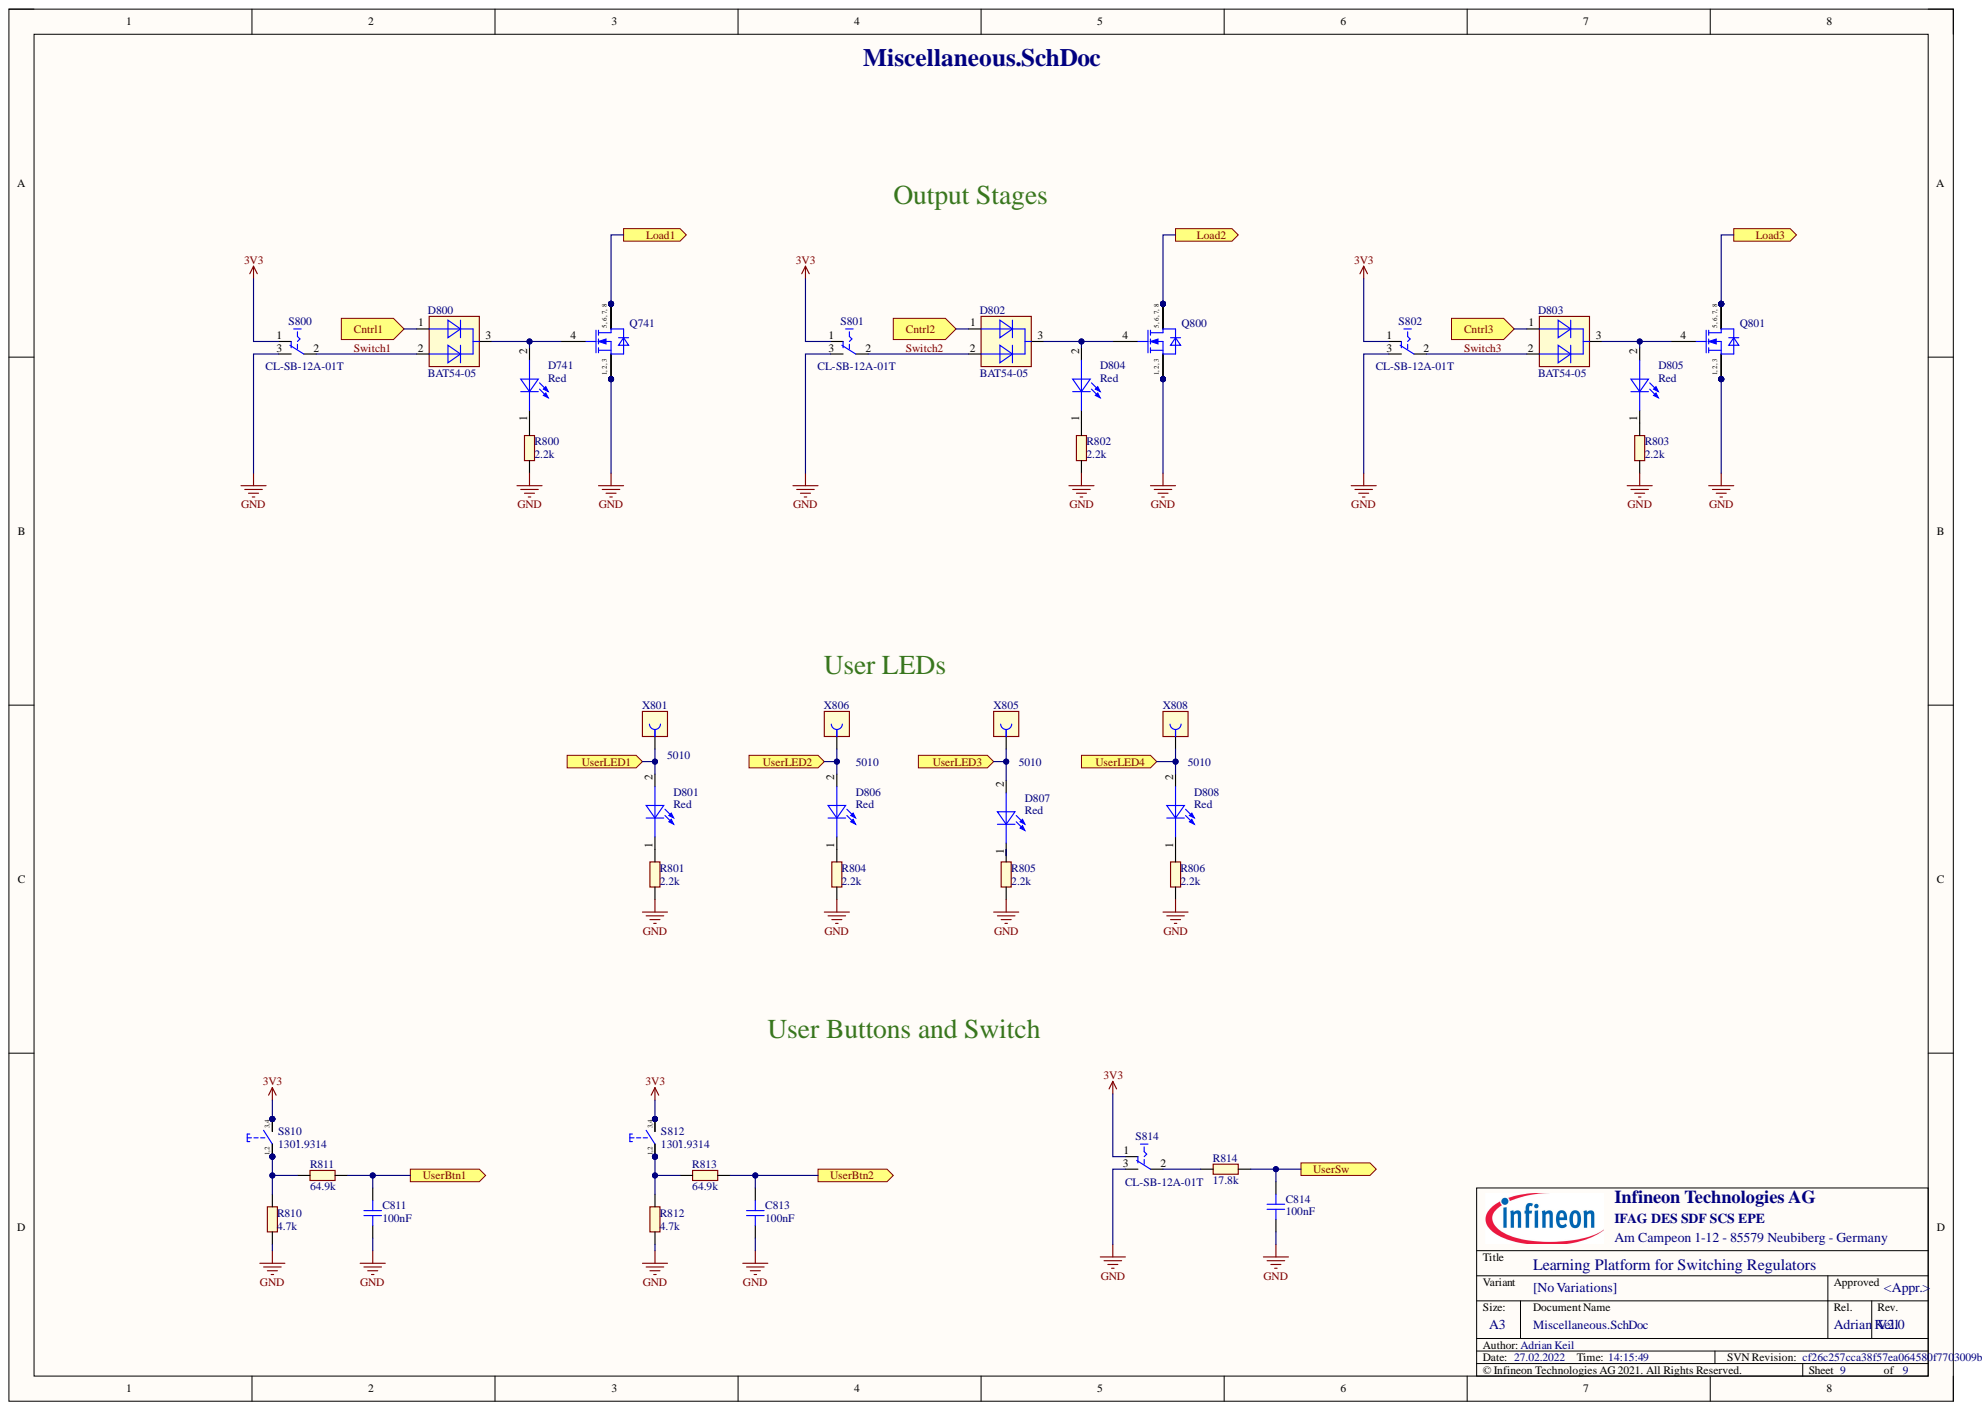
[picture p95: page 6]

User Buttons and Switch

IFAG DES SDF SCS EPE
Am Campeon 1-12 - 85579 Neubiberg - Germany

Learning Platform for Switching Regulators

Variant [No Variations] | Approved <Appr.>

Miscellaneous.SchDoc
