Infineon/voltage-regulator-learning-platform/Version1.0/Project Outputs/PDF/PCB Documentation.PDF

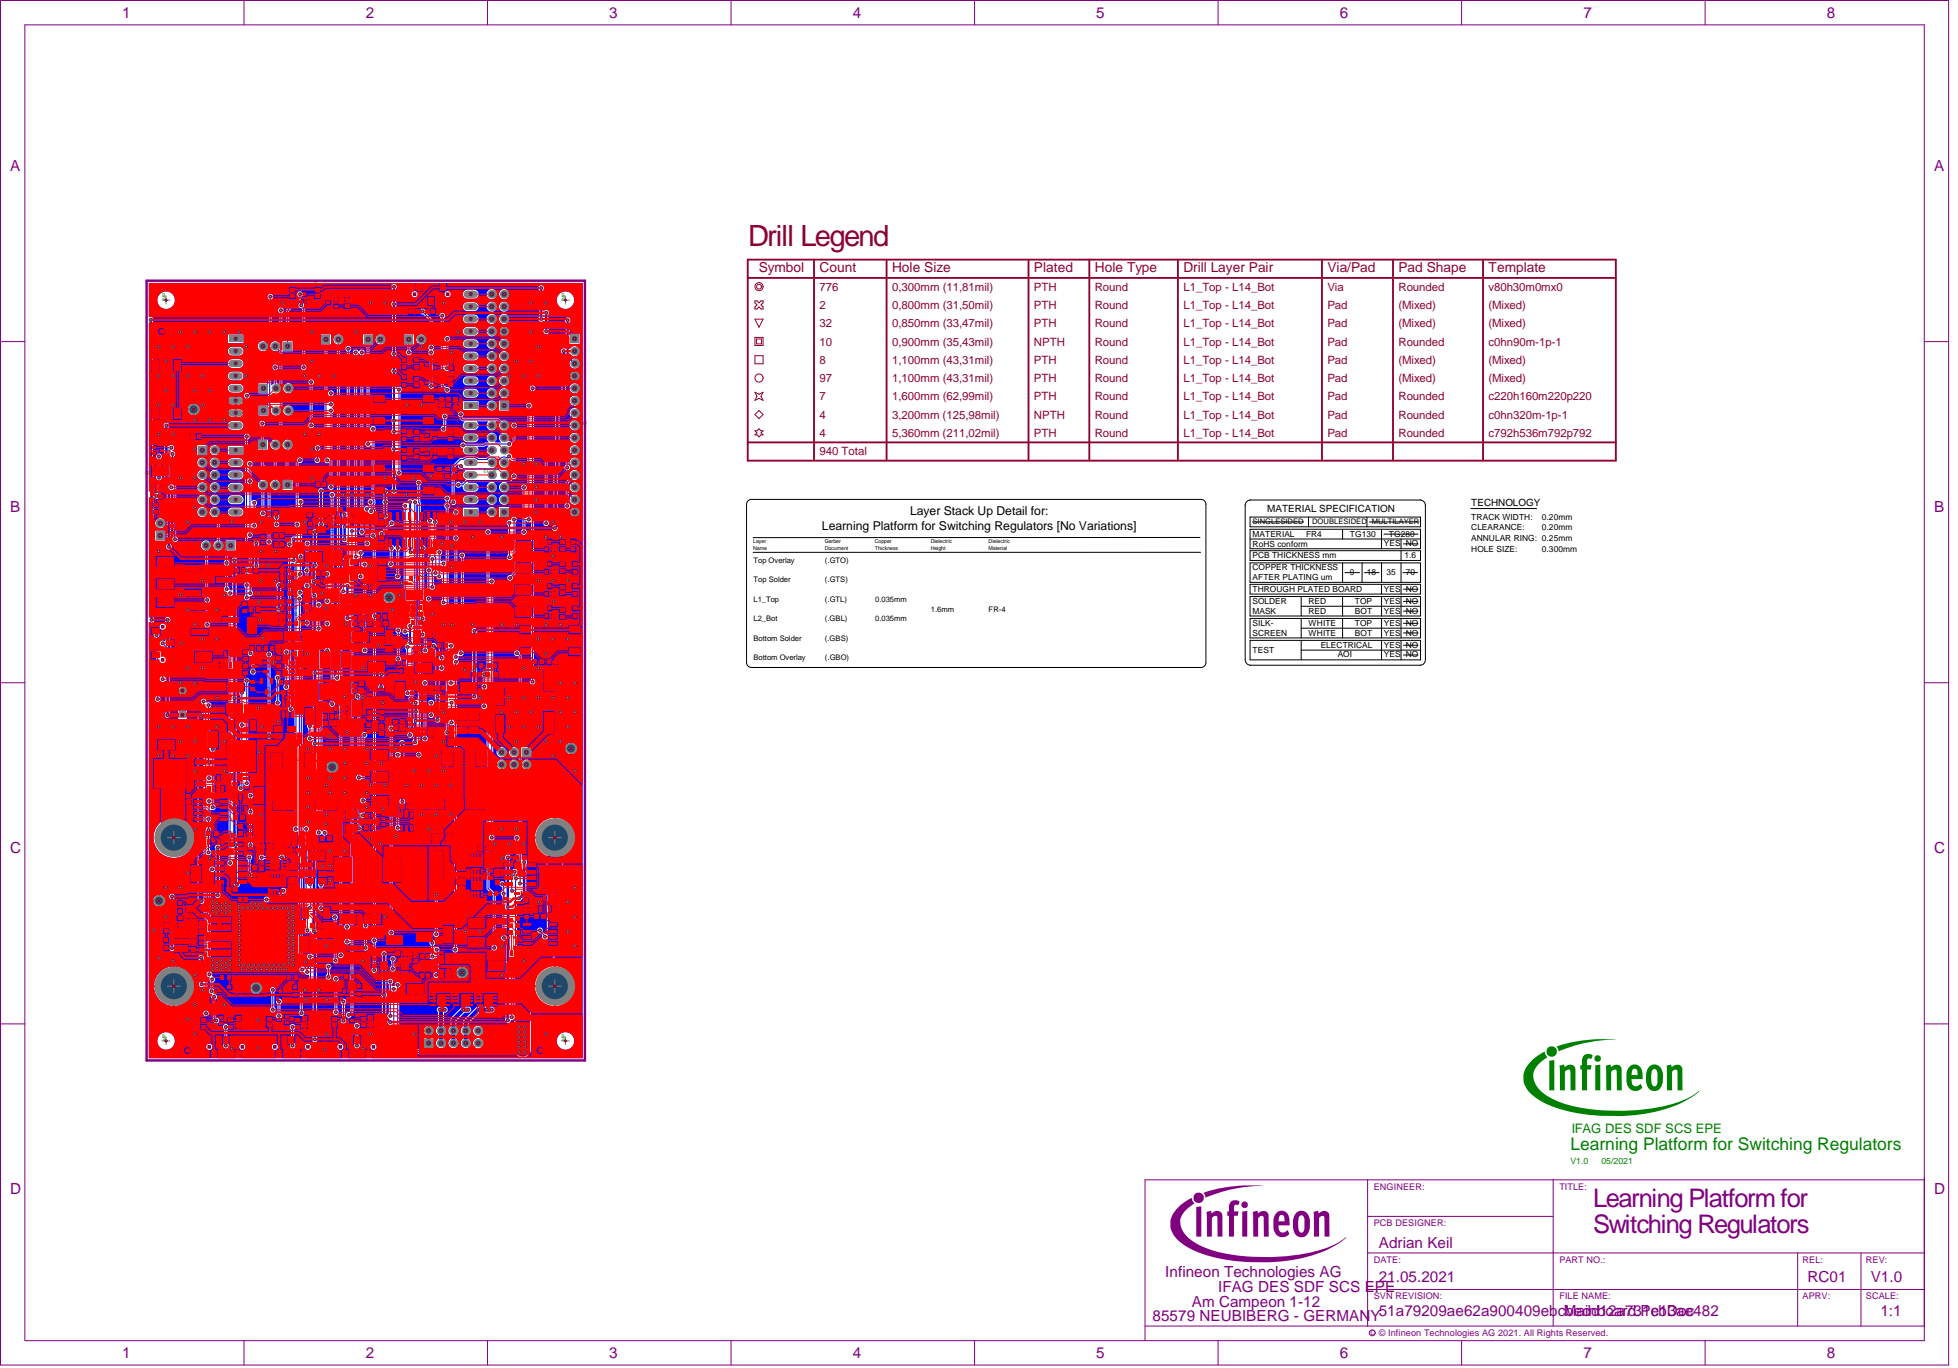
[picture p96: page 1]

Layer Stack Up Detail for:

Learning Platform for Switching Regulators [No Variations]

IFAG DES SDF SCS EPE
Learning Platform for Switching Regulators

Am Campeon 1-12
85579 NEUBIBERG - GERMANY

C © Infineon Technologies AG 2021. All Rights Reserved.
