Infineon/voltage-regulator-learning-platform/Version1.0/Project Outputs/PDF/PCB 3D Prints_Bottom.PDF

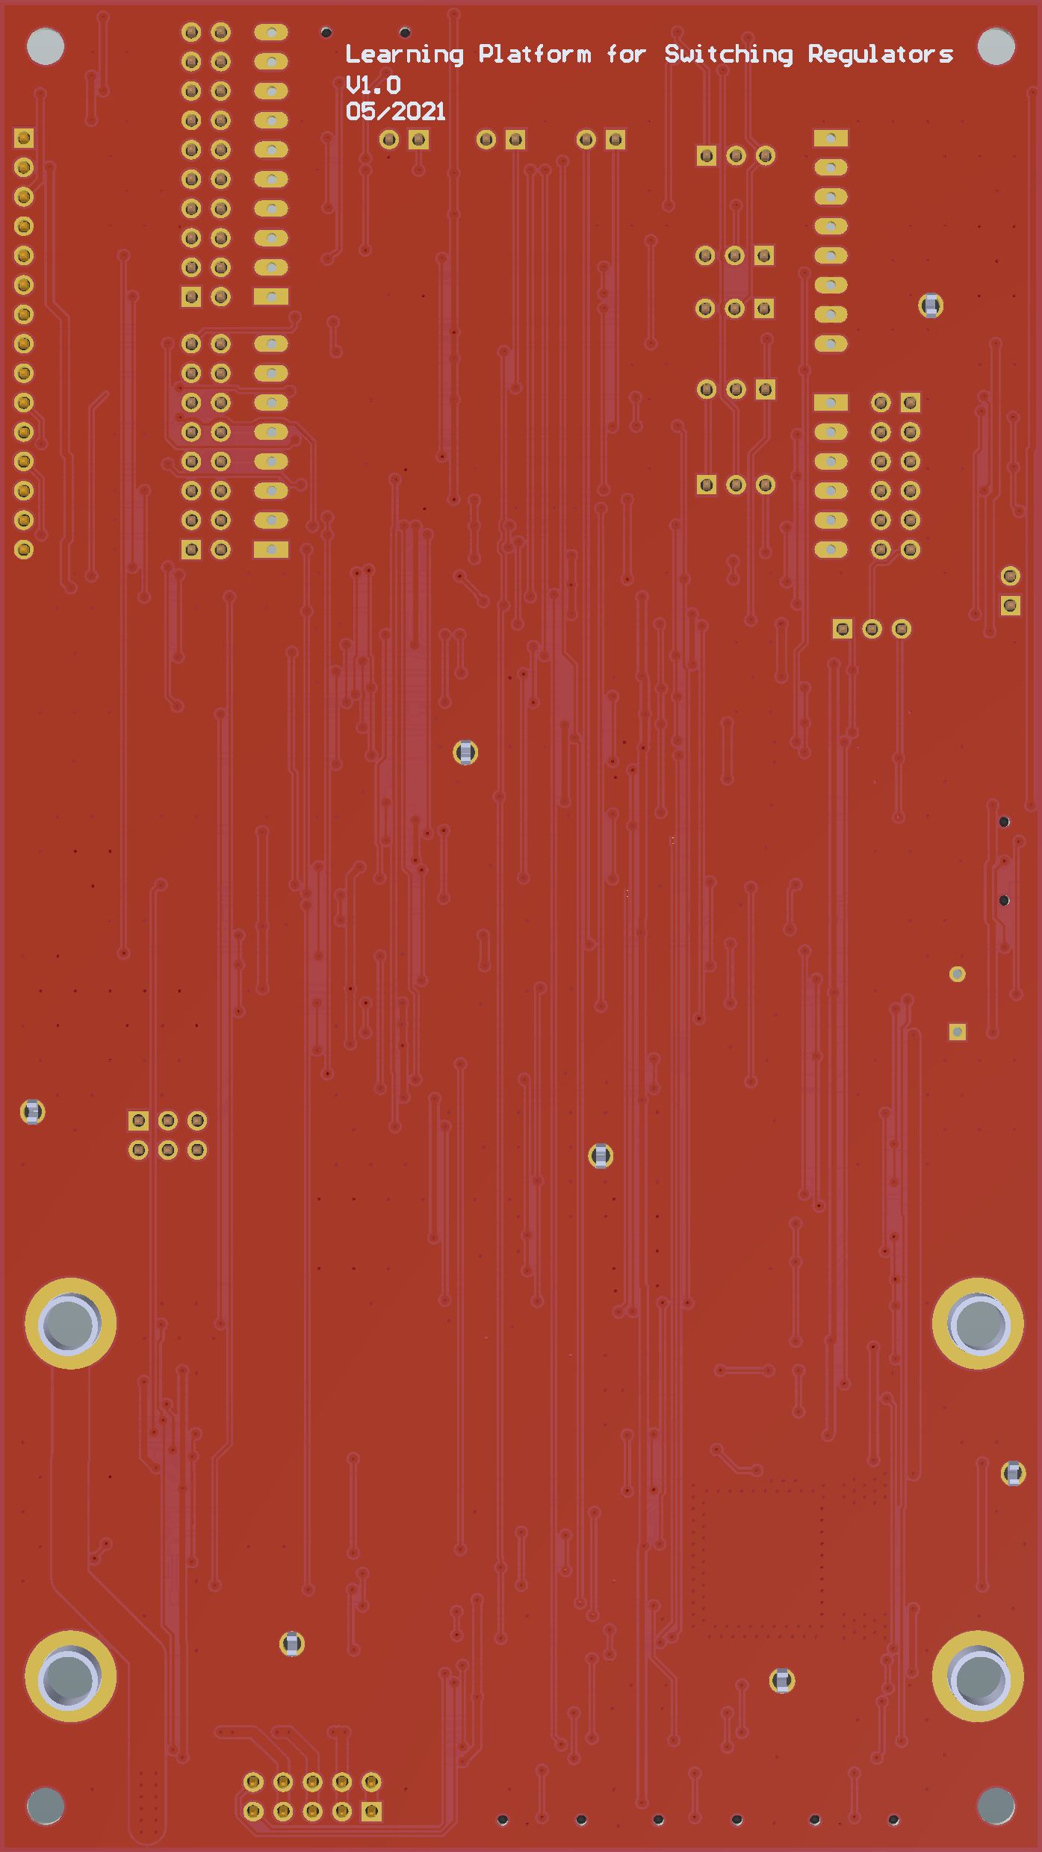
[picture p100: page 1]
