Infineon/voltage-regulator-learning-platform/Version1.0/Project Outputs/PDF/PCB Prints.PDF

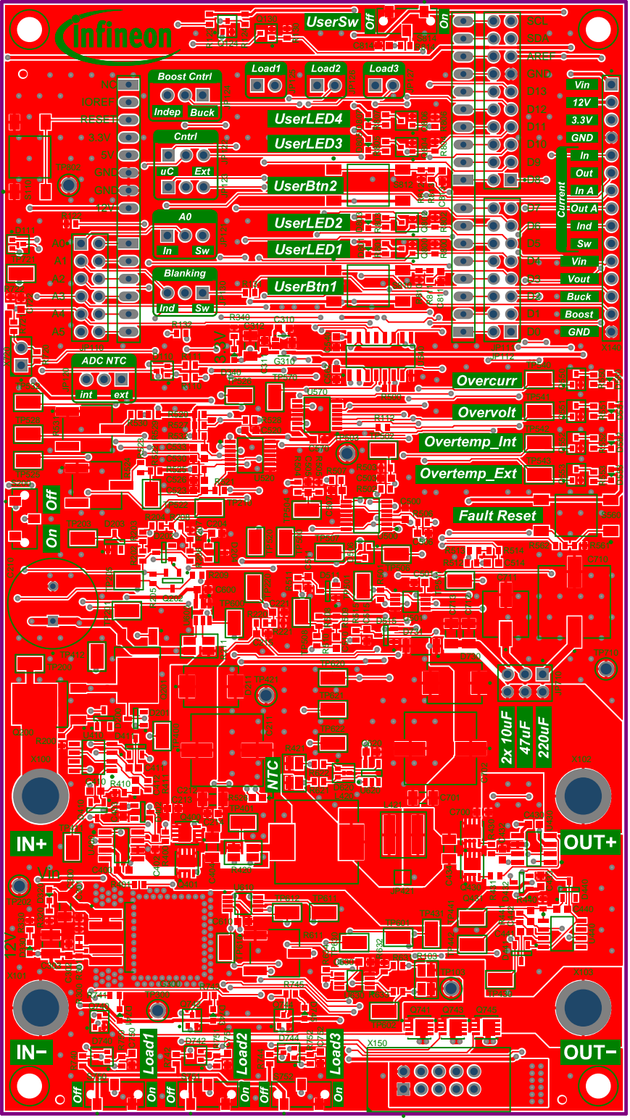
[picture p101: page 1]

SCL SDA

AREF

D2
D1

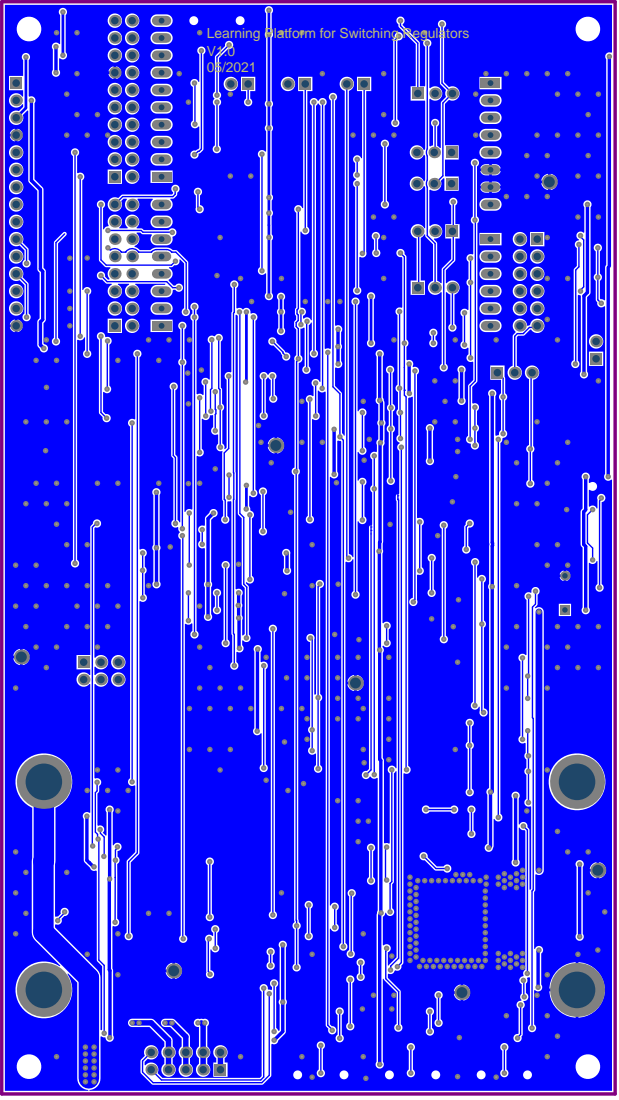
[picture p102: page 2]
