Infineon/voltage-regulator-learning-platform/Version1.1/Project Outputs/PDF/Assembling.PDF

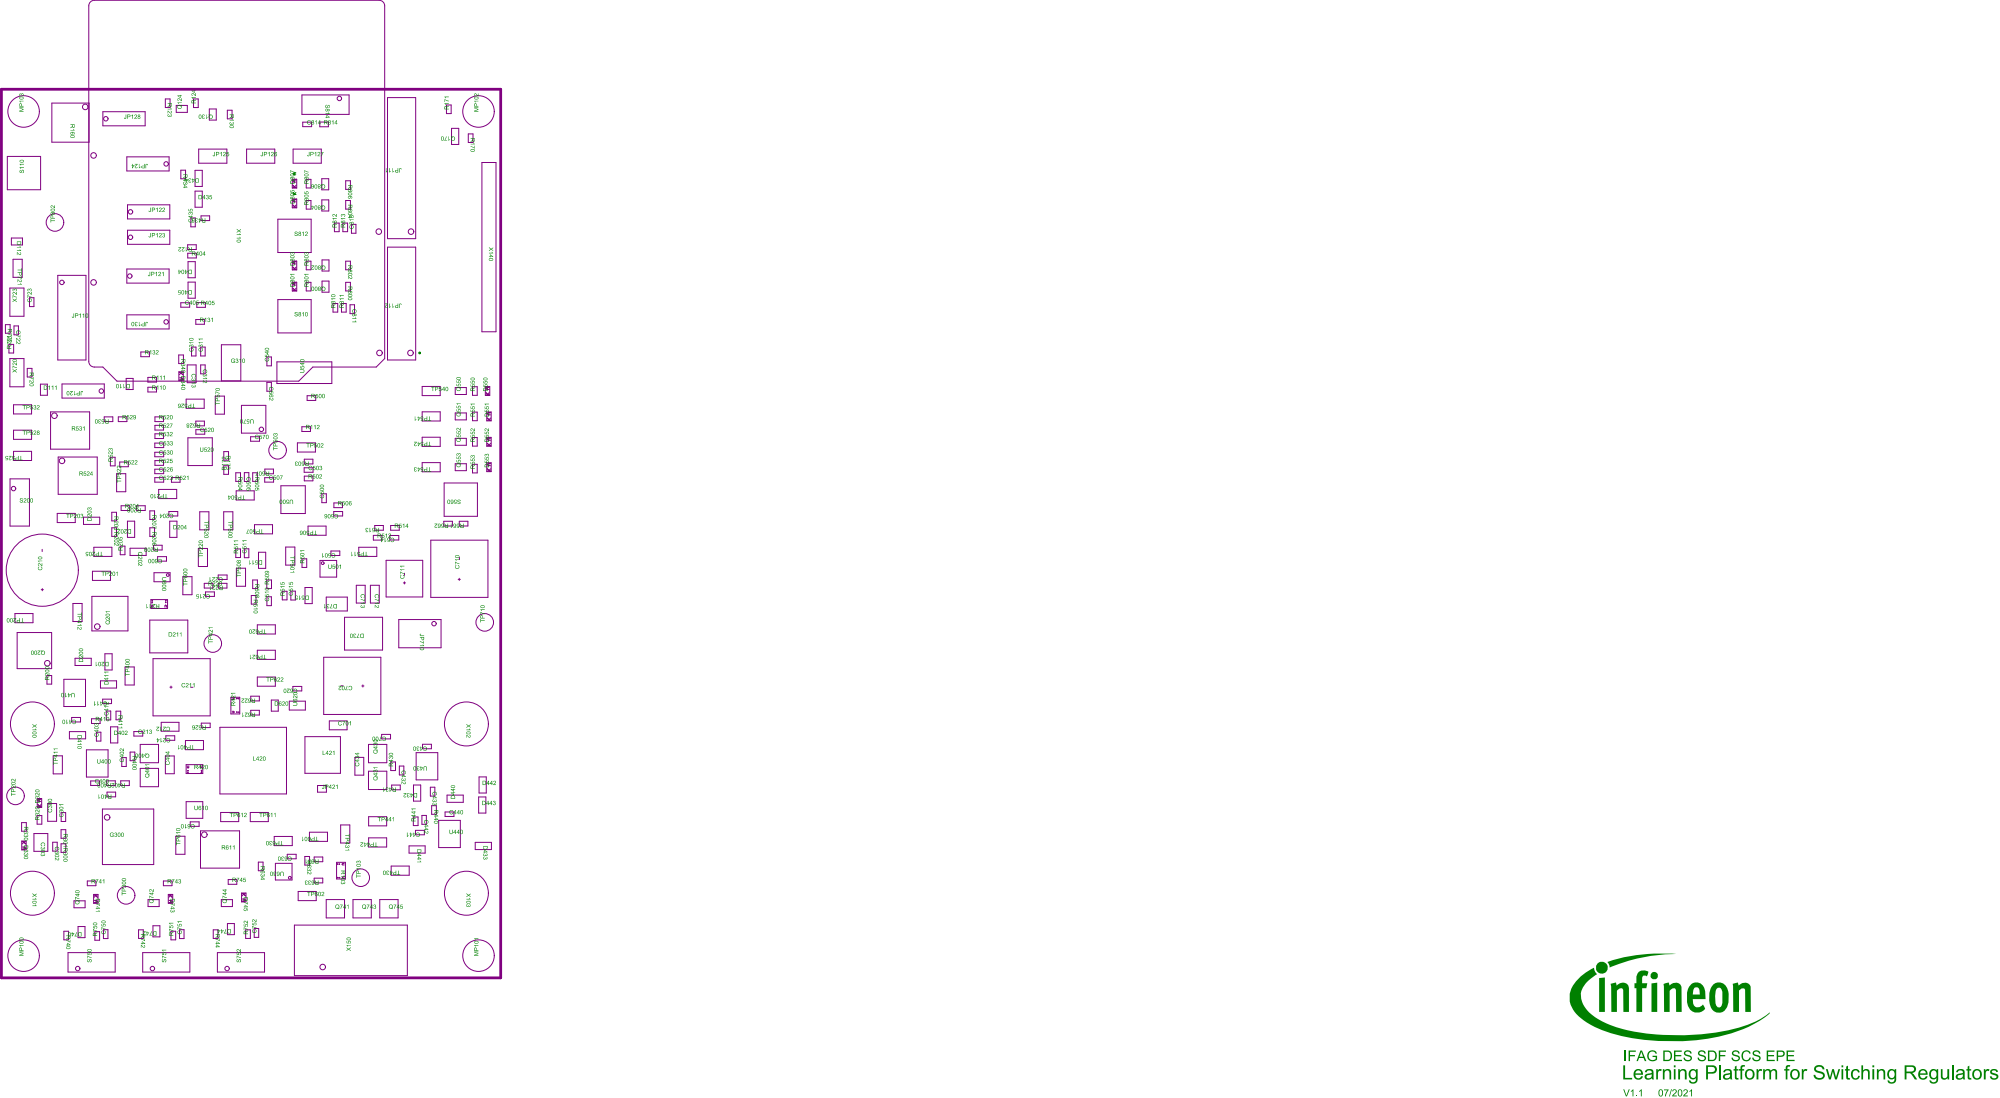
[picture p103: page 1]

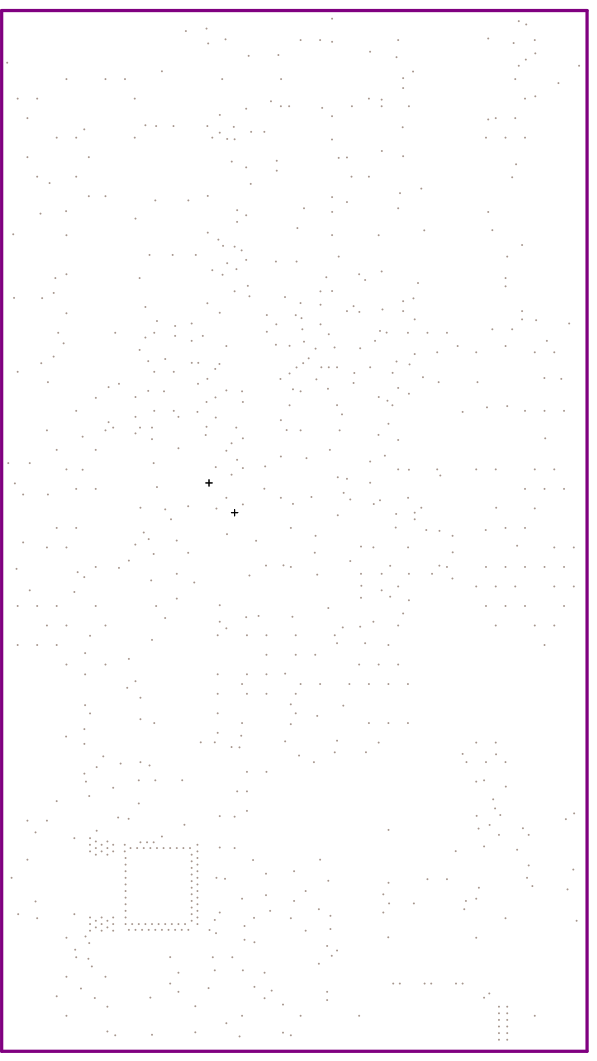
[picture p104: page 2]
