Infineon/voltage-regulator-learning-platform/Version1.1/Project Outputs/PDF/PCB 3D Prints.PDF

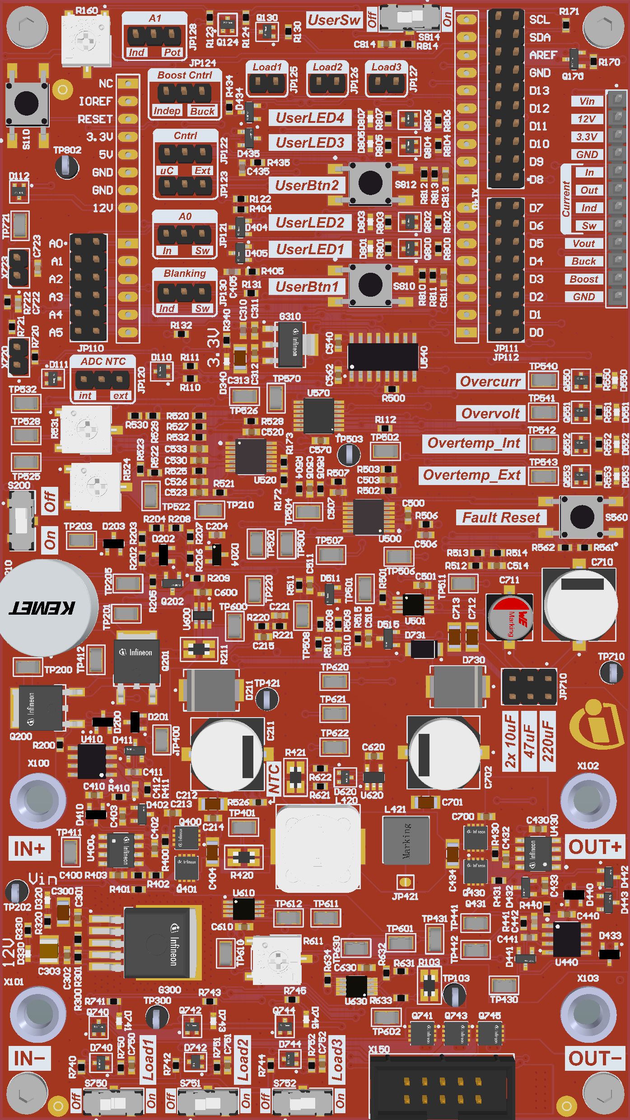
[picture p105: page 1]
