Infineon/voltage-regulator-learning-platform/Version1.1/Project Outputs/PDF/PCB 3D Prints_Bottom.PDF

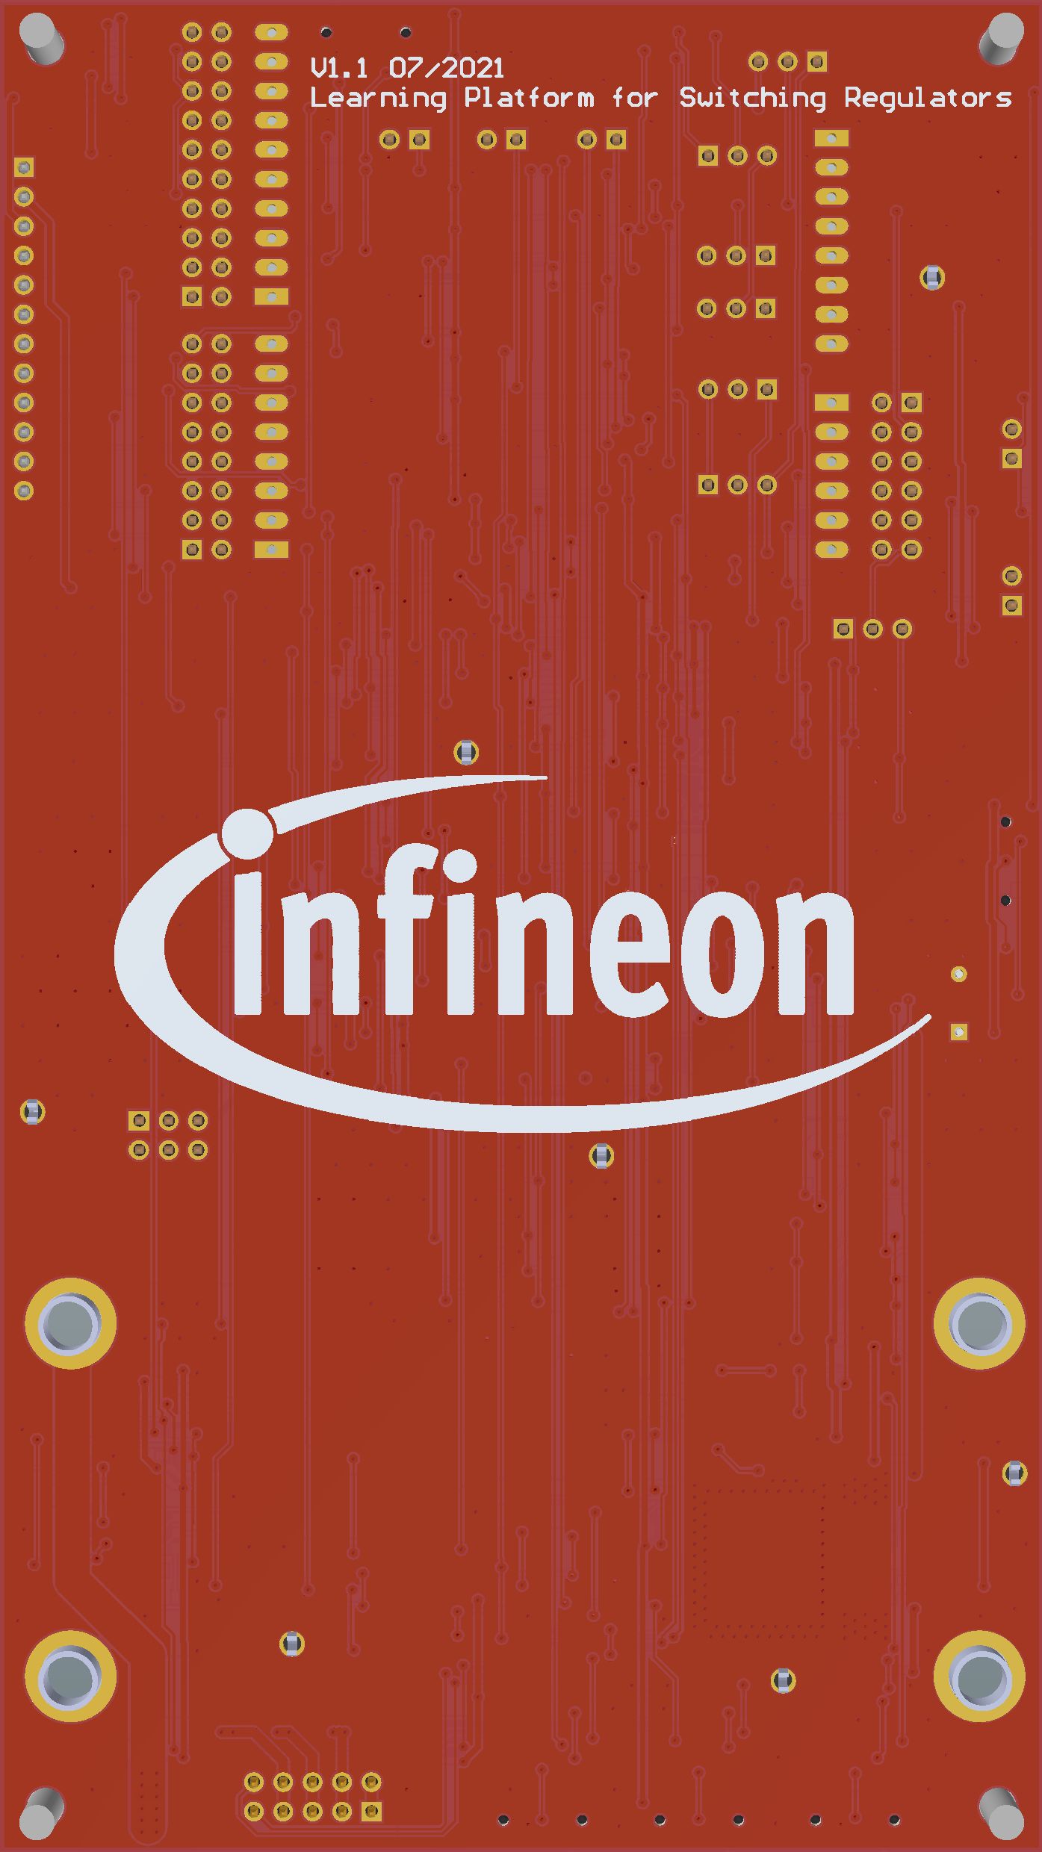
[picture p106: page 1]
