Infineon/voltage-regulator-learning-platform/Version1.2/Project Outputs/PDF/Assembling.PDF

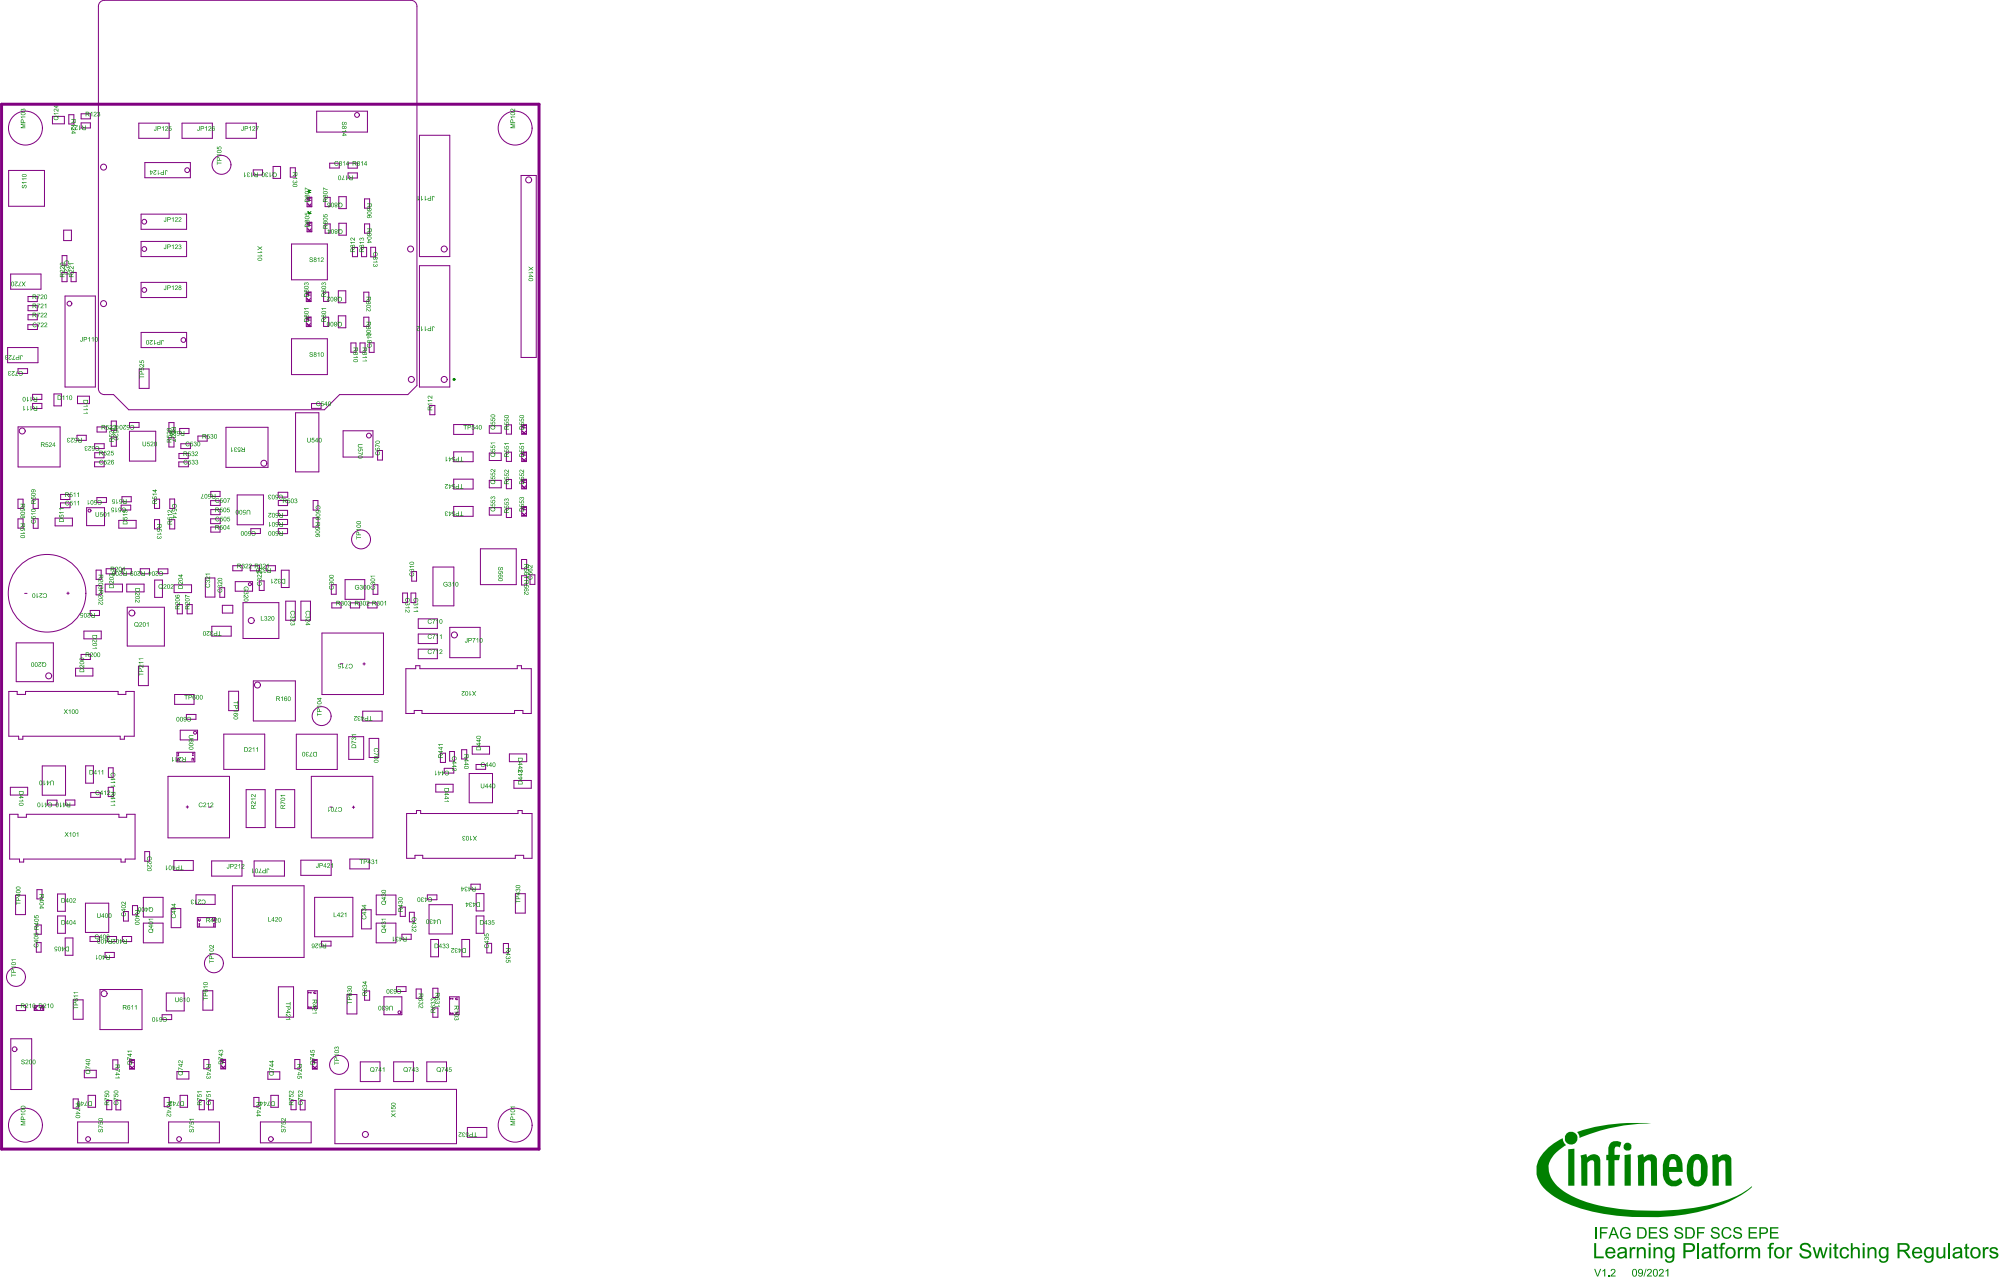
[picture p107: page 1]

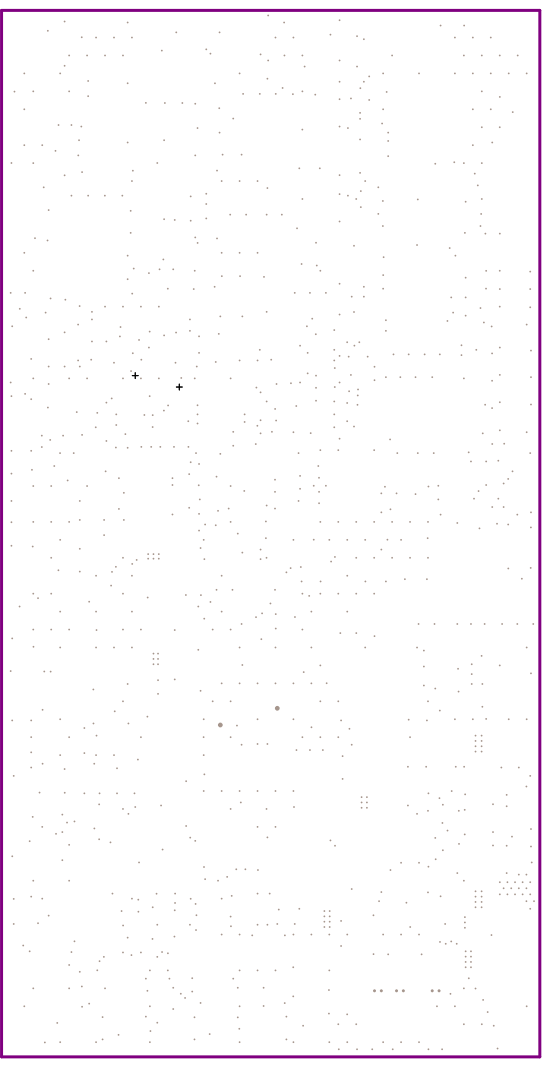
[picture p108: page 2]
