Infineon/voltage-regulator-learning-platform/Version1.2/Project Outputs/PDF/PCB 3D Prints.PDF

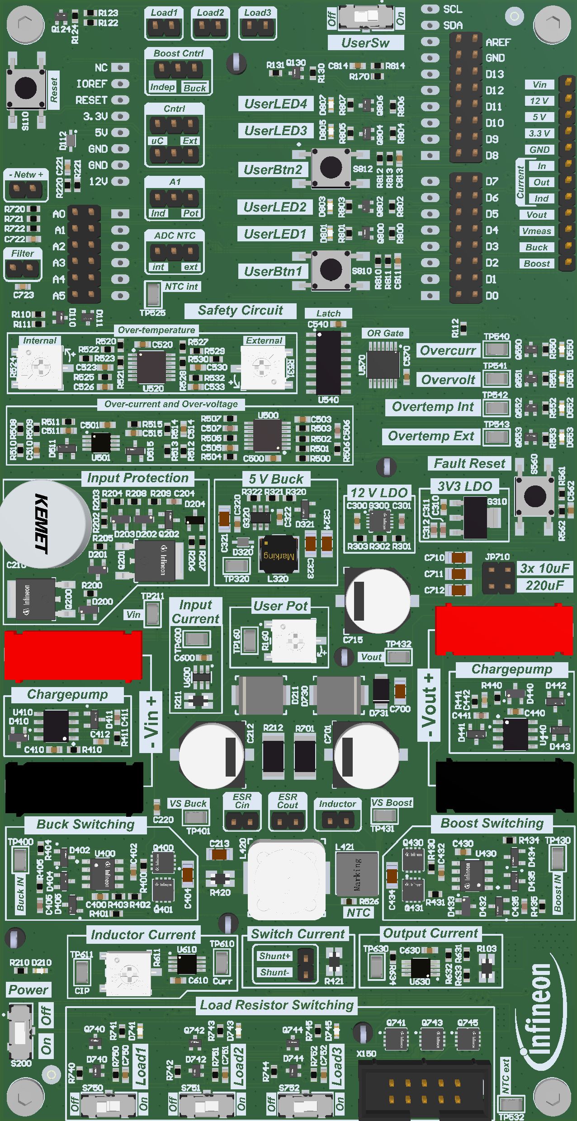
[picture p109: page 1]
