Infineon/voltage-regulator-learning-platform/Version1.2/Project Outputs/PDF/PCB 3D Prints_Bottom.PDF

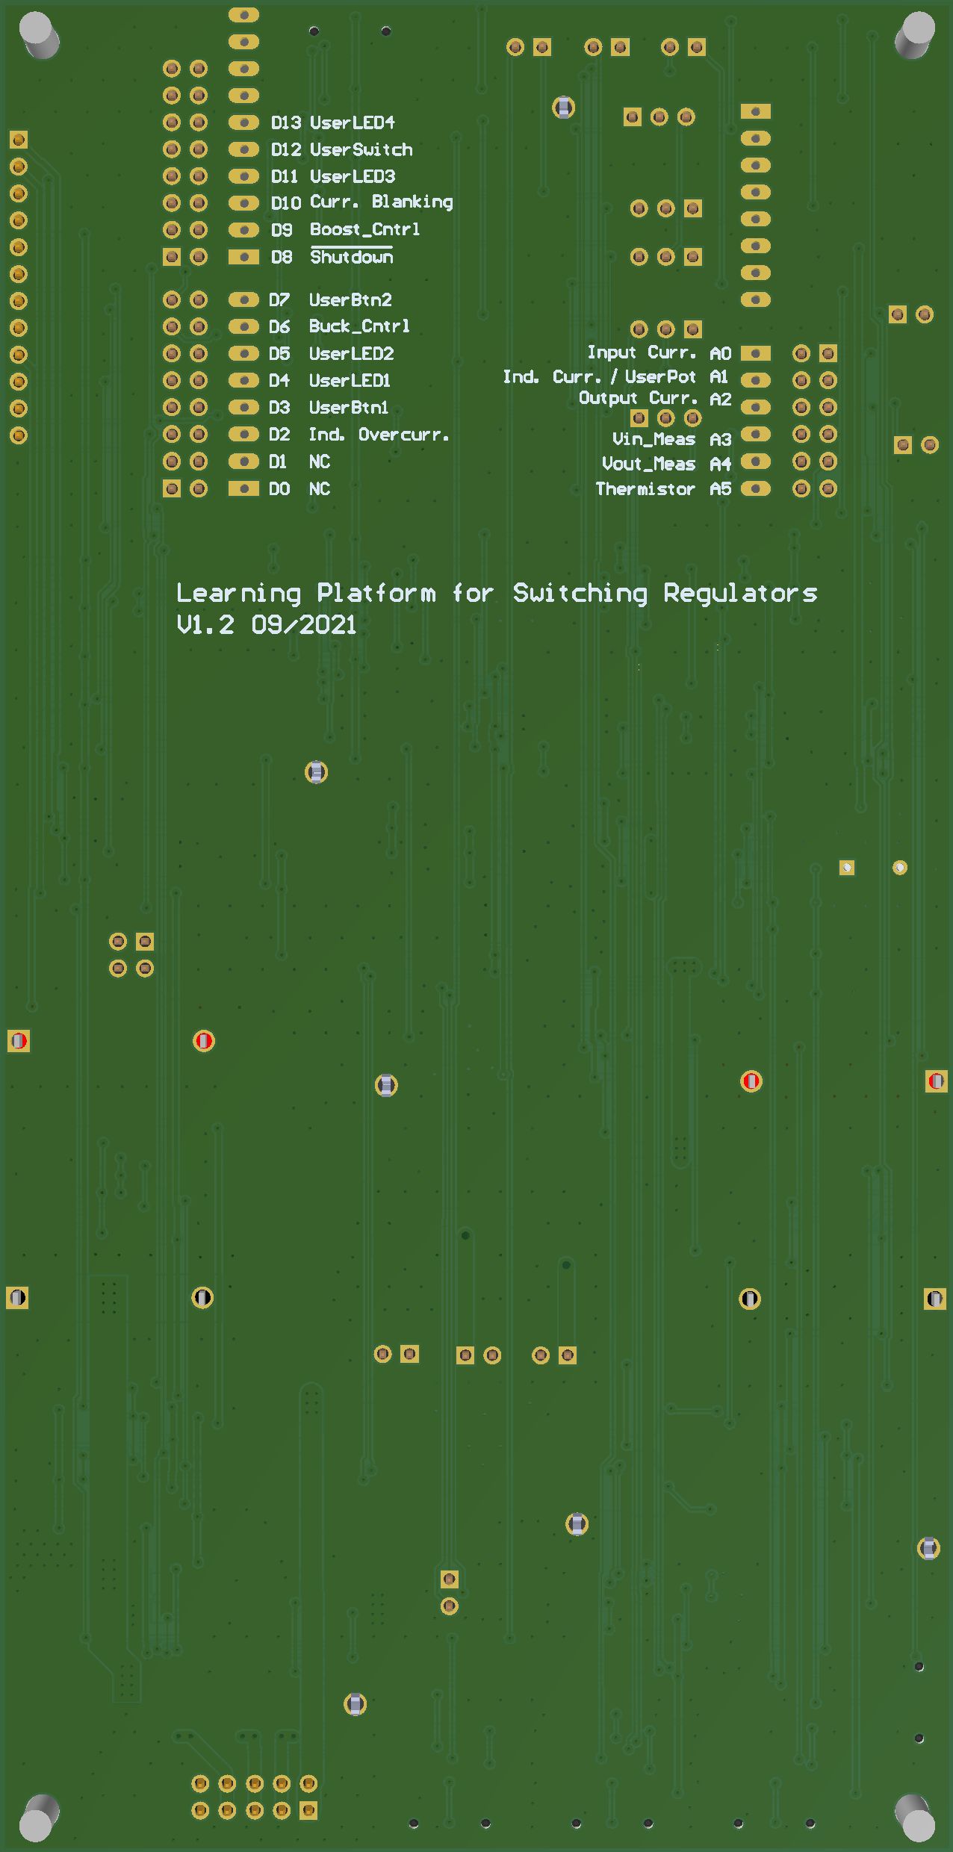
[picture p110: page 1]
