Infineon/voltage-regulator-learning-platform/Version1.0/Project Outputs/PDF/Silkmask.PDF

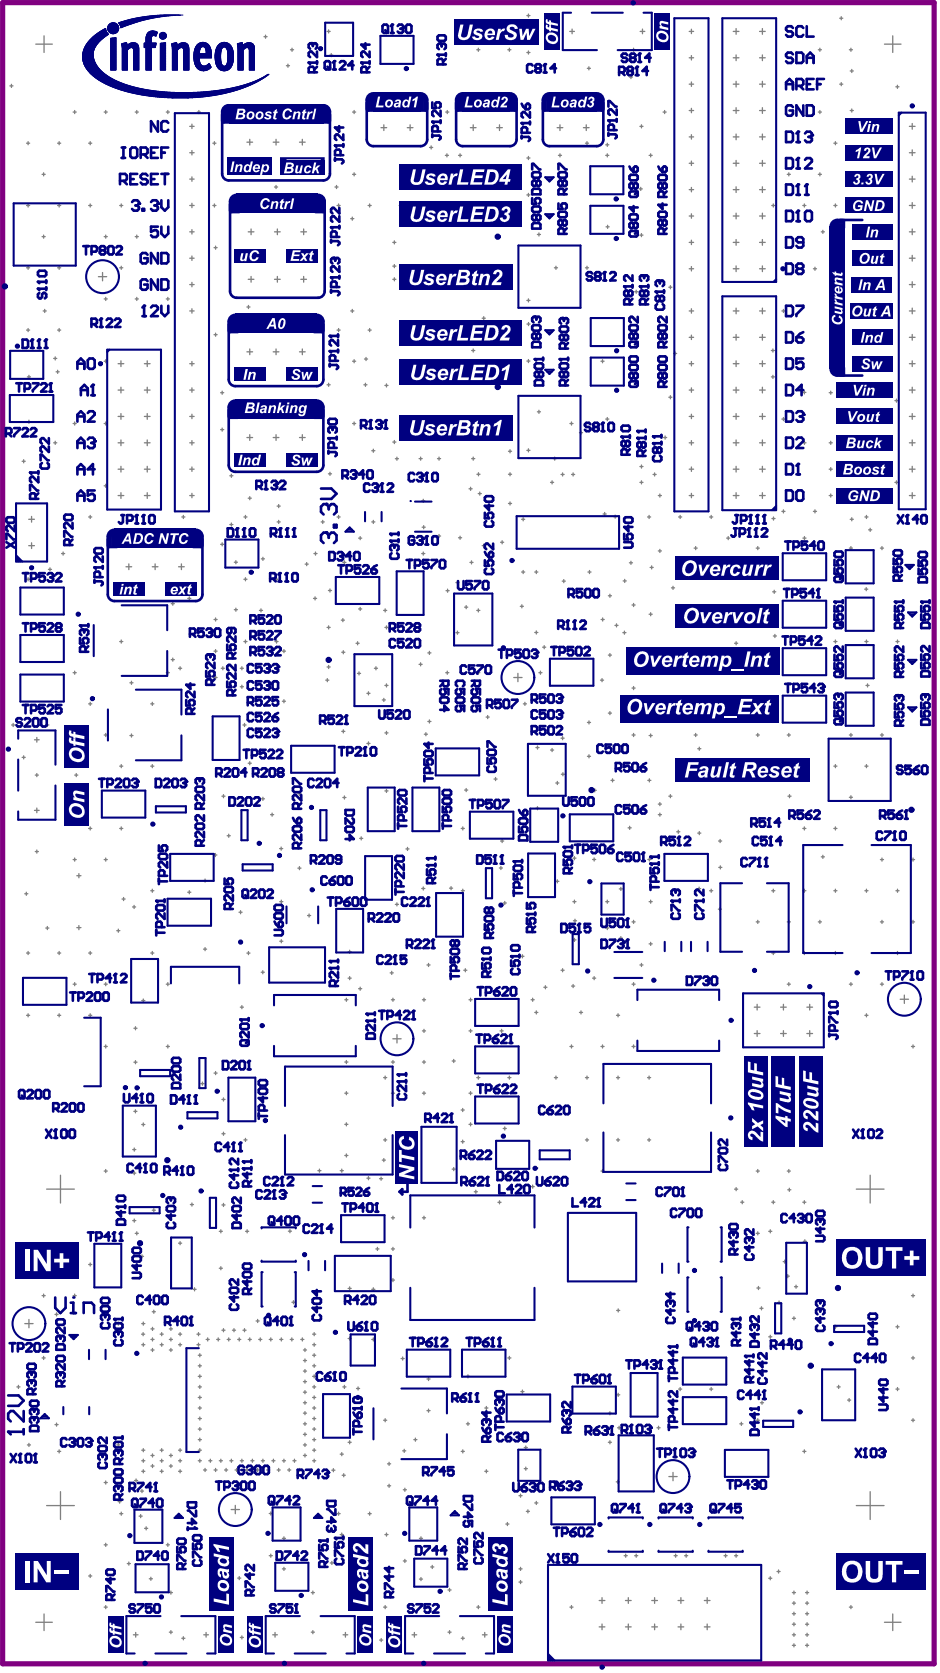
[picture p111: page 1]

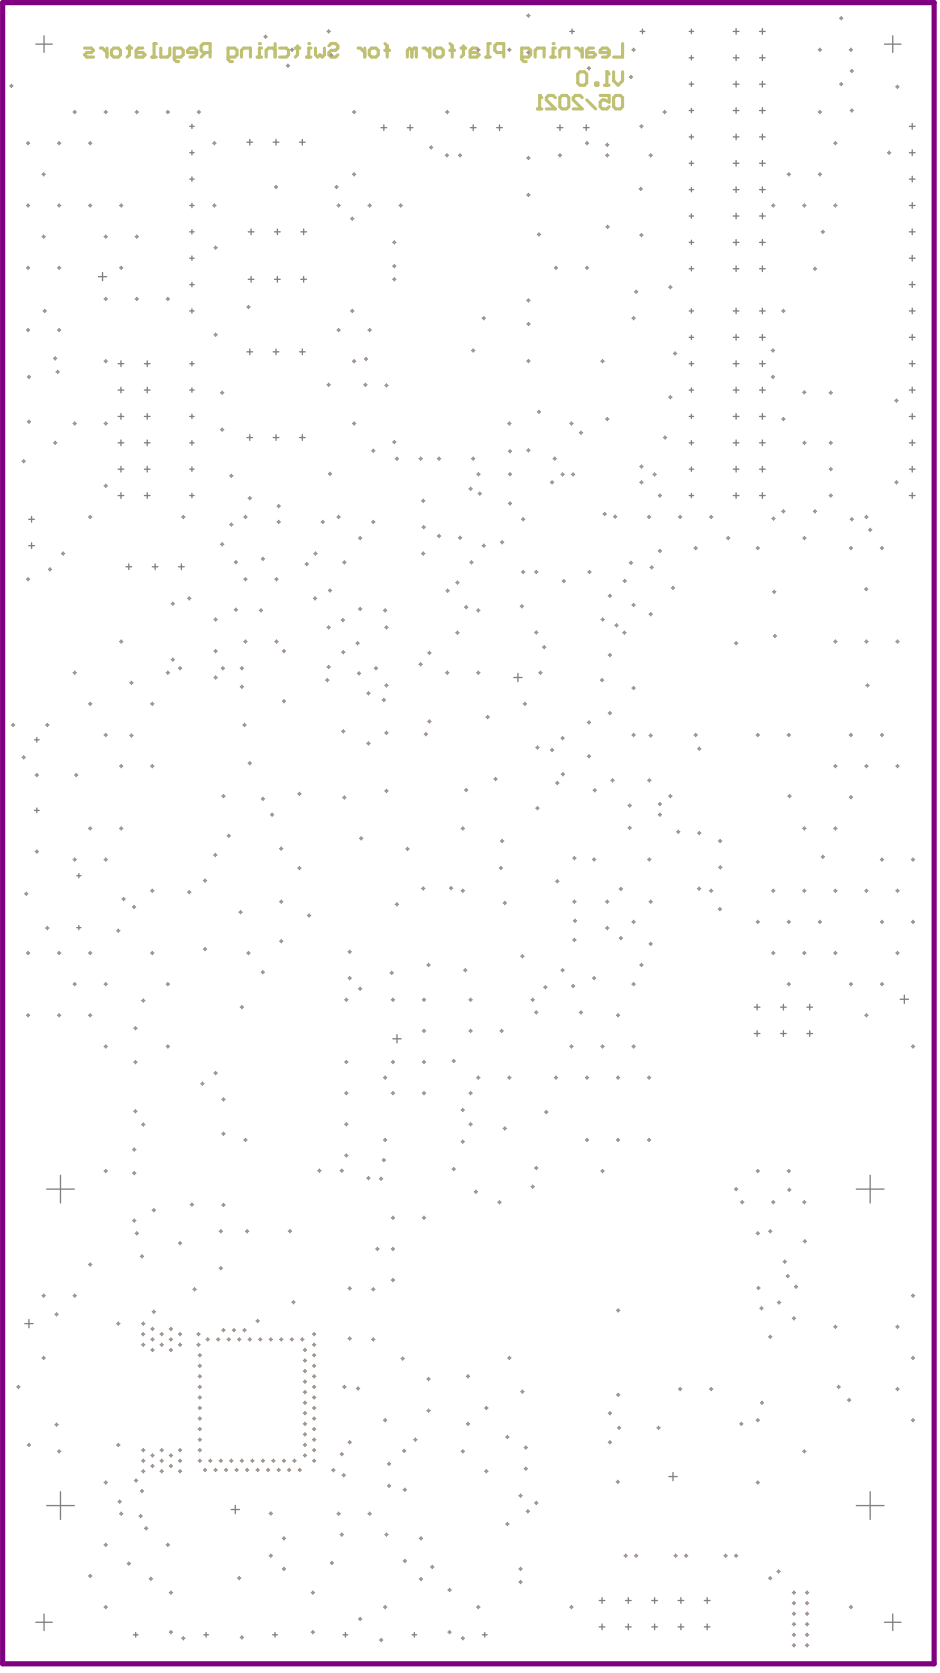
[picture p112: page 2]
