Infineon/voltage-regulator-learning-platform/Version1.1/Project Outputs/PDF/Silkmask.PDF

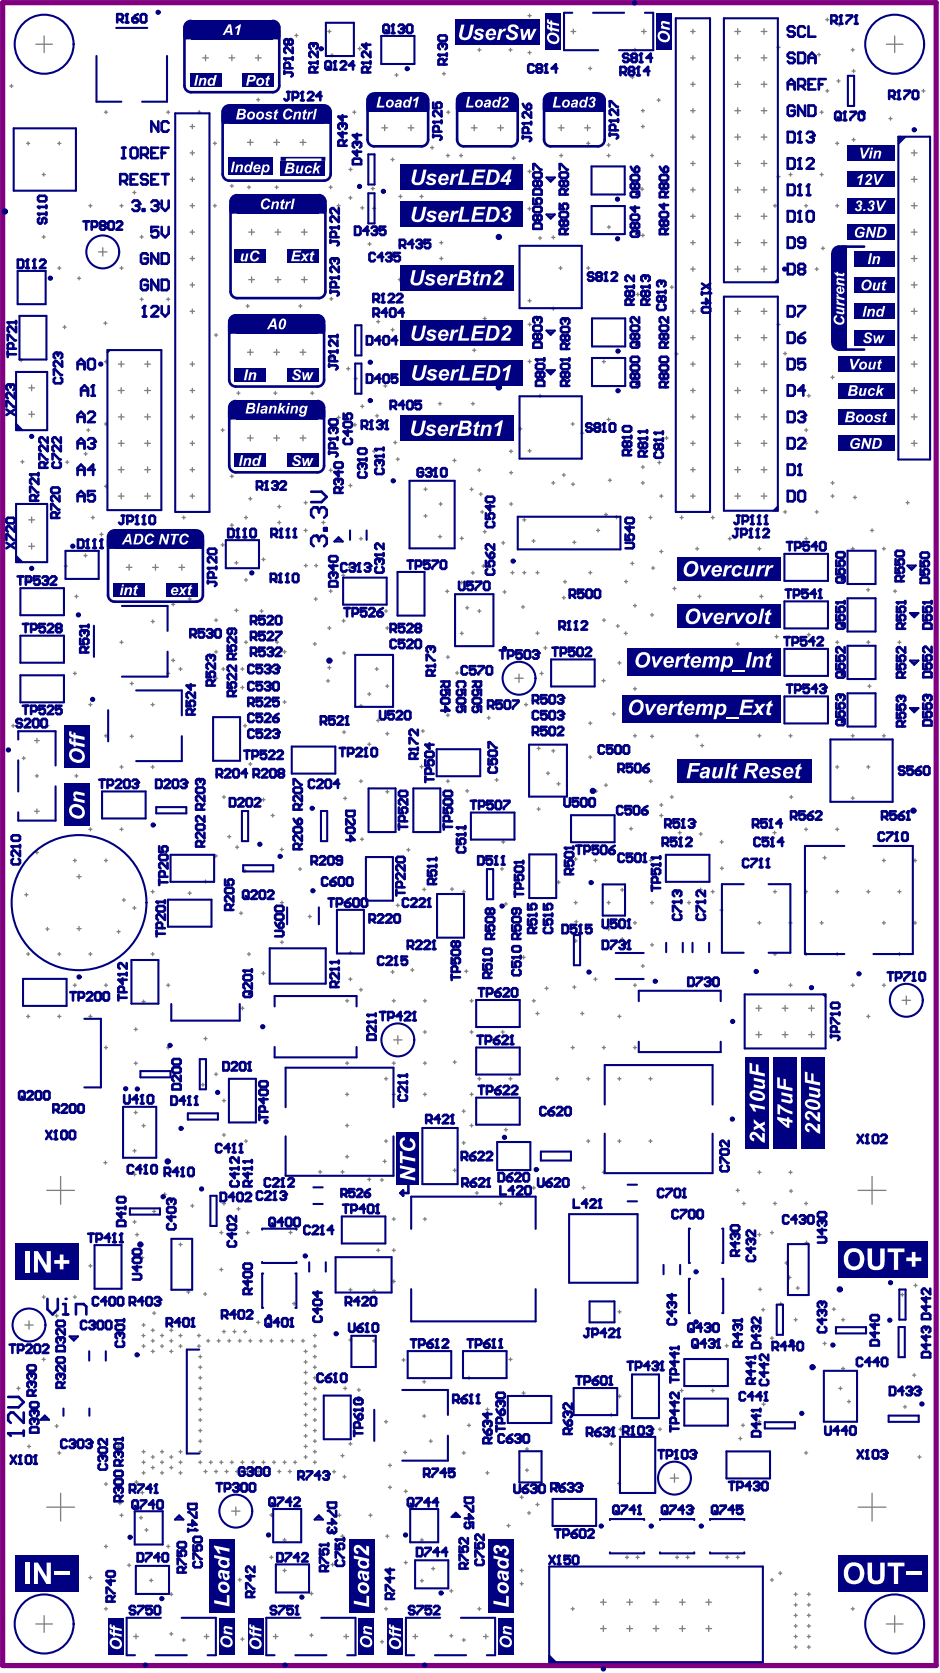
[picture p113: page 1]

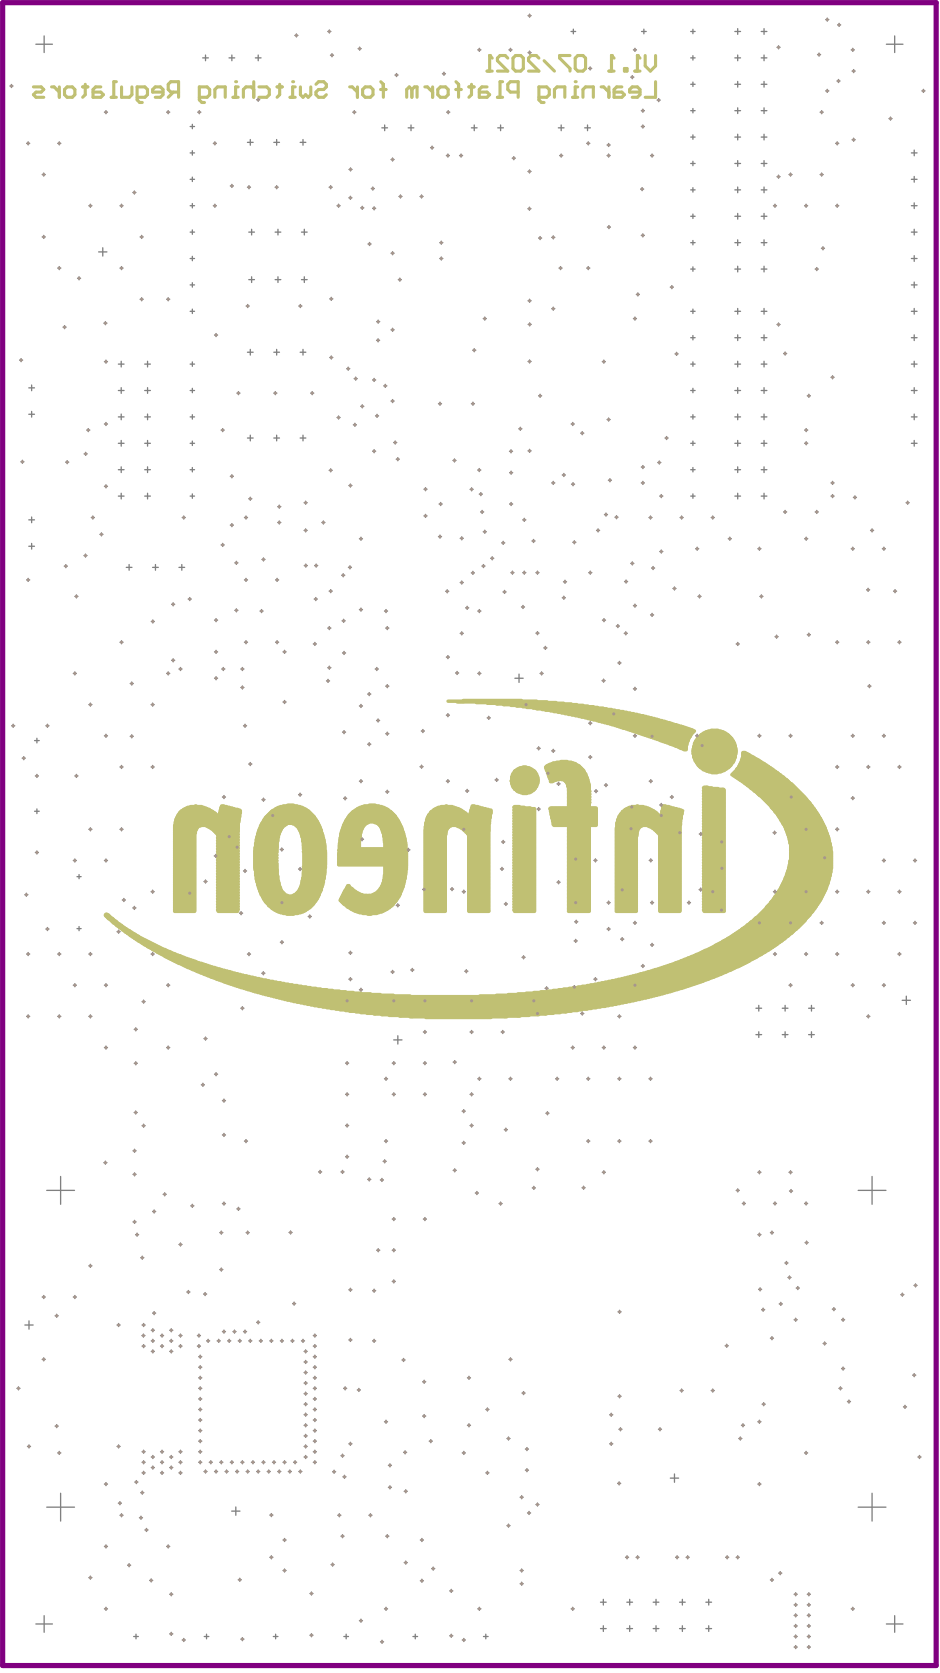
[picture p114: page 2]
