Infineon/voltage-regulator-learning-platform/Version1.2/Project Outputs/PDF/Silkmask.PDF

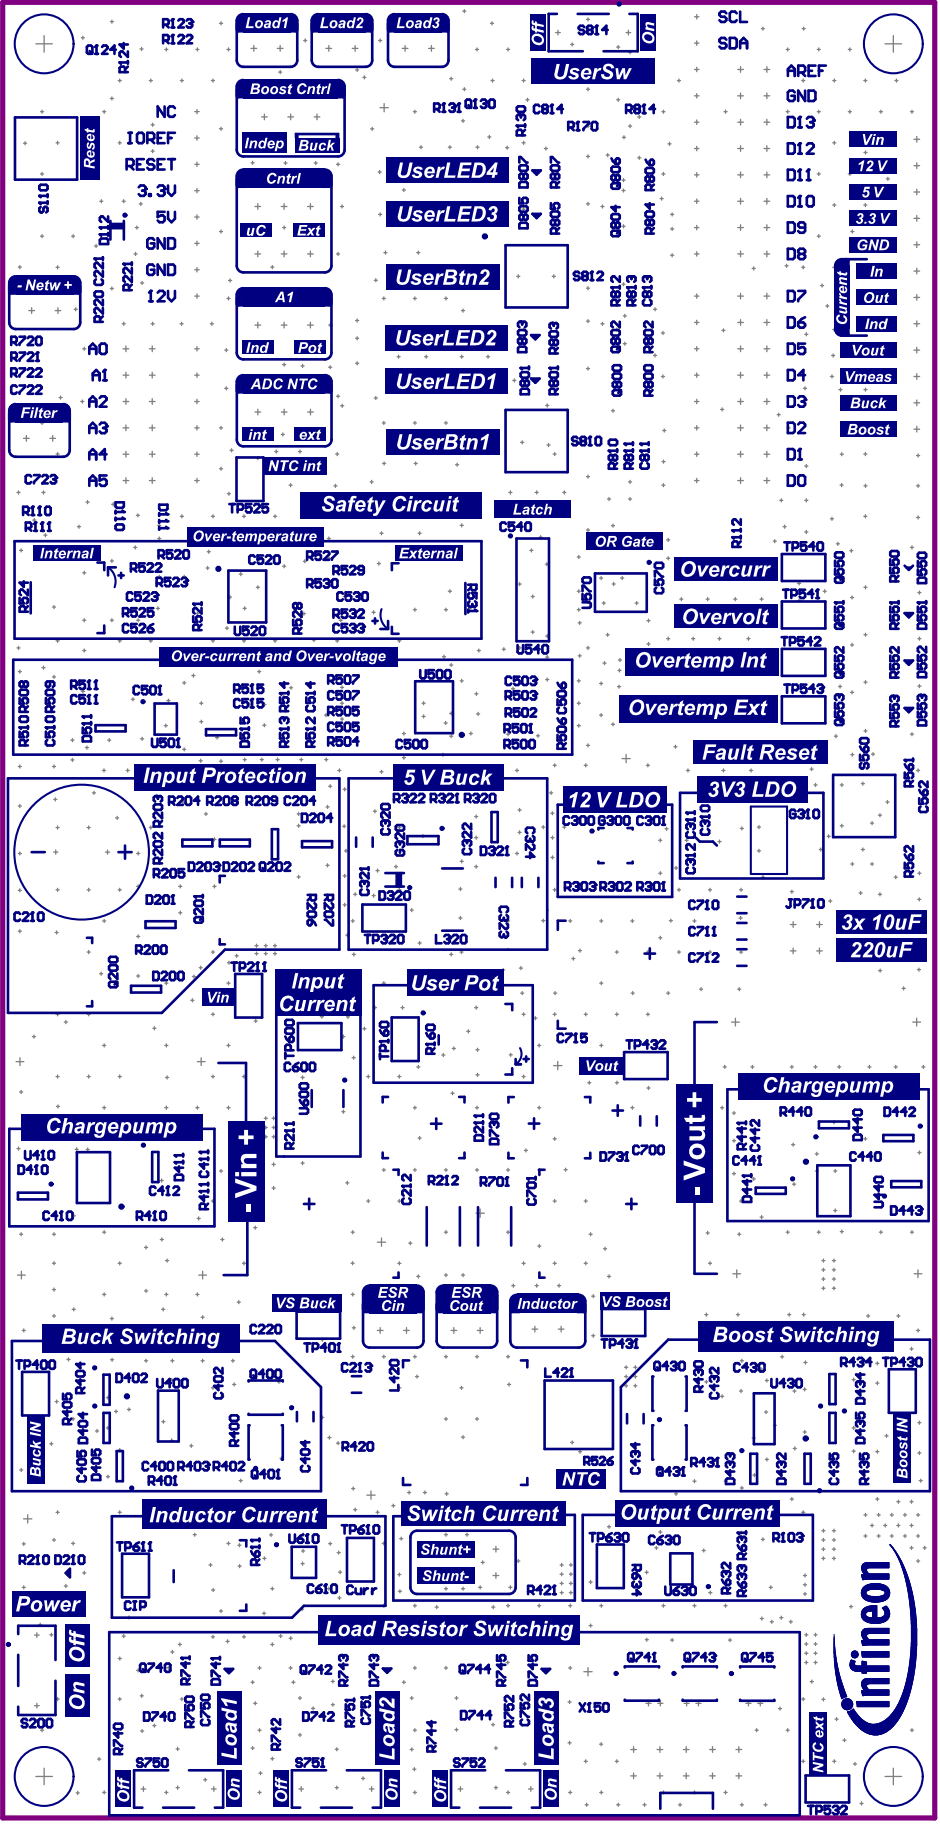
[picture p115: page 1]

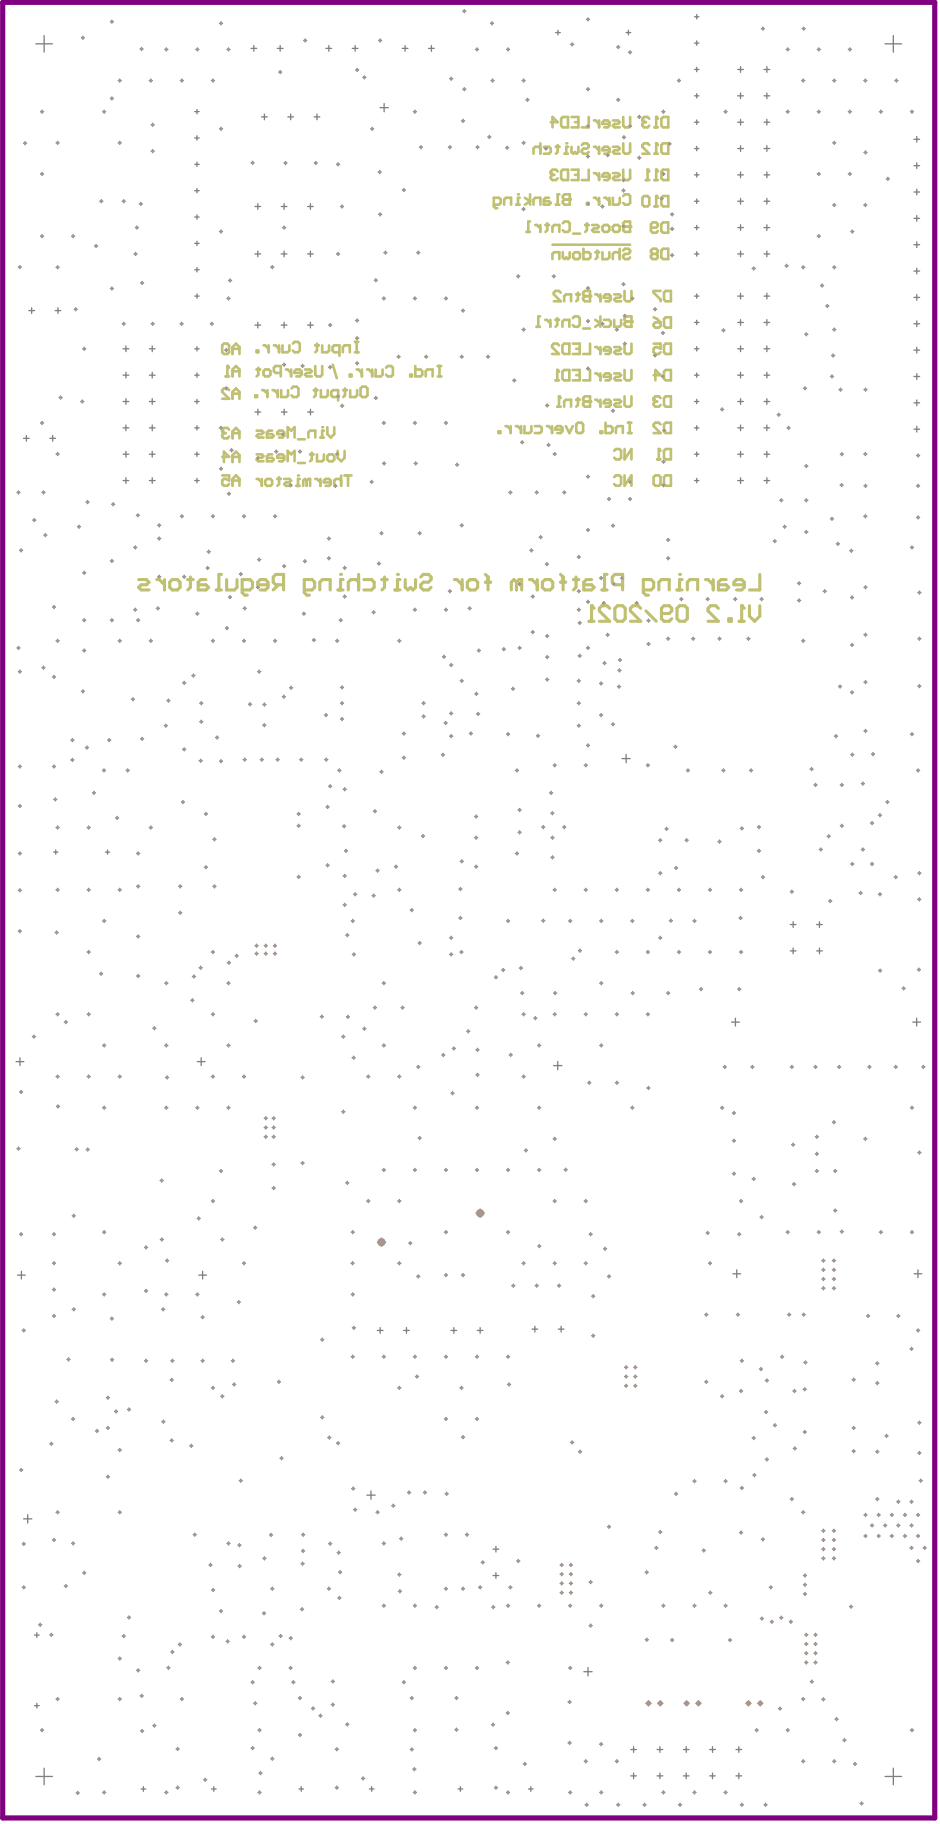
[picture p116: page 2]
