Infineon/voltage-regulator-learning-platform/Simulations/555-Chargepump-Test-Boost-V1.1.asc

C1: cap; 100n; Rser=1
C3: cap; 100n; Rser=1
C5: cap; 1n; Rser=1
C6: cap; 10n; Rser=1
D1: diode; BAS70
D2: zener; BZX84C15VL
D3: diode; BAS70
D4: diode; BAS70
D5: diode; BAS70
D6: diode; BAS70
D7: zener; BZX84C15L
I1: current; 150µ
I2: current; 240µ
R3: res; 1.3k
R4: res; 47k
U3: ICM7555
V1: voltage; PULSE(0 15 0 20m 50n 50m 70m); Rser=1m
V2: voltage; 12
Named nets: 0, Vs, Vcc_555, VB, trig, out, Vss, 12V
.tran 0 20m 0.1m uic
Maximum quiescent VB 
supply current: 150u 
(normal 60u)
Maximum quiescent Vcc supply current: 300uA 
(normal 60uA)
.MODEL BAS70 D(IS=1.2n N=1.023 RS=25.5 XTI=2.5 EG=0.69
+ CJO=1.45p M=0.382 VJ=0.539 FC=0.5 TT=40.0p BV=72.0 IBV=10.0u)
VB-VS has to be > 9V, otherwise gate-driver might turn-off
ICM7555 Model from Maxim Integrated:
https://www.maximintegrated.com/content/dam/files/design/tools/modeling-simulation/spice/analog/clock-generation-distribution/ICM7555.lib
