Infineon/voltage-regulator-learning-platform/Simulations/Current-Filter.asc

C2: cap; 2.2µ
R2: res; 100k
V1: voltage; PULSE(1.5 3 1m 1n 1n 1 1)
Named nets: 0, VS, Curr
.tran 0 200m 2m
