Infineon/voltage-regulator-learning-platform/Simulations/Fault Reset.asc

C1: cap; 100n
R1: res; 100k
R2: res; 2.2k
S1: sw
V1: voltage; 3.3
V2: voltage; PULSE(0 2 1m 1u 1u 2m 10m)
Named nets: 0, Reset, Vx
.model SW SW(Ron=100m Roff=1Meg Vt=1V Vh=0.1)
.tran 20m
