Infineon/voltage-regulator-learning-platform/Simulations/Gate-Driver-TurnOn.asc

C1: cap; 2.2µ
C2: cap; 2.2µ
D1: diode; 1N914
D2: diode; 1N914
R1: res; 4.7k
R2: res; 4.7k
R3: res; 4.7k
R4: res; 2.2k
V1: voltage; 3.3V
V2: voltage; 5V
V3: voltage; 3.3V
V4: voltage; 3.3V
Named nets: 0, Charge1, Buck_In, Charge2, Boost_In
.ic V(Charge1)=0V
.tran 5m
.ic V(Charge2)=0V
