Infineon/voltage-regulator-learning-platform/Simulations/NTC-voltRange.asc

R1: res; 4.7k
R2: res; {NTC}
V1: voltage; 3.3
Named nets: 0
.step param NTC 3.5k 10k 100
.op
NTC=10k @ 20°C
3.5k @ 55°C
