Infineon/voltage-regulator-learning-platform/Simulations/OvervoltageProtection-New-NEW-NEW.asc

D1: zener; BZX84C10VL
D4: zener; BZX84C10VL
M1: pmos; IRF9Z24S_L
M2: pmos; BSS84
R1: res; 47k
R2: res; 100
R3: res; 47k
R4: res; 47k
R5: res; 64.9K
R6: res; 1000k
R8: res; 64.9K
R11: res; 17.8k
U2: ATL431A_TRANS
V1: voltage; PULSE(10 22v 0 500m 500m 200m 2000m)
Named nets: 0, Vin, Vout, Gate_pwr, Gate_pmos, Zener_Overvolt, M1GATE
.tran 1200m
.inc tl431.sub
.step param R 200k 2000k 100k
