Infineon/voltage-regulator-learning-platform/Simulations/OvervoltageProtection-New-NEW.asc

D1: zener; BZX84C10VL
D4: zener; BZX84C10VL
M1: pmos; IRF9Z24S_L
M2: pmos; BSS84
R1: res; 47k
R2: res; 100
R3: res; 47k
R4: res; 47k
R6: res; 2000000
R10: res; 220k
R11: res; 47K
U1: TL431
V1: voltage; PULSE(10 60v 0 500m 500m 200m 2000m)
Named nets: 0, Vin, Vout, Gate_pwr, Gate_pmos, Zener_Overvolt, M1GATE
.tran 1200m
.inc tl431.sub
