Infineon/voltage-regulator-learning-platform/Simulations/OvervoltageProtection-New.asc

D1: zener; BZX84C10VL
D4: zener; BZX84C10VL
M1: pmos; IRF9Z24S_L
M2: pmos; BSS84
R1: res; 47k
R2: res; 100
R3: res; 47k
R4: res; 47k
R6: res; 470k
R10: res; 100k
R11: res; 13k
U2: ATL431A_TRANS
V1: voltage; PULSE(10 23 0 500m 500m 200m 2000m)
Named nets: 0, Vin, Vout, Gate_pwr, Gate_pmos, Zener_Overvolt
.tran 1200m
