Infineon/voltage-regulator-learning-platform/Simulations/OvervoltageProtection.asc

D1: zener; BZX84C10VL
D2: zener; BZX84C20VL
D3: zener; KDZ20B
D4: zener; BZX84C10VL
D5: zener; MMBZ20VAL
M1: pmos; Si7461DP
M2: pmos; BSS84
R1: res; 47k
R2: res; 10
R3: res; 47k
R4: res; 47k
V1: voltage; 20
Named nets: 0, Vin, Vout, Gate_pwr, Gate_logic, Zener_In
;op
.dc V1 15 26 0.1
