Infineon/voltage-regulator-learning-platform/Simulations/OvervoltageUndervoltageCombinedATL431.asc

C1: cap; 10n
D1: zener; BZX84C10VL
D2: zener; BZX84C20VL
D4: zener; BZX84C10VL
M1: pmos; IRF9Z24S_L
M2: pmos; BSS84
R1: res; 47k
R2: res; 100
R3: res; 47k
R4: res; 47k
R5: res; 2Meg
R6: res; 2Meg
R7: res; 47k
R8: res; 64.9k
R9: res; 17.8k
U1: ATL431A_TRANS
V1: voltage; PULSE(10 23 0 500m 500m 200m 2000m)
Named nets: 0, Vin, Vout, Gate_pwr, Gate_pmos, Zener_Overvolt, Cathode
;op
;dc V1 10 12 0.005
.tran 1200m
PULSE(20 23 0 50m 50m 20m 200m)
