Infineon/voltage-regulator-learning-platform/Simulations/OvervoltageUndervoltageCombinedTL431.asc

D1: zener; BZX84C10VL
D2: zener; BZX84C20VL
D3: zener; KDZ20B
D4: zener; BZX84C10VL
D5: zener; MMBZ20VAL
M1: pmos; Si7461DP
M2: pmos; BSS84
R1: res; 5k
R2: res; 100
R3: res; 47k
R4: res; 47k
R7: res; 5k
R8: res; 68k
R9: res; 20k
U1: TL431
V1: voltage; 15
Named nets: 0, Vin, Vout, Gate_pwr, Gate_pmos, Zener_Overvolt, Cathode
;op
.dc V1 10 12 0.005
;tran 100ns
